dekuNukem/USB4VC/captures/m0110/tmk_firrmware_hhkb_teensy2_m0110.c at master · altercation_tmk_firrmware_hhkb_teensy2_files/9824478.png

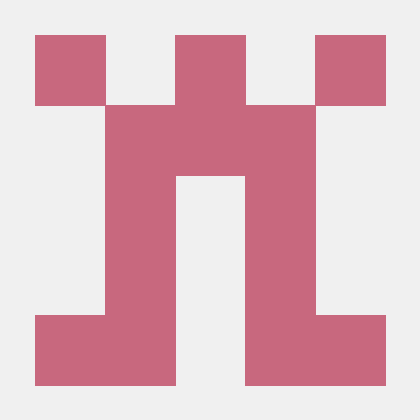
captures/m0110/tmk_firrmware_hhkb_teensy2_m0110.c at master · altercation_tmk_firrmware_hhkb_teensy2_files/9824478.png
