dekuNukem/USB4VC/firmware/apple_lisa_mac_adb/lisa_keycode.png

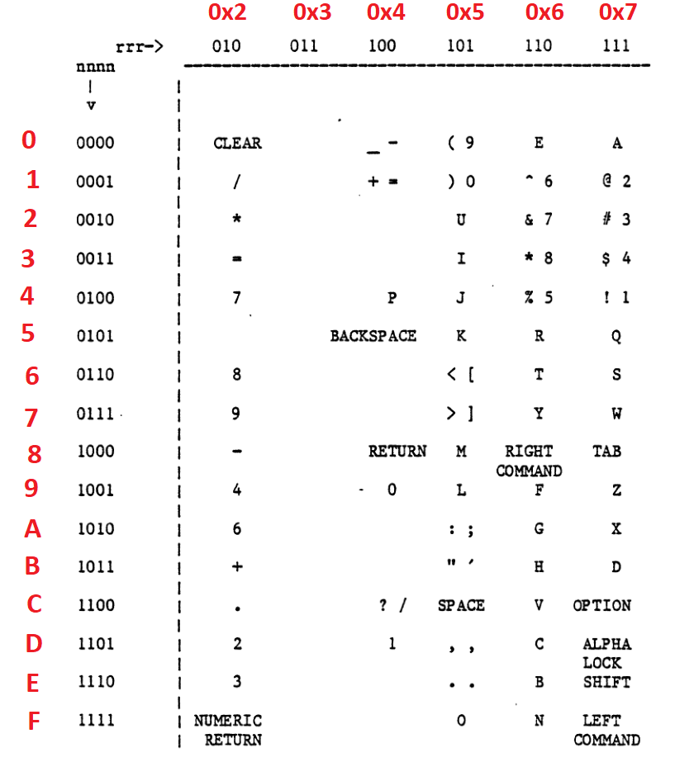
firmware/apple_lisa_mac_adb/lisa_keycode.png
