dekuNukem/USB4VC/pcb/plates/dimension photo.png

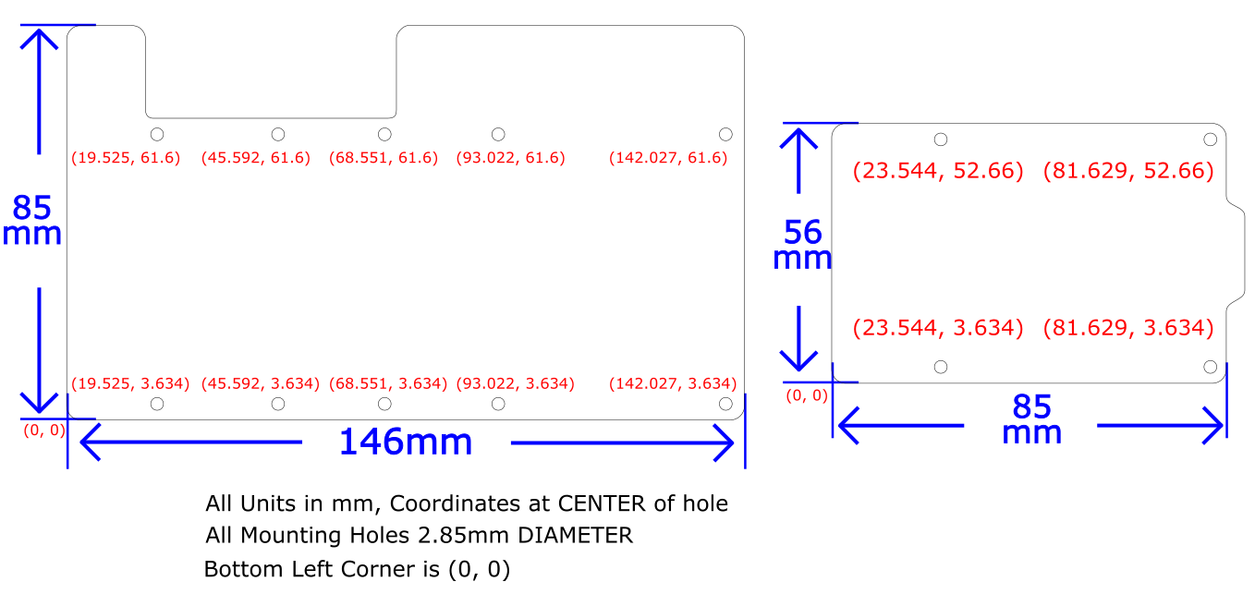
pcb/plates/dimension photo.png
