dekuNukem/USB4VC/photos/'8042' PS_2 Controller - OSDev Wiki_files/At-kbc.png

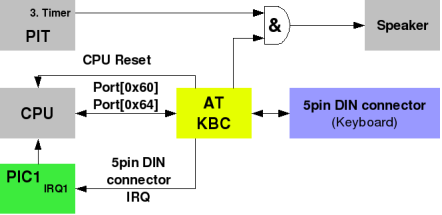
photos/'8042' PS_2 Controller - OSDev Wiki_files/At-kbc.png
