dekuNukem/USB4VC/photos/adbpc.jpeg

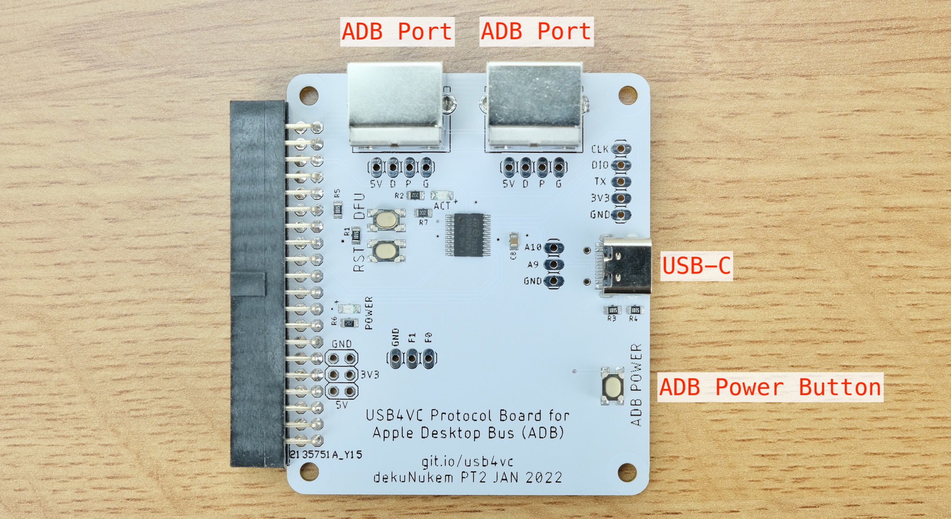
photos/adbpc.jpeg
