dekuNukem/USB4VC/photos/bbadb.jpeg

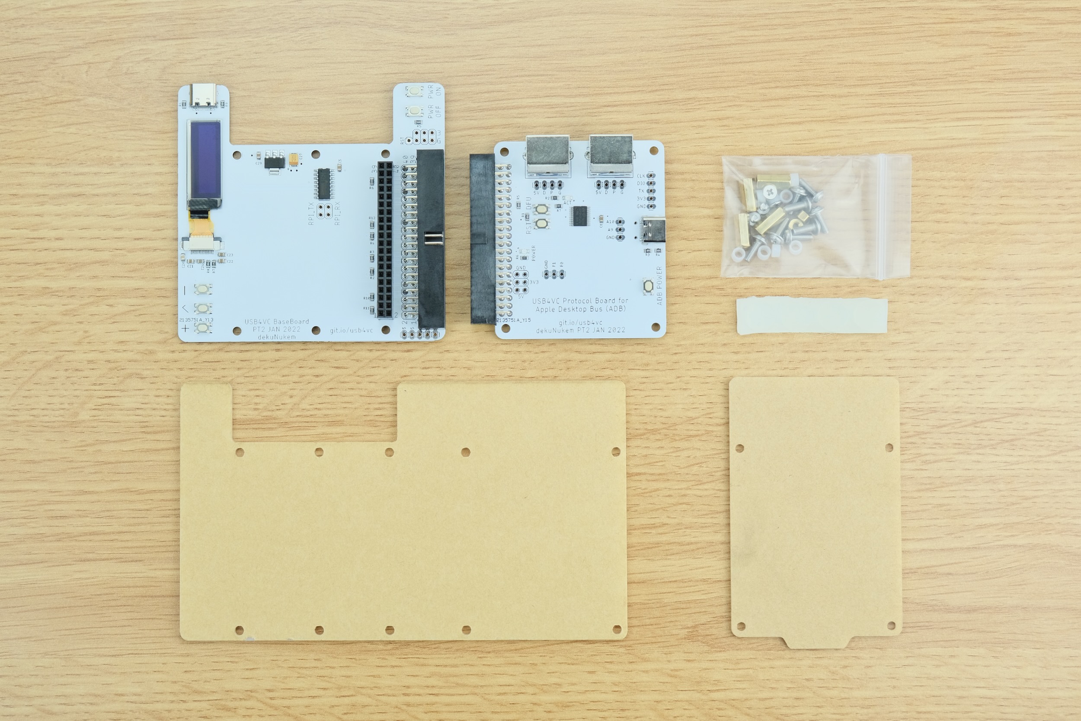
photos/bbadb.jpeg
