dekuNukem/USB4VC/photos/bbpc.jpeg

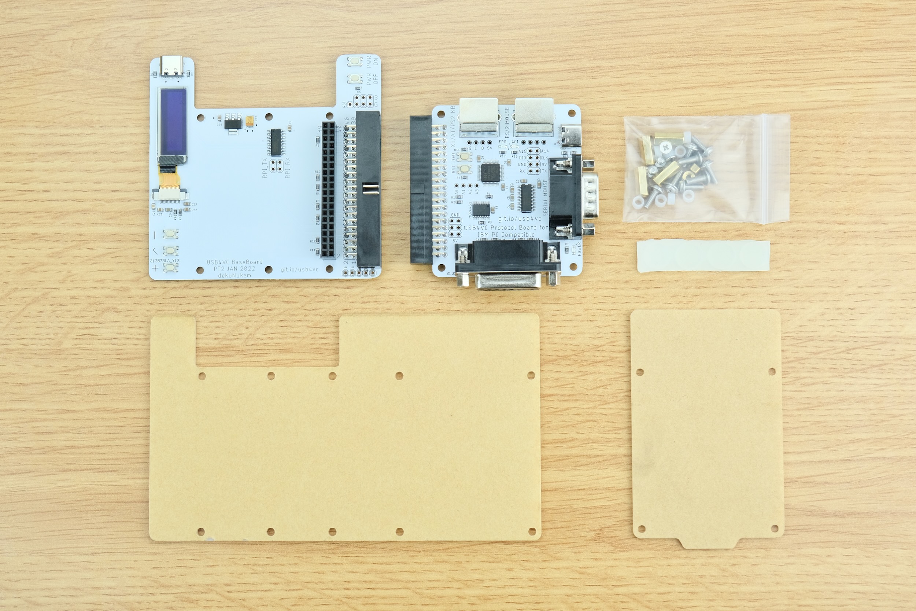
photos/bbpc.jpeg
