dekuNukem/USB4VC/photos/bbpcadb.jpeg

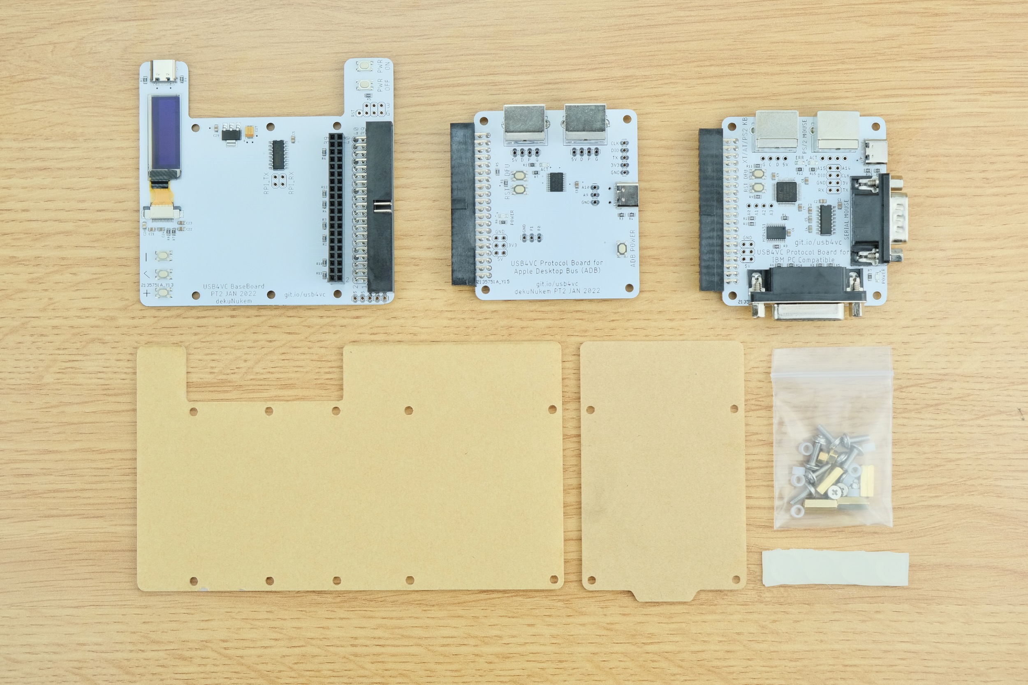
photos/bbpcadb.jpeg
