dekuNukem/USB4VC/photos/macclassic.jpeg

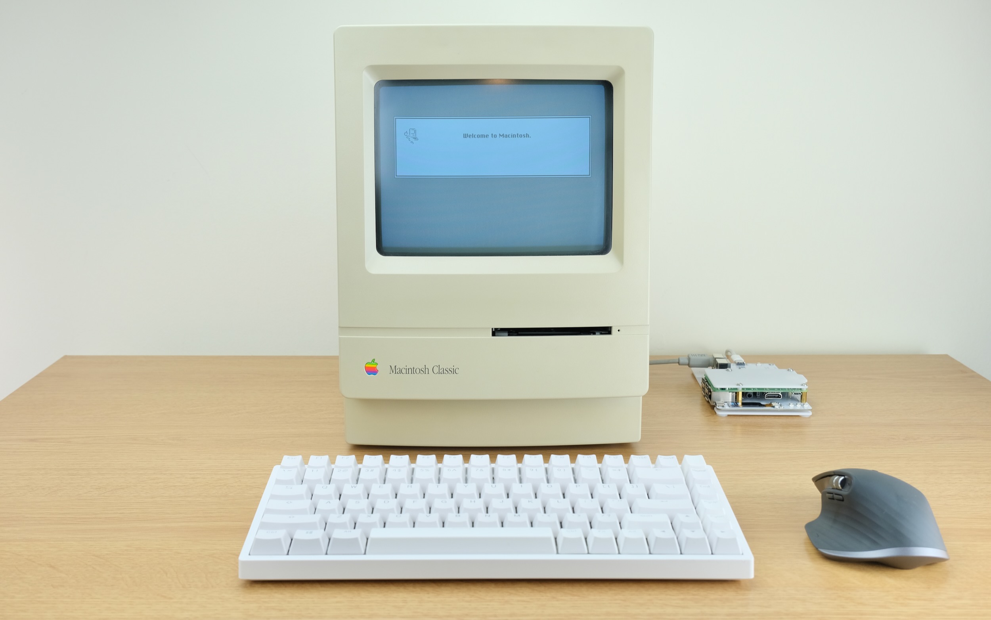
photos/macclassic.jpeg
