dekuNukem/USB4VC/photos/rpitest.jpeg

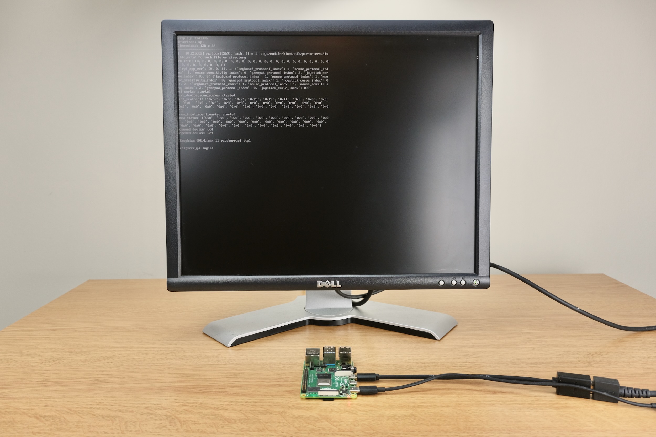
photos/rpitest.jpeg
