dekuNukem/USB4VC/photos/usbdisk.png

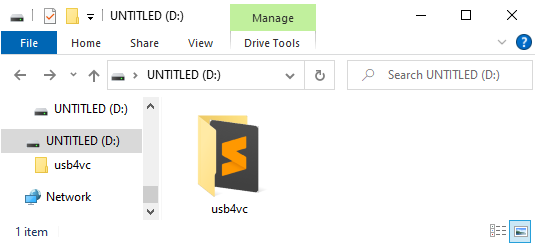
photos/usbdisk.png
