dekuNukem/USB4VC/photos/usboled.jpeg

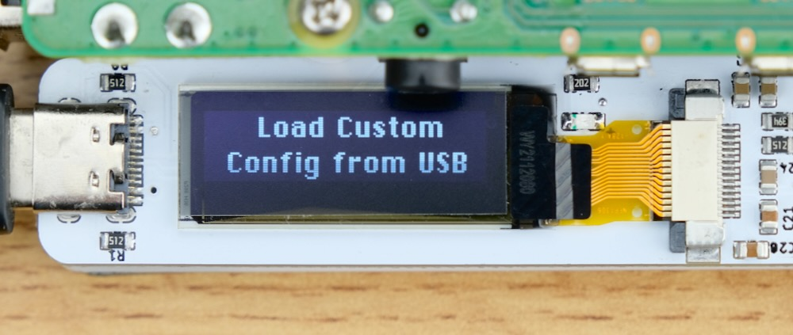
photos/usboled.jpeg
