dekuNukem/USB4VC/photos/video_thumb.png

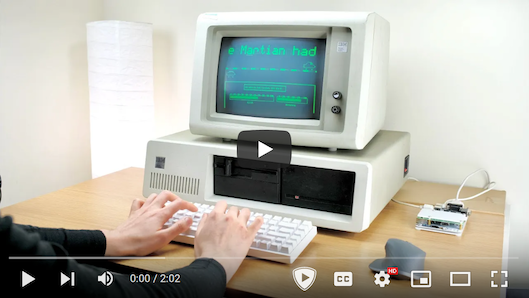
photos/video_thumb.png
