dekuNukem/USB4VC/photos/xbupdate.png

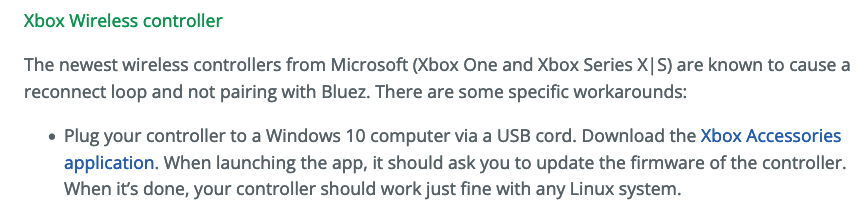
photos/xbupdate.png
