dekuNukem/USB4VC/resources/bezier curve - Inverse round corners with Inkscape - Graphic Design Stack Exchange_files/bnUZU.jpg

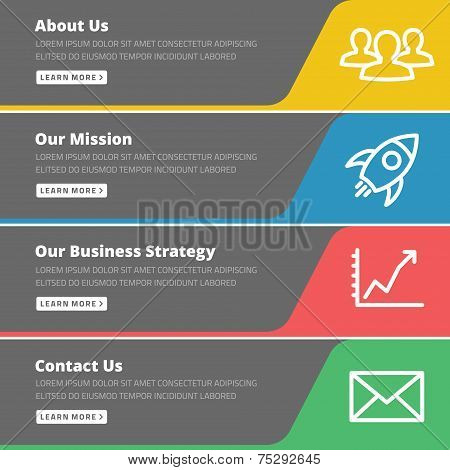
resources/bezier curve - Inverse round corners with Inkscape - Graphic Design Stack Exchange_files/bnUZU.jpg
