dekuNukem/USB4VC/resources/IBM 1390876 keyboard_files/1390876.jpg

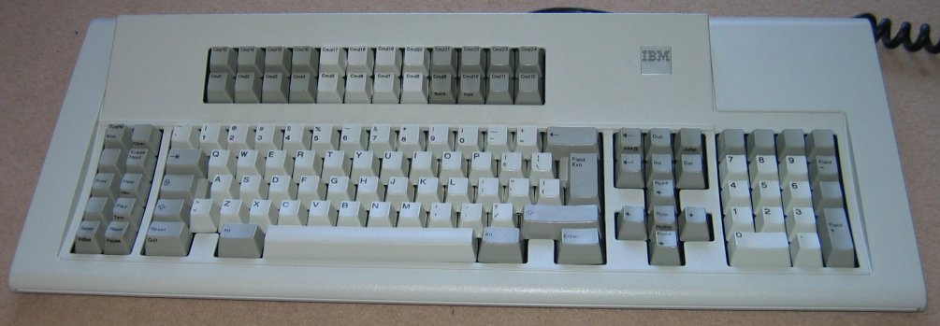
resources/IBM 1390876 keyboard_files/1390876.jpg
