dekuNukem/USB4VC/resources/IBM 1397000 keyboard_files/1397000.jpg

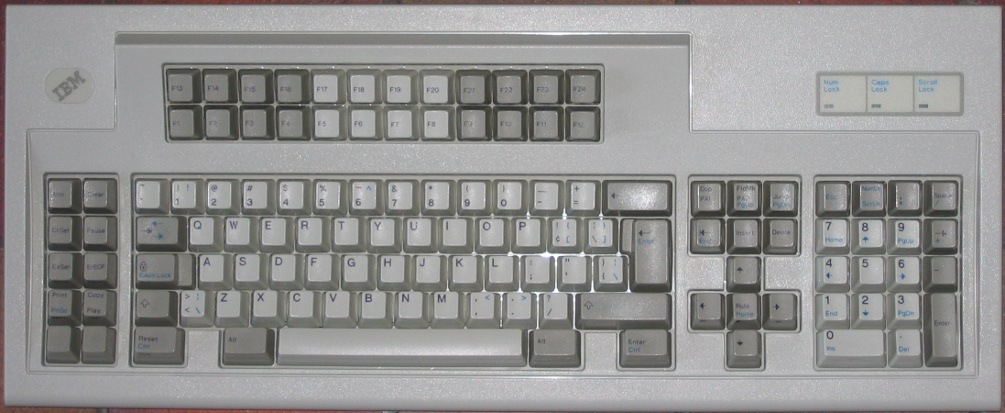
resources/IBM 1397000 keyboard_files/1397000.jpg
