dekuNukem/USB4VC/resources/IBM PC AT Keyboard Protocol · tmk_tmk_keyboard Wiki_files/687474703a2f2f7a6967736f772e6a702f696d672e7068703f613d612666.jpg

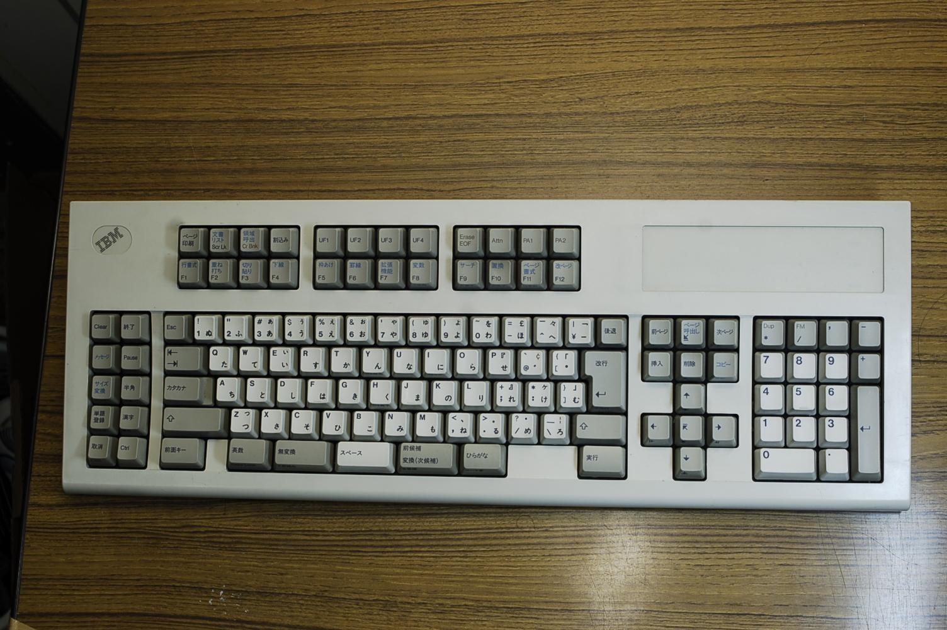
resources/IBM PC AT Keyboard Protocol · tmk_tmk_keyboard Wiki_files/687474703a2f2f7a6967736f772e6a702f696d672e7068703f613d612666.jpg
