dekuNukem/USB4VC/resources/IBM PC AT Keyboard Protocol · tmk_tmk_keyboard Wiki_files/687474703a2f2f626c6f672d696d67732d37352e6663322e636f6d2f6b2f.jpg

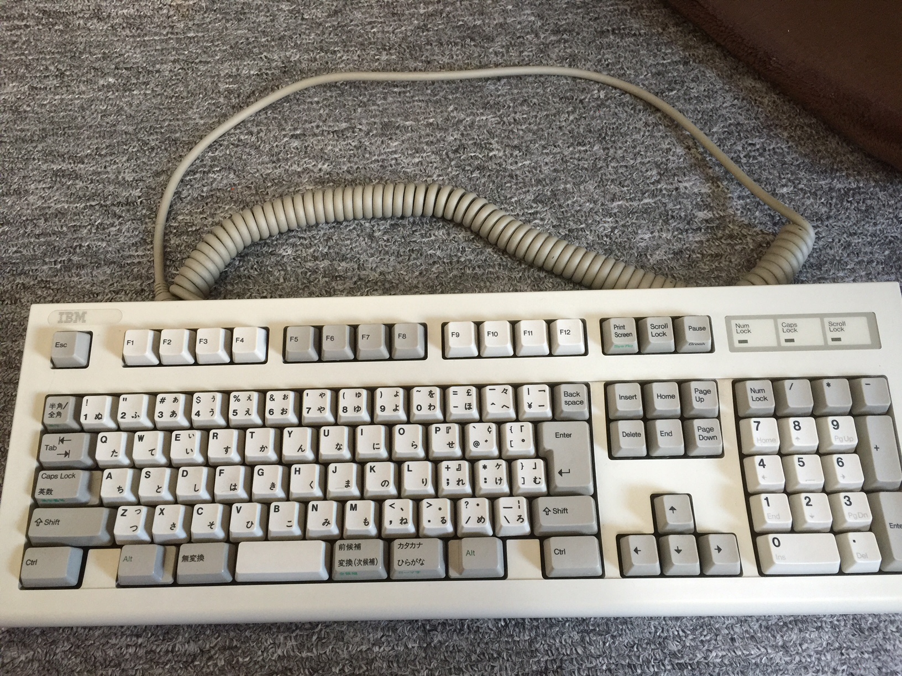
resources/IBM PC AT Keyboard Protocol · tmk_tmk_keyboard Wiki_files/687474703a2f2f626c6f672d696d67732d37352e6663322e636f6d2f6b2f.jpg
