dekuNukem/USB4VC/resources/IBM PC AT Keyboard Protocol · tmk_tmk_keyboard Wiki_files/687474703a2f2f7777772e6b6264626162656c2e6f72672f7369676e616c.png

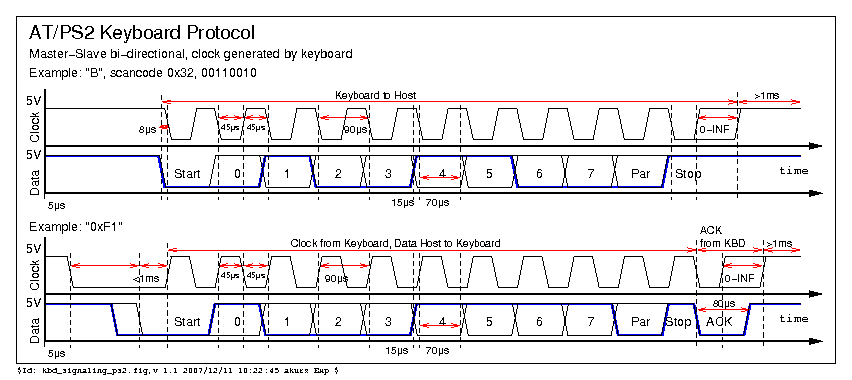
resources/IBM PC AT Keyboard Protocol · tmk_tmk_keyboard Wiki_files/687474703a2f2f7777772e6b6264626162656c2e6f72672f7369676e616c.png
