dekuNukem/USB4VC/resources/IBM PC AT Keyboard Protocol · tmk_tmk_keyboard Wiki_files/68747470733a2f2f692e696d6775722e636f6d2f34374b734c534c2e706e.png

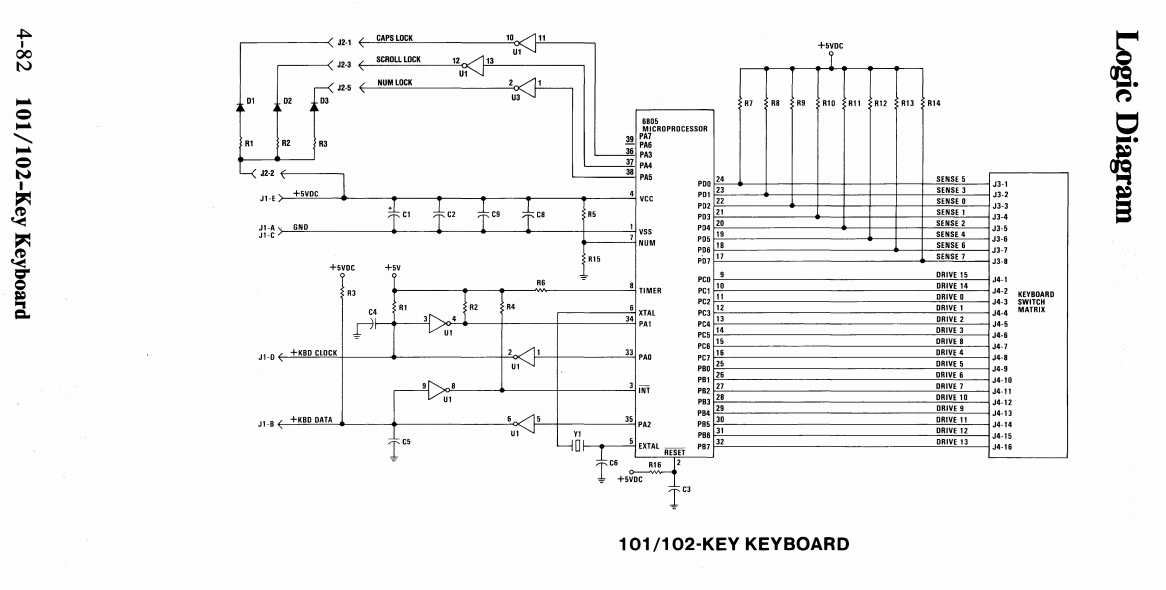
resources/IBM PC AT Keyboard Protocol · tmk_tmk_keyboard Wiki_files/68747470733a2f2f692e696d6775722e636f6d2f34374b734c534c2e706e.png
