dekuNukem/USB4VC/resources/IBM PC AT Keyboard Protocol · tmk_tmk_keyboard Wiki_files/68747470733a2f2f75706c6f61642e77696b696d656469612e6f72672f77.jpg

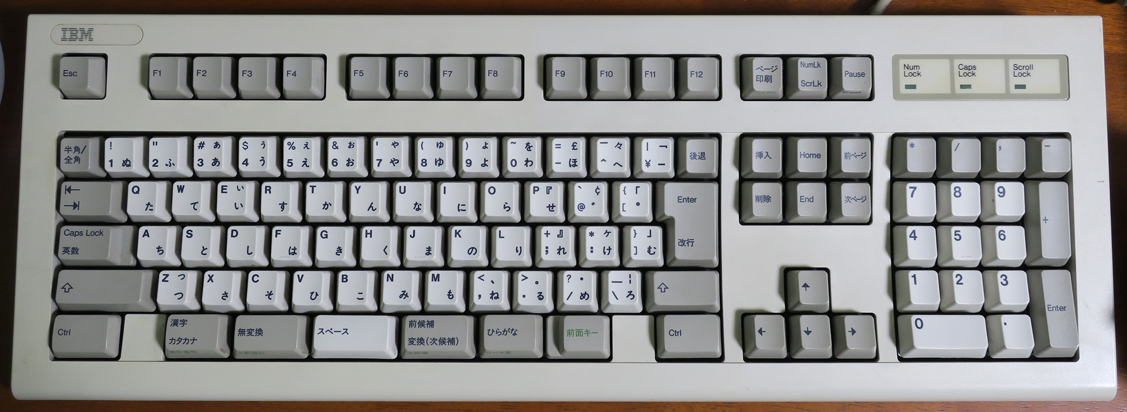
resources/IBM PC AT Keyboard Protocol · tmk_tmk_keyboard Wiki_files/68747470733a2f2f75706c6f61642e77696b696d656469612e6f72672f77.jpg
