dekuNukem/USB4VC/resources/IBM PC AT Keyboard Protocol · tmk_tmk_keyboard Wiki_files/68747470733a2f2f7062732e7477696d672e636f6d2f6d656469612f454f.jpg

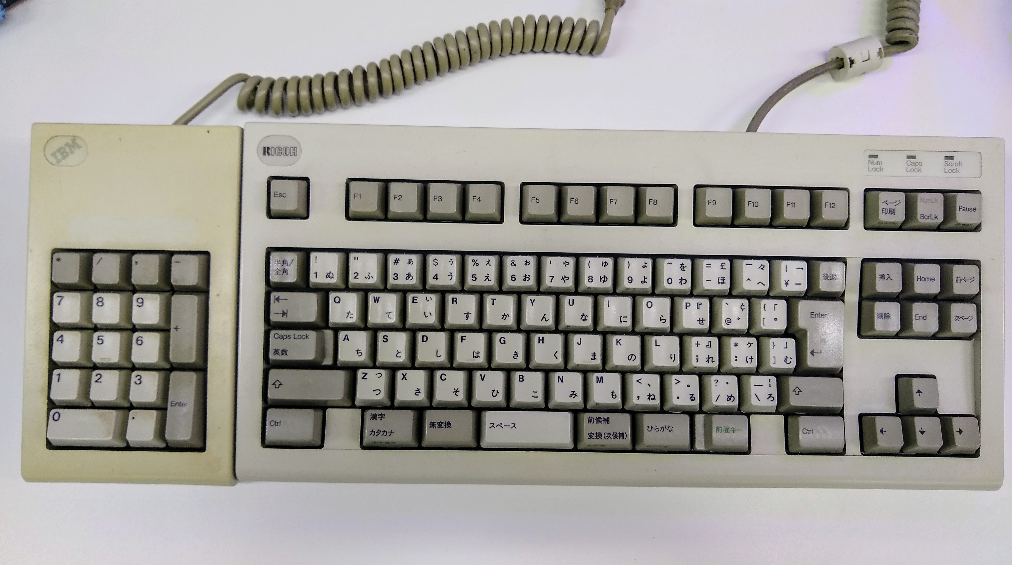
resources/IBM PC AT Keyboard Protocol · tmk_tmk_keyboard Wiki_files/68747470733a2f2f7062732e7477696d672e636f6d2f6d656469612f454f.jpg
