dekuNukem/USB4VC/resources/index_files/reconbot.png

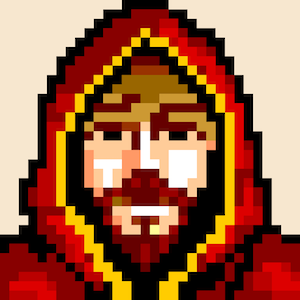
resources/index_files/reconbot.png
