dekuNukem/USB4VC/resources/lichee pi pinout.png

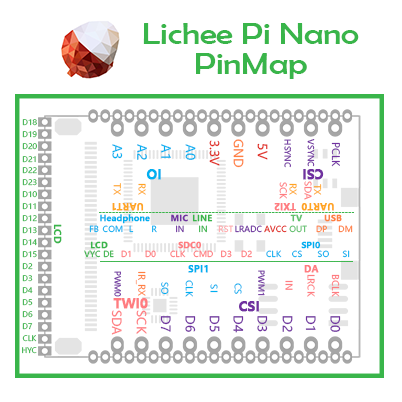
resources/lichee pi pinout.png
