dekuNukem/USB4VC/resources/O1CN01AOr2Mo1PcqBe09GLz_!!914671862.jpg

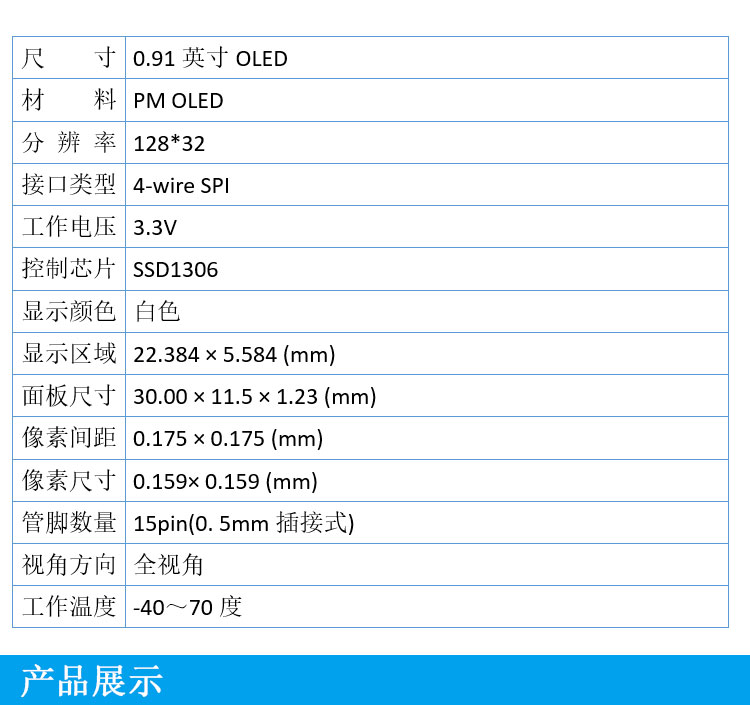
resources/O1CN01AOr2Mo1PcqBe09GLz_!!914671862.jpg
