dekuNukem/USB4VC/resources/png_to_curve/bitmap.png

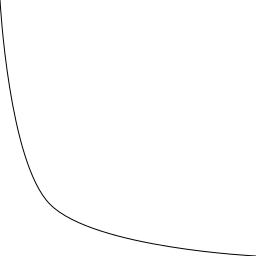
resources/png_to_curve/bitmap.png
