dekuNukem/USB4VC/resources/png_to_curve/ccc.png

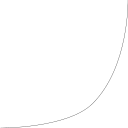
resources/png_to_curve/ccc.png
