dekuNukem/USB4VC/resources/Raspberry-Pi-1-2-3-Model-B.jpg

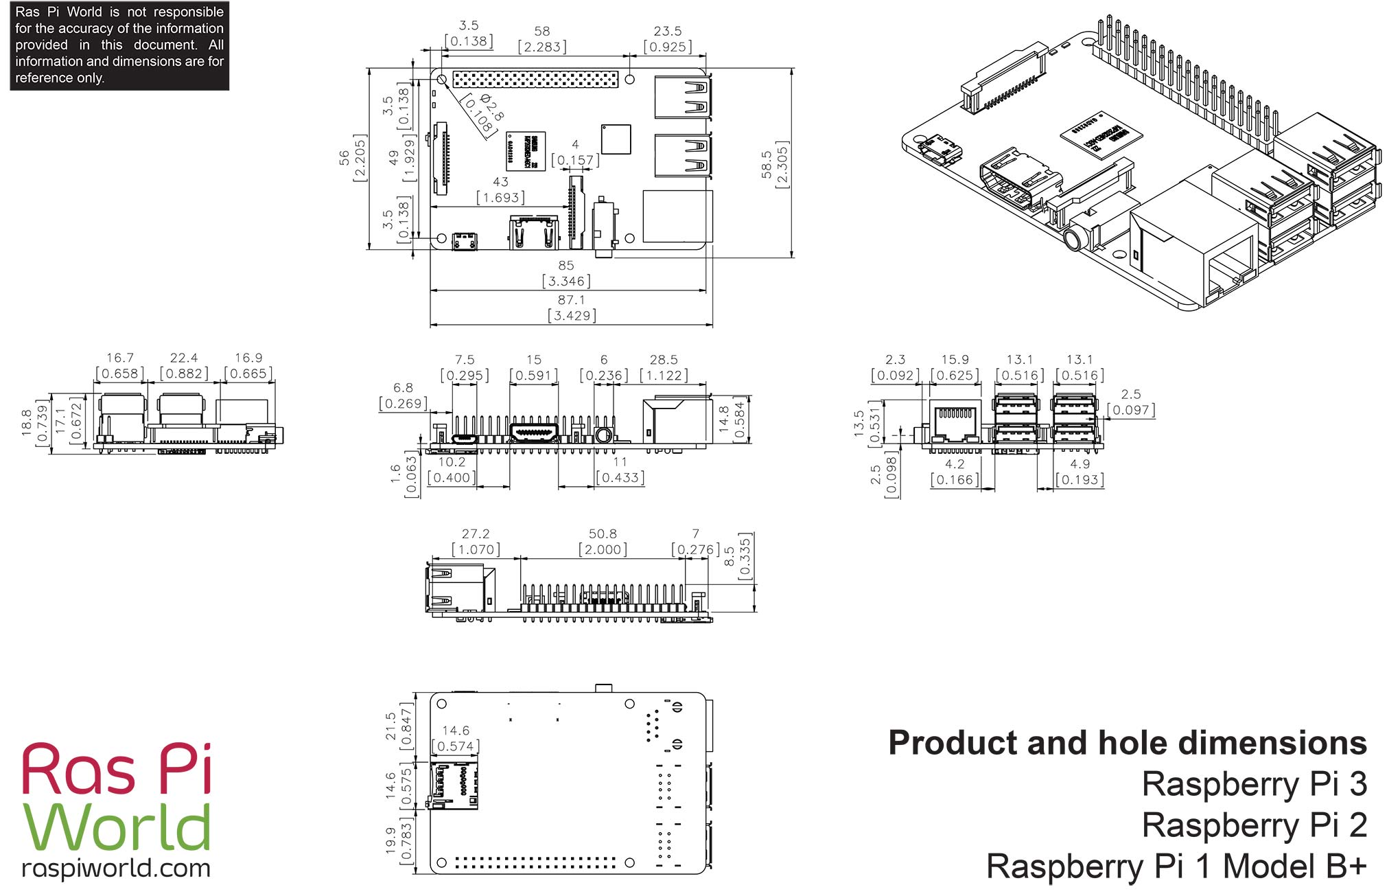
resources/Raspberry-Pi-1-2-3-Model-B.jpg
