dekuNukem/USB4VC/resources/Scan Codes Demystified_files/83c.gif

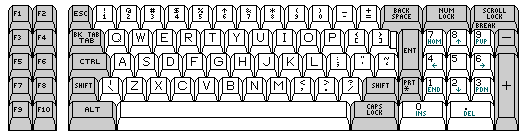
resources/Scan Codes Demystified_files/83c.gif
