dekuNukem/USB4VC/resources/Scan Codes Demystified_files/84c.gif

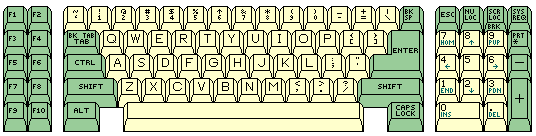
resources/Scan Codes Demystified_files/84c.gif
