dekuNukem/USB4VC/resources/Scan Codes Demystified_files/122_apl.gif

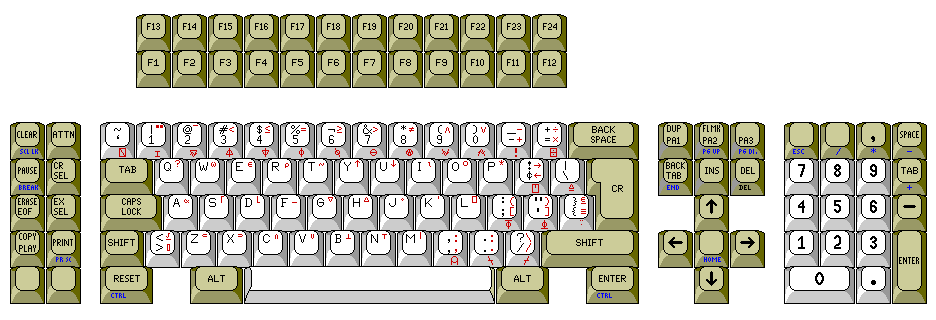
resources/Scan Codes Demystified_files/122_apl.gif
