dekuNukem/USB4VC/resources/Scan Codes Demystified_files/122hc.gif

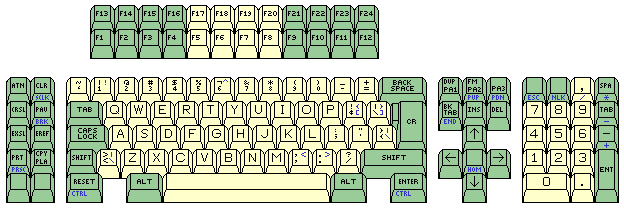
resources/Scan Codes Demystified_files/122hc.gif
