dekuNukem/USB4VC/resources/Scan Codes Demystified_files/122j.gif

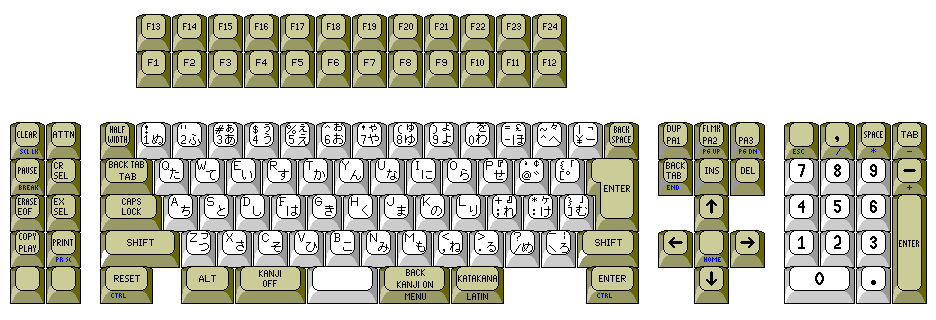
resources/Scan Codes Demystified_files/122j.gif
