dekuNukem/USB4VC/resources/Scan Codes Demystified_files/3270e.gif

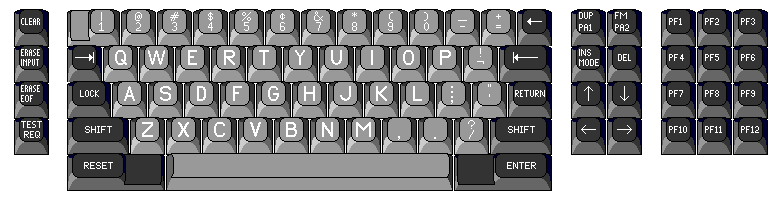
resources/Scan Codes Demystified_files/3270e.gif
