dekuNukem/USB4VC/resources/Scan Codes Demystified_files/memx122.jpg

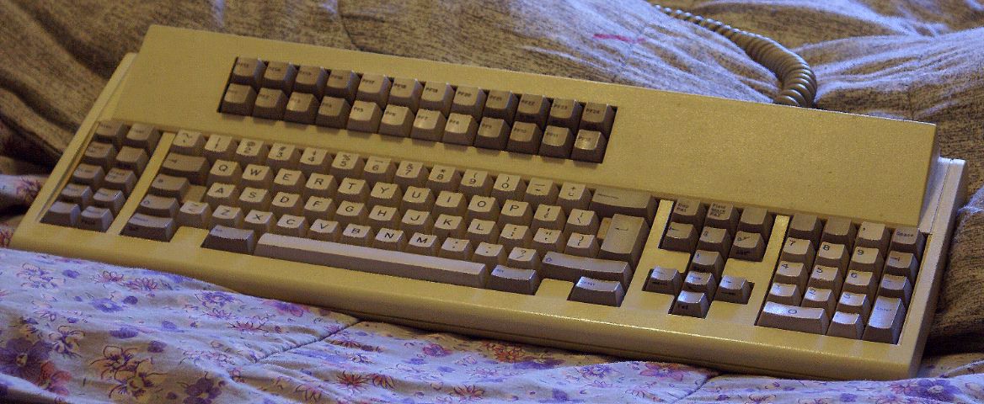
resources/Scan Codes Demystified_files/memx122.jpg
