dekuNukem/USB4VC/resources/Scan Codes Demystified_files/pca70.gif

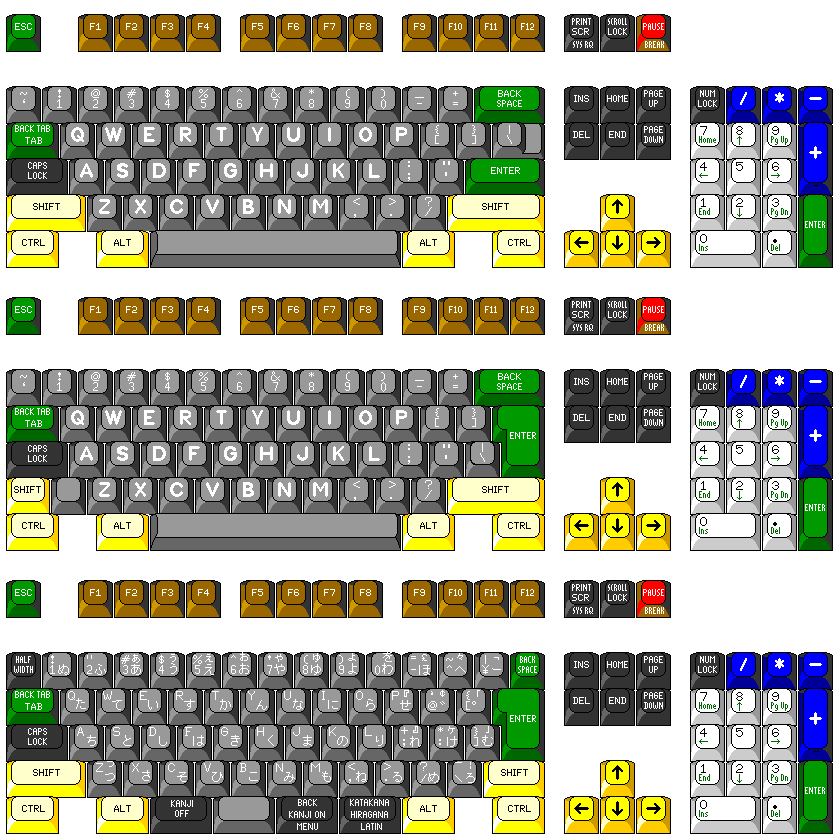
resources/Scan Codes Demystified_files/pca70.gif
