dekuNukem/USB4VC/resources/Scan Codes Demystified_files/pca72.gif

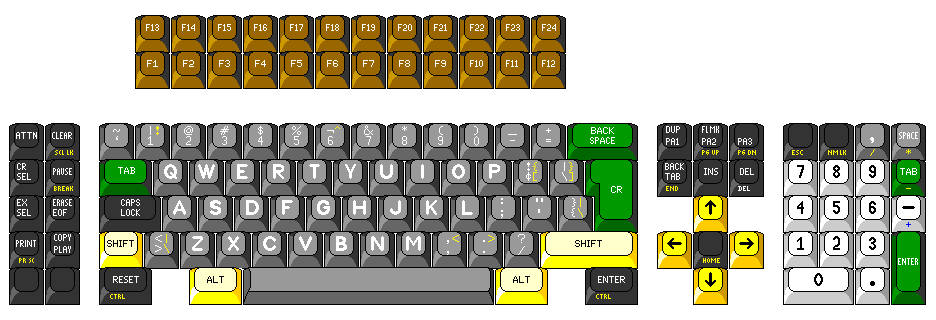
resources/Scan Codes Demystified_files/pca72.gif
