dekuNukem/USB4VC/resources/Scan Codes Demystified_files/ssk.gif

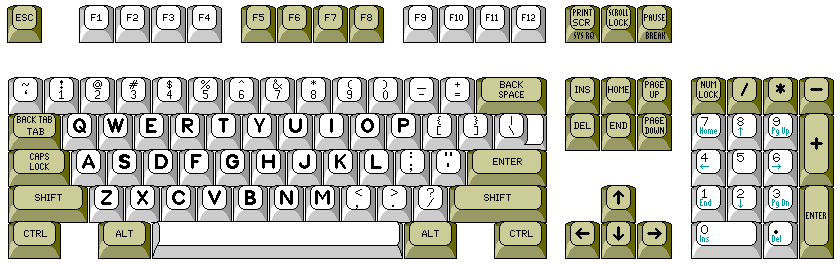
resources/Scan Codes Demystified_files/ssk.gif
