dekuNukem/USB4VC/resources/Screenshot_from_2019-06-25_14-10-06_d96020f3-4f37-48f7-af61-e2e9a573ea04.webp

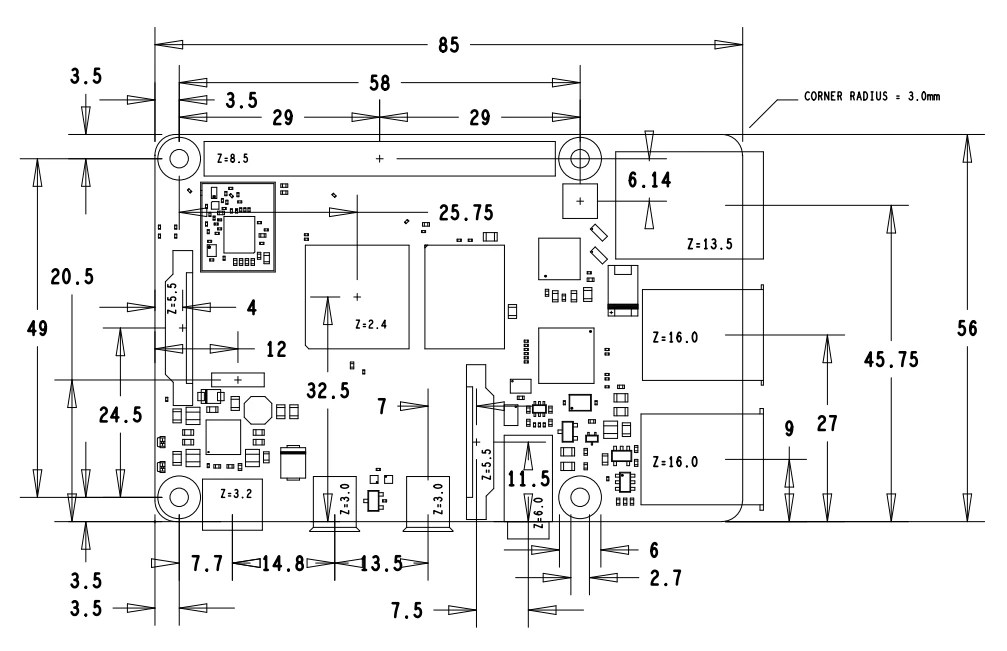
resources/Screenshot_from_2019-06-25_14-10-06_d96020f3-4f37-48f7-af61-e2e9a573ea04.webp
