dekuNukem/USB4VC/resources/The PS_2 Mouse_Keyboard Protocol_files/ps2.JPG

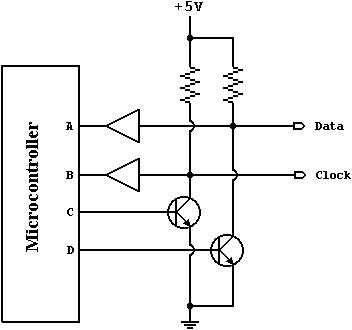
resources/The PS_2 Mouse_Keyboard Protocol_files/ps2.JPG
