dekuNukem/USB4VC/resources/The PS_2 Mouse_Keyboard Protocol_files/qscope.JPG

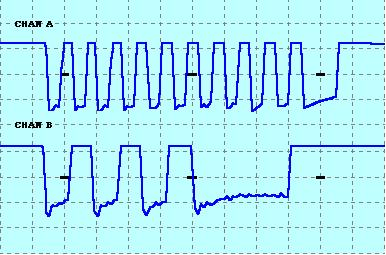
resources/The PS_2 Mouse_Keyboard Protocol_files/qscope.JPG
