dekuNukem/USB4VC/resources/The PS_2 Mouse_Keyboard Protocol_files/waveform1.jpg

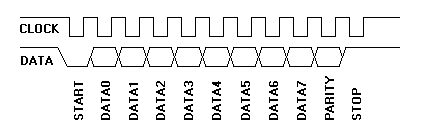
resources/The PS_2 Mouse_Keyboard Protocol_files/waveform1.jpg
