dekuNukem/USB4VC/resources/The PS_2 Mouse_Keyboard Protocol_files/waveform2.jpg

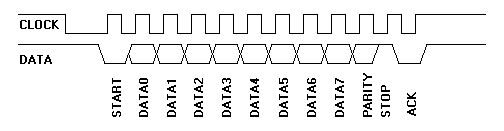
resources/The PS_2 Mouse_Keyboard Protocol_files/waveform2.jpg
