dekuNukem/USB4VC/resources/The PS_2 Mouse_Keyboard Protocol_files/waveform3.jpg

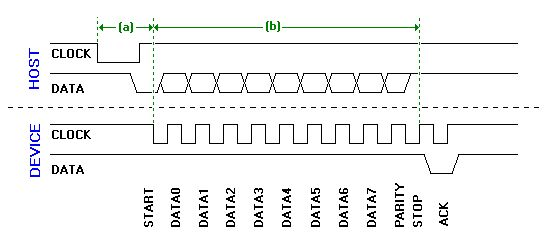
resources/The PS_2 Mouse_Keyboard Protocol_files/waveform3.jpg
