dekuNukem/USB4VC/resources/RedBoard-Qwiic.pdf

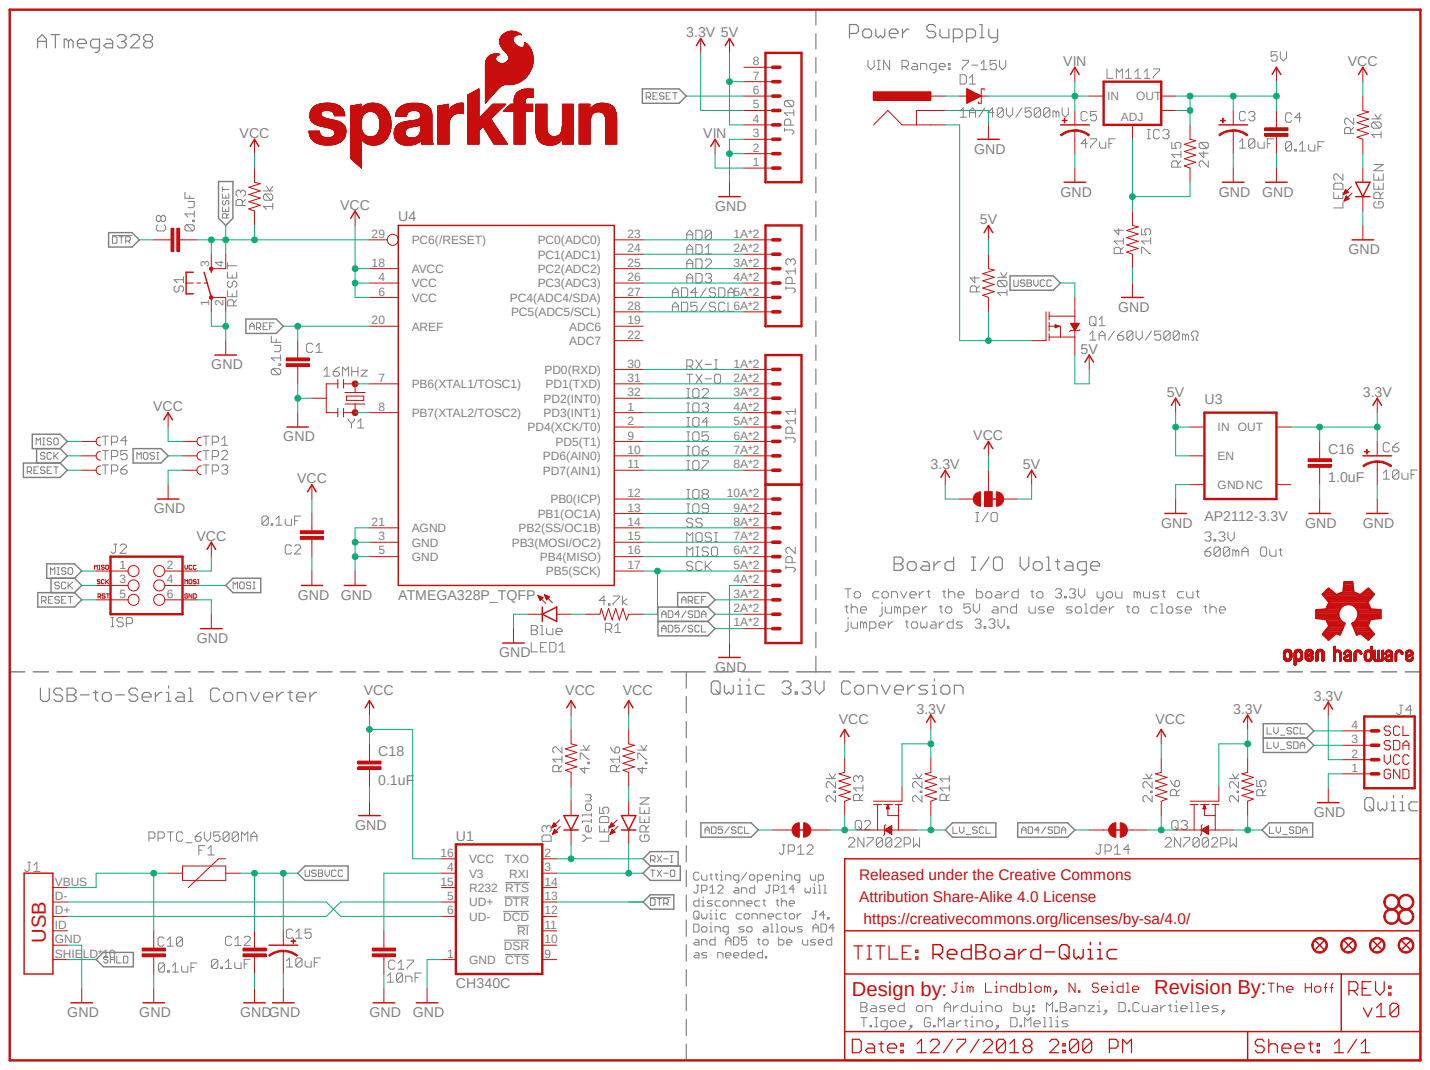
[picture p119: page 1]
GND; GND GND; GNDGND; VIN; ATMEGA328P_TQFP; GND AP2112-3.3V; VCC; ADJ; OUT; PB5(SCK); PB7(XTAL2/TOSC2) 8; PB6(XTAL1/TOSC1) 7; GND 3 GND 5; VCC 4 VCC 6; AGND 21; AREF 20; AVCC 18; PB4(MISO); 16 PB3(MOSI/OC2); 13 PB0(ICP); PD7(AIN1); 11 PD6(AIN0); 9 PD4(XCK/T0); 2 PD3(INT1); 1 PD2(INT0); 32 PD1(TXD); 31 PD0(RXD); ADC7; 22 ADC6; 19 PC5(ADC5/SCL); 28 PC4(ADC4/SDA); 27 PC3(ADC3); 26 PC2(ADC2); 25 PC1(ADC1); 24 PC0(ADC0); 23 PC6(/RESET) 29; VBUS; SHIELD*10; CTS; DCD; DSR; DTR; RTS; GND 1; RXI; 3 TXO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

Released under the Creative Commons
Attribution Share-Alike 4.0 License
https://creativecommons.org/licenses/by-sa/4.0/
