dekuNukem/USB4VC/resources/lichee_nano_new.pdf

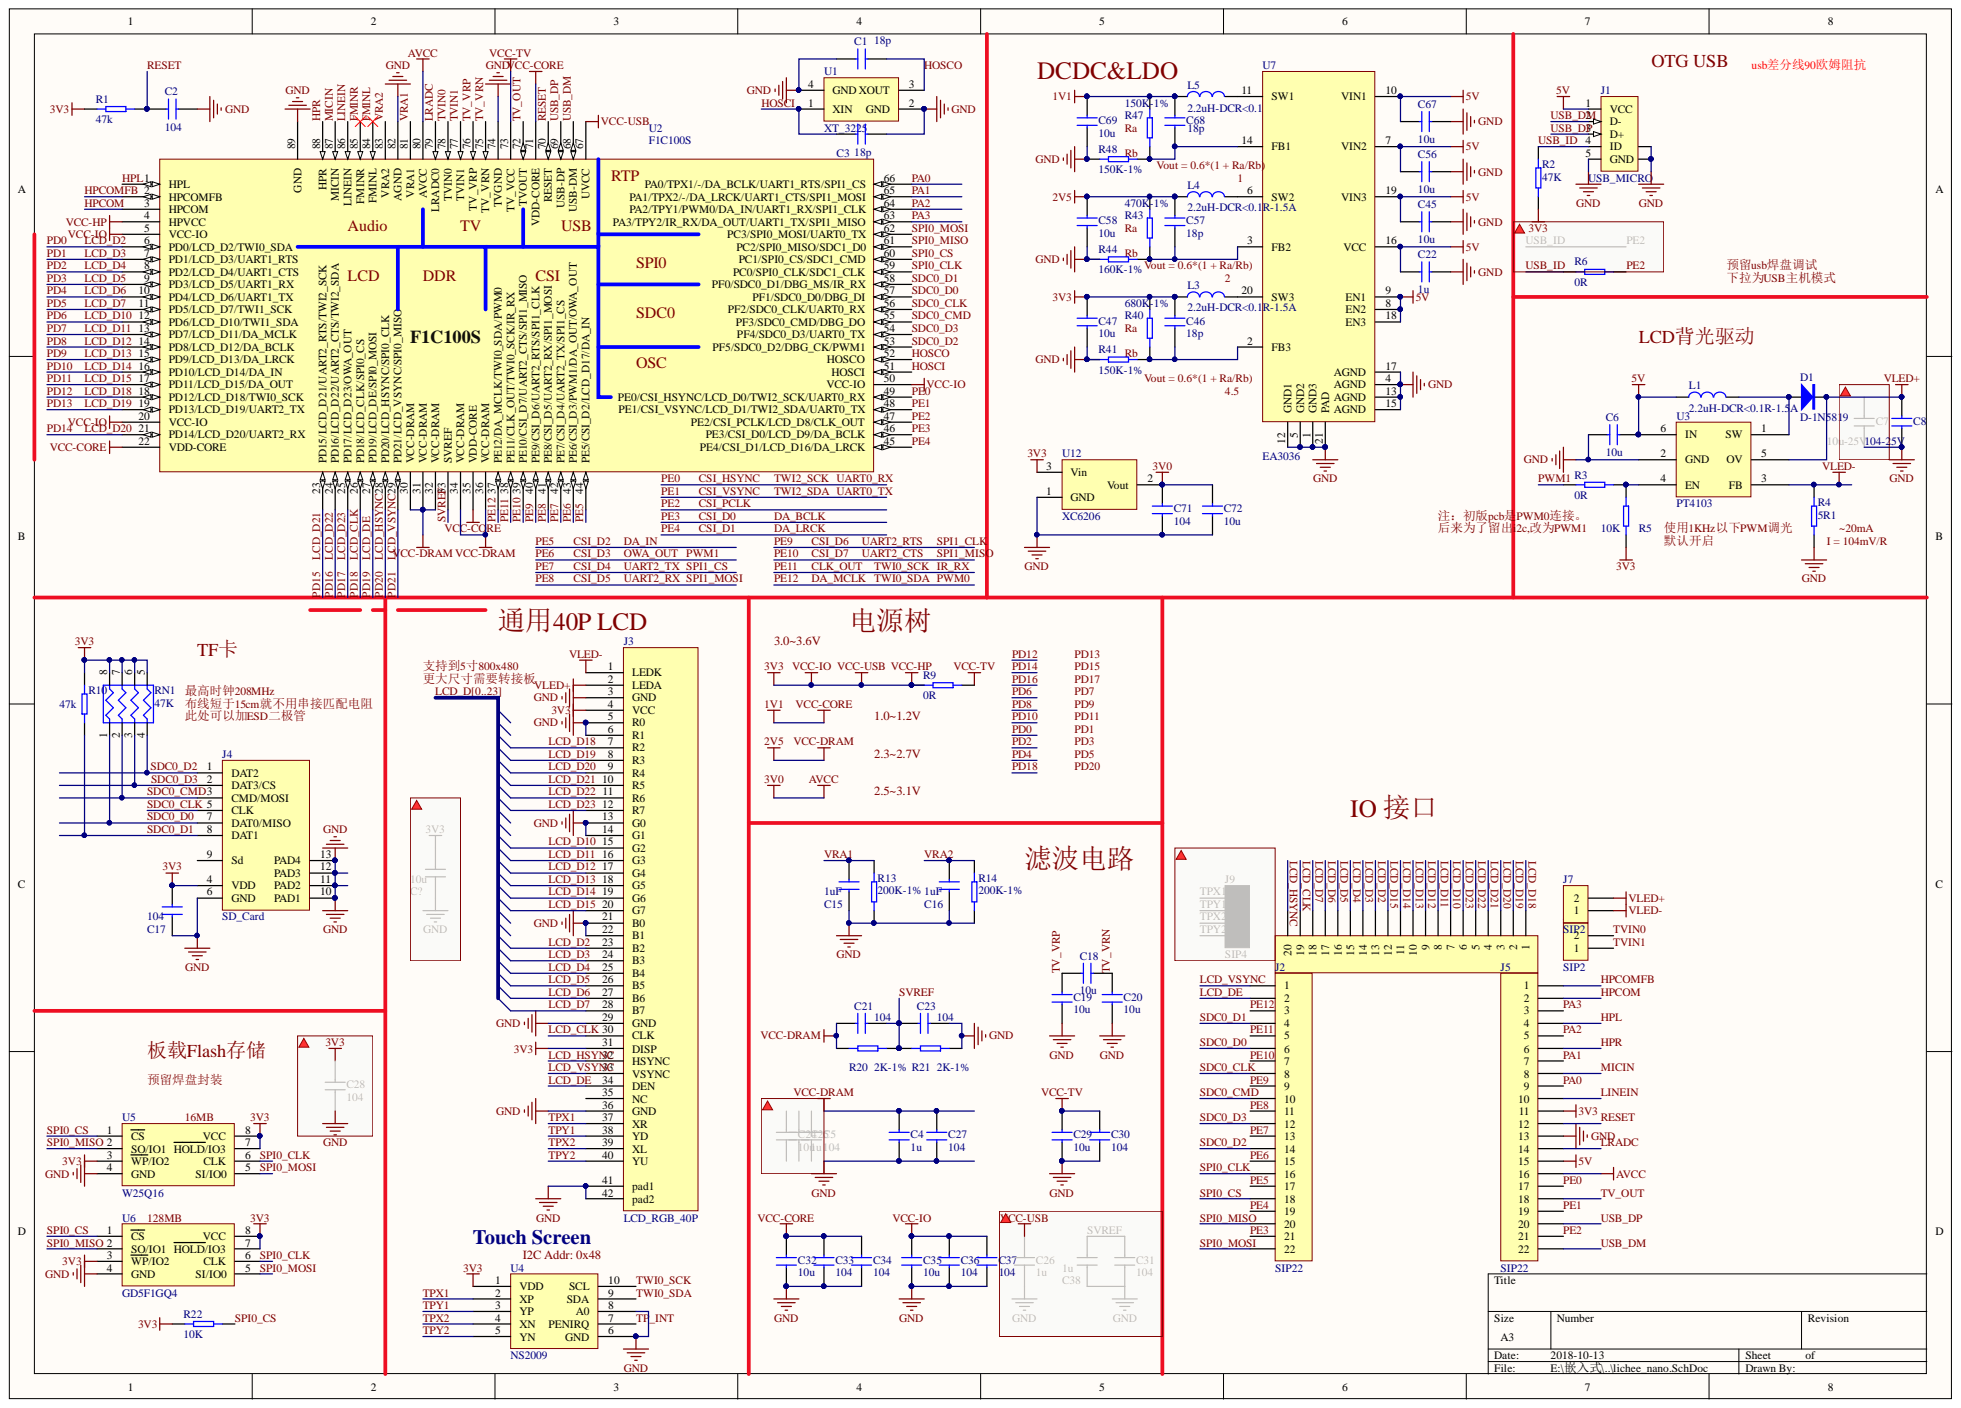
[picture p120: page 1]

UVCC 67 USB-DM 68 USB-DP 69 RESET 70 VDD-CORE 71 TVOUT 72 TV_VCC 73 TVGND 74 TV_VRN 75 TV_VRP 76 TVIN1 77 TVIN0 78 LRADC0 79 AVCC 80 VRA1 81 AGND 82 VRA2 83 FMINL 84 FMINR 85 LINEIN 86 MICIN 87 HPR 88

GND Vout = 0.6*(1 + Ra/Rb)

VCC-DRAM
