dekuNukem/USB4VC/resources/0.91OLED插接15pin-SSD1306技术资料/SPI接口原理图.pdf

# 中景园电子0.91寸SPI接口OLED显示屏模块原理图

# 淘宝地址：http://shop73023976.taobao.com/?spm=a1z10.1.0.0.byBTLt&v=1

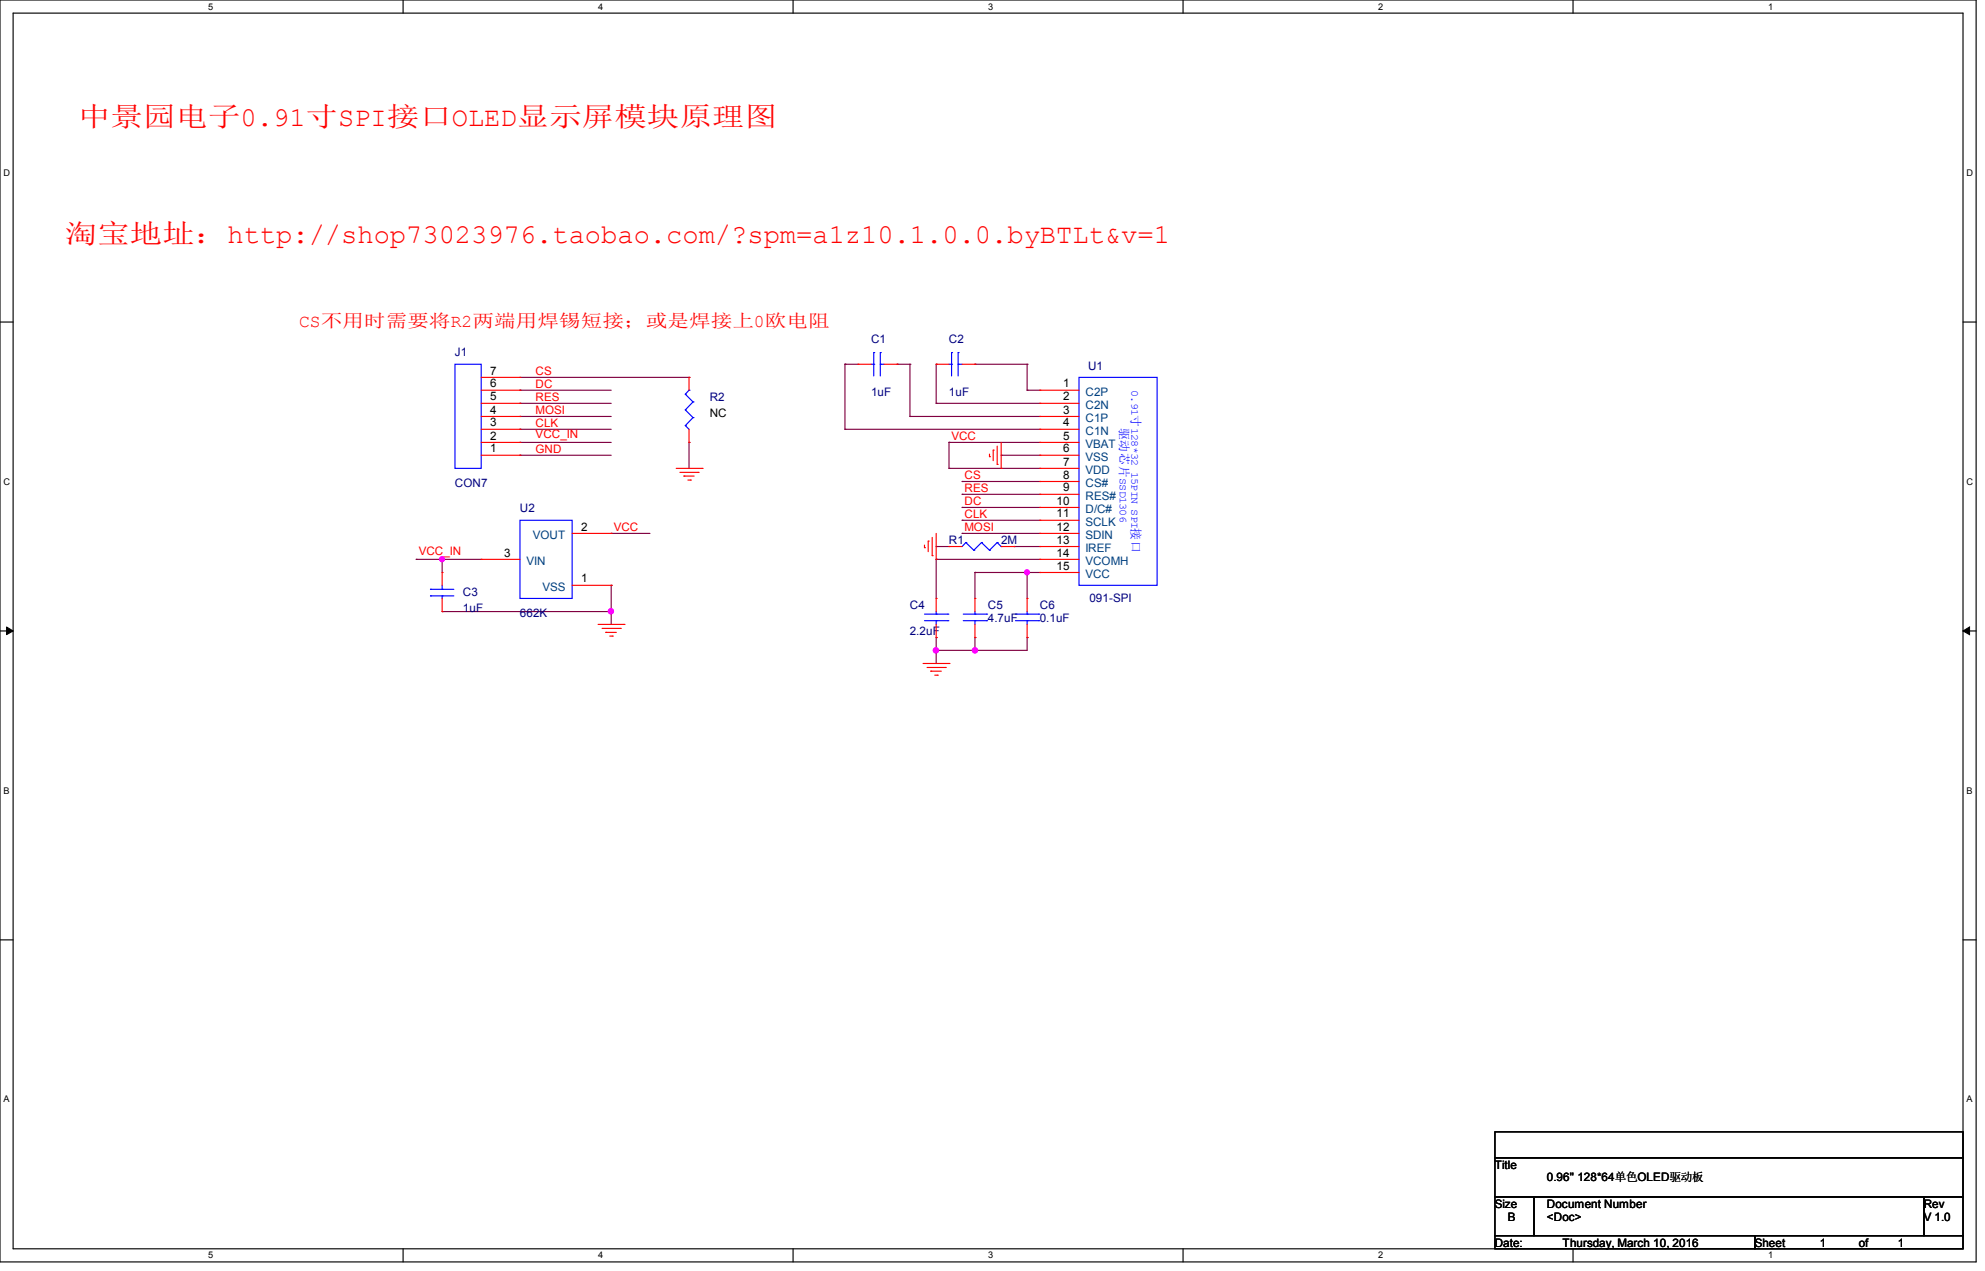
[picture p123: page 1]
