dekuNukem/USB4VC/pcb/bbc_micro/bbc_micro.brd

## EAGLE design pcb/bbc_micro/bbc_micro.brd (2022-09-27)

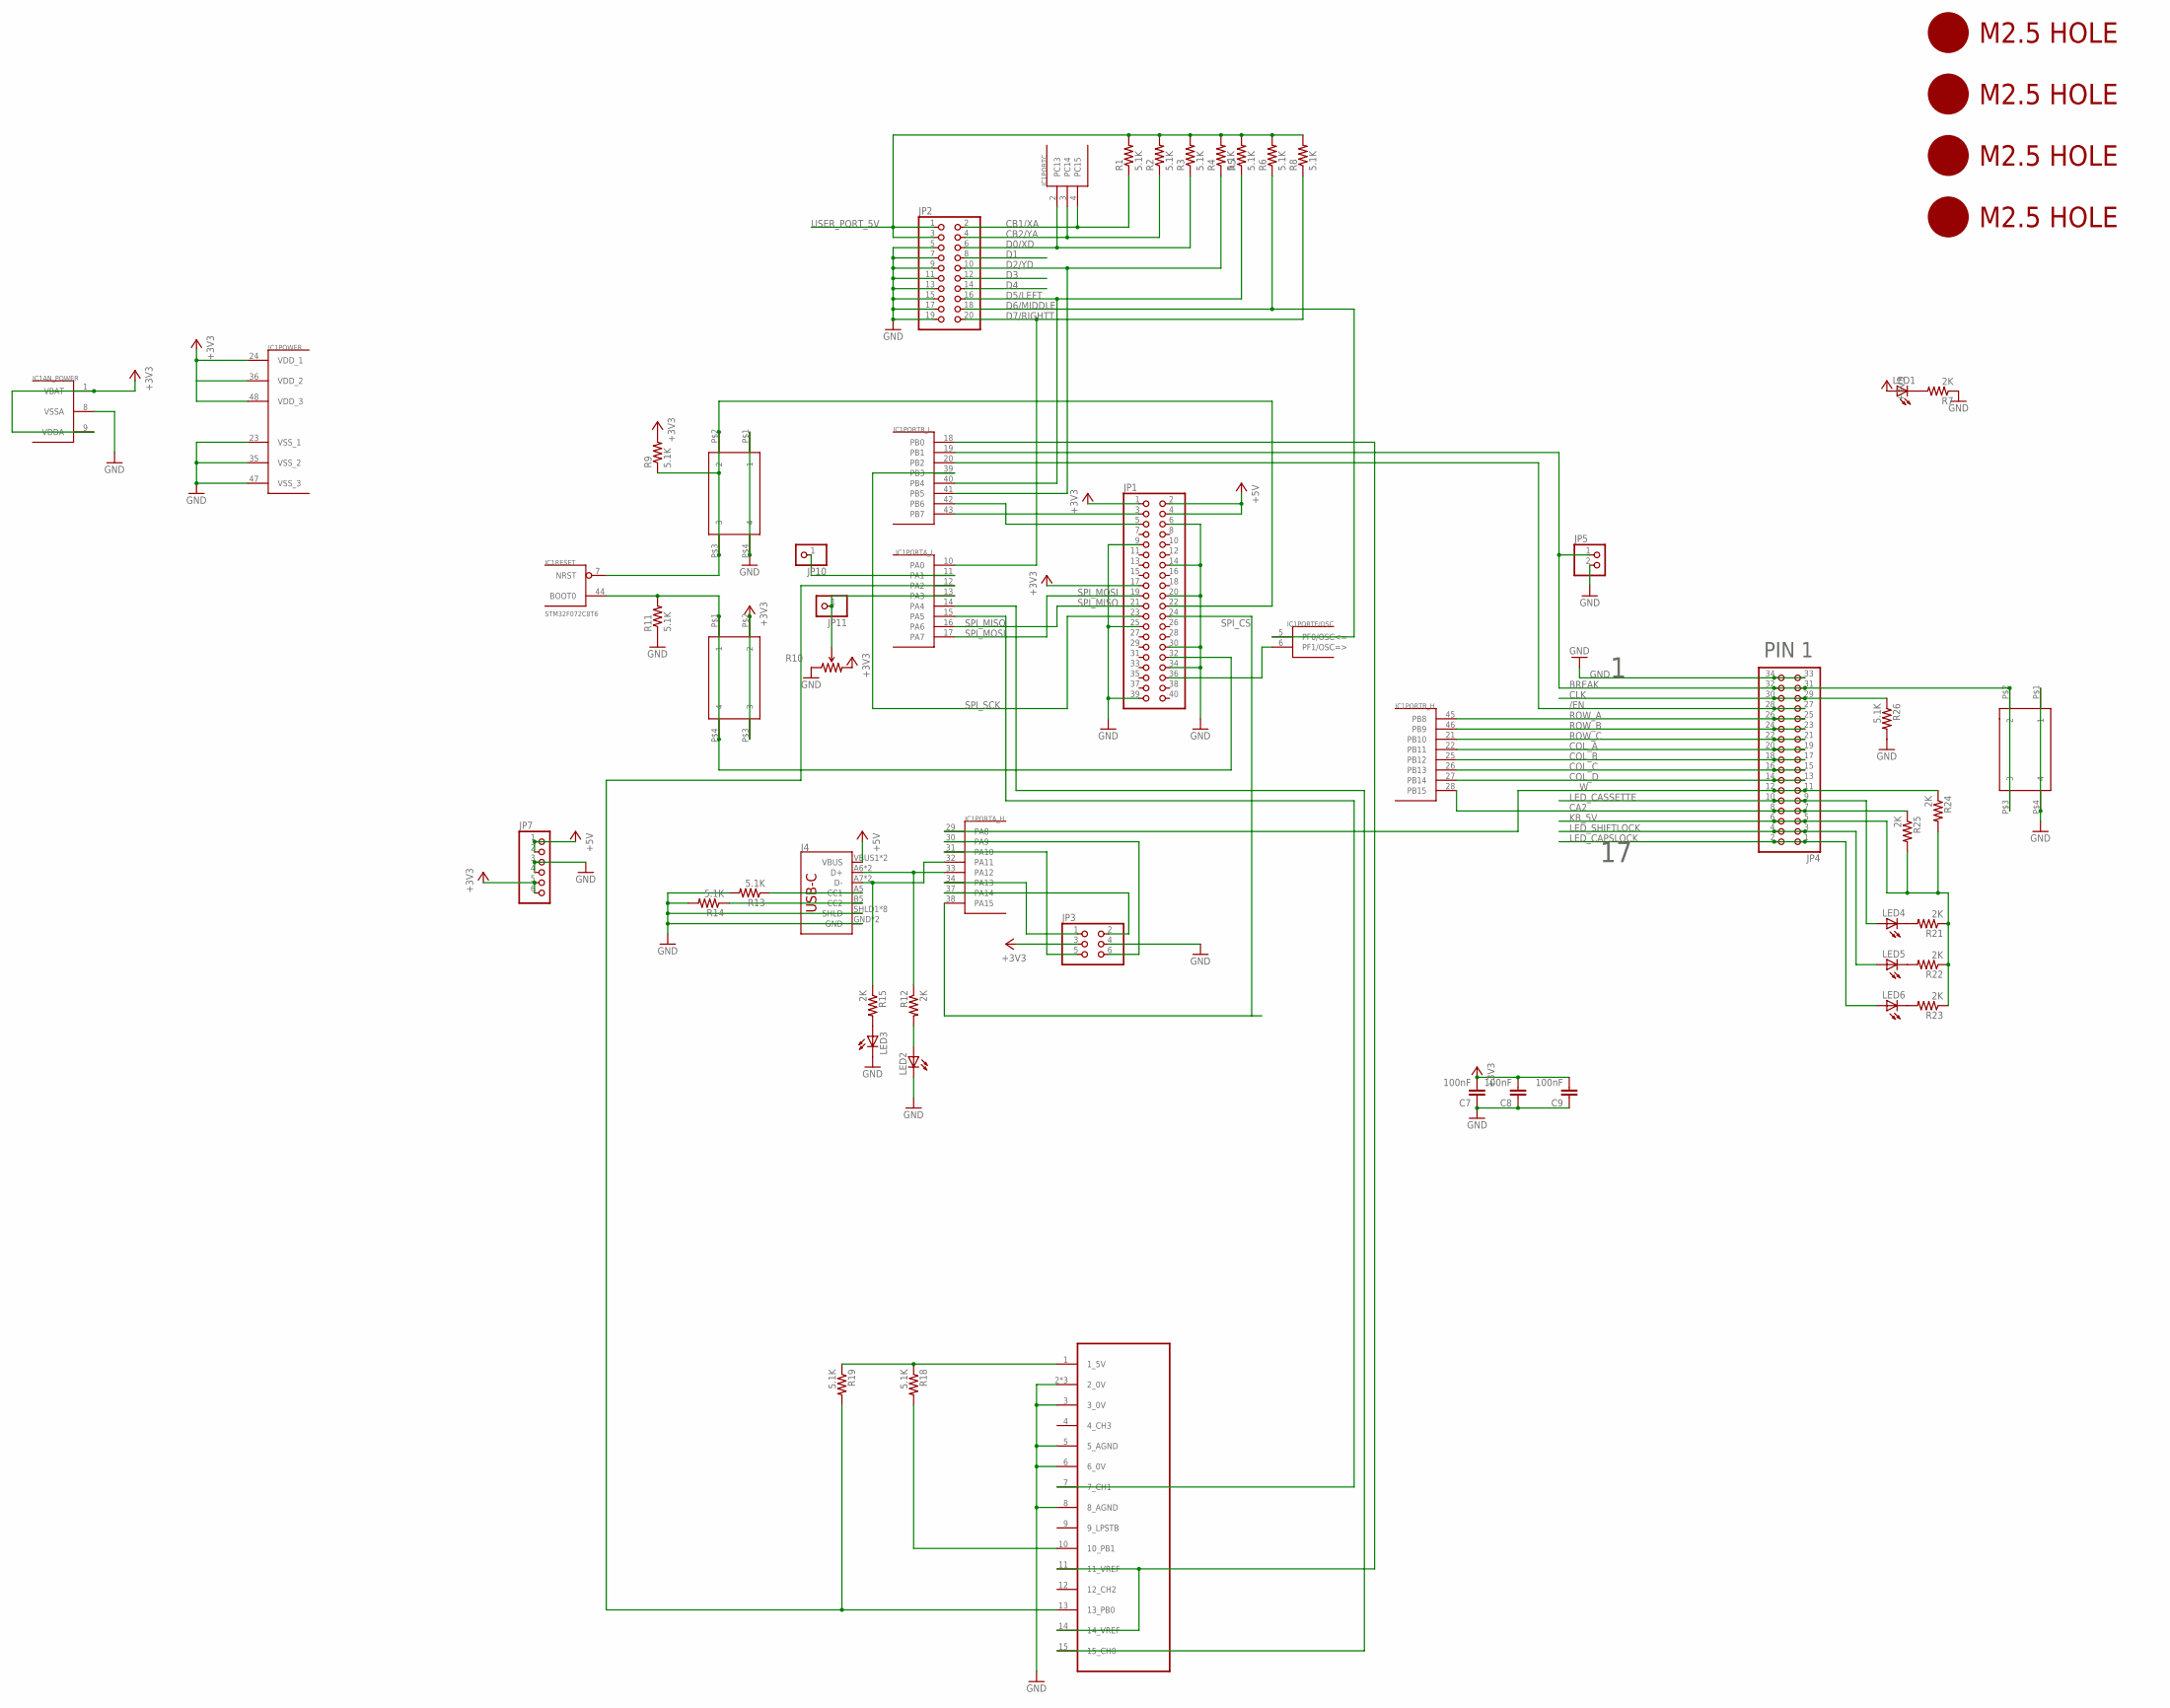
[picture p136: schematic bbc_micro.sch]

Parts:
C7, C8, C9: 100nF; 0805@1
IC1: STM32F072C8T6; TQFP48
J4: USB_C16PIN; USB-C-16P
JP1: PINHD-2X20-BIG; 2X20-BIG
JP2: PINHD-2X10/90; 2X10/90
JP3: PINHD-2X3; 2X03
JP4: PINHD-2X17/90; 2X17/90
JP5: PINHD-1X2; 1X02
JP7: PINHD-1X6CB; 1X06-CLEANBIG
JP10, JP11: PINHD-1X1CB; 1X01-CLEANBIG
LED1, LED2, LED3, LED4, LED5, LED6: LEDCHIP-LED0805; CHIP-LED0805
R1, R2, R3, R4, R5, R6, R8, R9, R11, R13, R14, R18, R19, R26: 5.1K; 0805
R7, R12, R15, R21, R22, R23, R24, R25: 2K; 0805
R10: TRIMPOTPTH; TRIM_POT_PTH
SW1, SW2, SW3: 324_SW; 342_SWICH_FOOT
U$2, U$3, U$6, U$7: M2.5HOLE
U$9: BBC_15P; DA15

Connections:
+3V3: C7.2, C8.2, C9.2, IC1.1 (VBAT), IC1.9 (VDDA), IC1.24 (VDD_1), IC1.36 (VDD_2), IC1.48 (VDD_3), JP1.1, JP1.17, JP3.3, JP7.5, JP7.6, LED1.A, R9.2, R10.3 (CW), SW2.P$2 (2), SW2.P$3 (3)
+5V: J4.VBUS1 (VBUS), J4.VBUS2 (VBUS), JP1.2, JP1.4, JP7.1, JP7.2
/EN: IC1.20 (PB2), JP4.27, JP4.28
BREAK: IC1.19 (PB1), JP4.31, JP4.32, JP5.1, SW3.P$2 (2), SW3.P$3 (3)
CA2: IC1.28 (PB15), JP4.7, JP4.8, R25.1
CB1/XA: IC1.4 (PC15), JP2.2, R1.1
CB2/YA: IC1.3 (PC14), JP2.4, R2.1
CLK: JP4.29, JP4.30, R26.1
COL_A: IC1.22 (PB11), JP4.19, JP4.20
COL_B: IC1.25 (PB12), JP4.17, JP4.18
COL_C: IC1.26 (PB13), JP4.15, JP4.16
COL_D: IC1.27 (PB14), JP4.13, JP4.14
D0/XD: IC1.2 (PC13), JP2.6, R3.1
D1: JP2.8
D2/YD: IC1.41 (PB5), JP2.10, R4.1
D3: JP2.12
D4: JP2.14
D5/LEFT: IC1.40 (PB4), JP2.16, R5.1
D6/MIDDLE: IC1.5 (PF0/OSC<=), JP2.18, R6.1
D7/RIGHTT: IC1.10 (PA0), JP2.20, R8.1
GND: C7.1, C8.1, C9.1, IC1.8 (VSSA), IC1.23 (VSS_1), IC1.35 (VSS_2), IC1.47 (VSS_3), J4.GND, J4.GND2 (GND), J4.SHLD1 (SHLD), J4.SHLD2 (SHLD), J4.SHLD3 (SHLD), J4.SHLD4 (SHLD), J4.SHLD5 (SHLD), J4.SHLD6 (SHLD), J4.SHLD7 (SHLD), J4.SHLD8 (SHLD), JP1.6, JP1.9, JP1.14, JP1.20, JP1.25, JP1.30, JP1.34, JP1.39, JP2.5, JP2.7, JP2.9, JP2.11, JP2.13, JP2.15, JP2.17, JP2.19, JP3.4, JP4.33, JP4.34, JP5.2, JP7.3, JP7.4, LED2.C, LED3.C, R7.1, R10.1 (CCW), R11.1, R13.2, R14.2, R26.2, SW1.P$1 (1), SW1.P$4 (4), SW3.P$1 (1), SW3.P$4 (4), U$9.2 (2_0V), U$9.3 (3_0V), U$9.5 (5_AGND), U$9.6 (6_0V), U$9.8 (8_AGND), U$9.G1 (2_0V), U$9.G2 (2_0V)
KB_5V: JP4.5, JP4.6, R21.1, R22.1, R23.1, R24.2, R25.2
LED_CAPSLOCK: JP4.1, JP4.2, LED6.A
LED_CASSETTE: JP4.9, JP4.10, LED4.A
LED_SHIFTLOCK: JP4.3, JP4.4, LED5.A
unnamed: J4.A5 (CC1), R13.1
unnamed: LED2.A, R12.2
unnamed: LED4.C, R21.2
unnamed: IC1.14 (PA4), U$9.15 (15_CH0)
unnamed: IC1.15 (PA5), U$9.7 (7_CH1)
unnamed: IC1.31 (PA10), JP3.5
unnamed: J4.B5 (CC2), R14.1
unnamed: IC1.33 (PA12), J4.A6 (D+), J4.B6 (D+), R12.1
unnamed: IC1.32 (PA11), J4.A7 (D-), J4.B7 (D-), R15.1
unnamed: IC1.18 (PB0), U$9.11 (11_VREF), U$9.14 (14_VREF)
unnamed: IC1.11 (PA1), JP10.1
unnamed: IC1.13 (PA3), JP11.1, R10.2 (WIPER)
unnamed: IC1.7 (NRST), JP1.22, R9.1, SW1.P$2 (2), SW1.P$3 (3)
unnamed: IC1.30 (PA9), JP3.6
unnamed: IC1.34 (PA13), JP3.1
unnamed: IC1.37 (PA14), JP3.2
unnamed: IC1.44 (BOOT0), JP1.32, R11.2, SW2.P$1 (1), SW2.P$4 (4)
unnamed: R18.1, R19.1, U$9.1 (1_5V)
unnamed: R18.2, U$9.10 (10_PB1)
unnamed: IC1.42 (PB6), JP1.5
unnamed: IC1.43 (PB7), JP1.3
unnamed: LED5.C, R22.2
unnamed: LED6.C, R23.2
unnamed: LED3.A, R15.2
unnamed: LED1.C, R7.2
unnamed: IC1.12 (PA2), R19.2, U$9.13 (13_PB0)
unnamed: IC1.6 (PF1/OSC=>), JP1.36
ROW_A: IC1.45 (PB8), JP4.25, JP4.26
ROW_B: IC1.46 (PB9), JP4.23, JP4.24
ROW_C: IC1.21 (PB10), JP4.21, JP4.22
SPI_CS: IC1.38 (PA15), JP1.24
SPI_MISO: IC1.16 (PA6), JP1.21
SPI_MOSI: IC1.17 (PA7), JP1.19
SPI_SCK: IC1.39 (PB3), JP1.23
USER_PORT_5V: JP2.1, JP2.3, R1.2, R2.2, R3.2, R4.2, R5.2, R6.2, R8.2
W: IC1.29 (PA8), JP4.11, JP4.12, R24.1

Notes on the sheet:
PIN 1

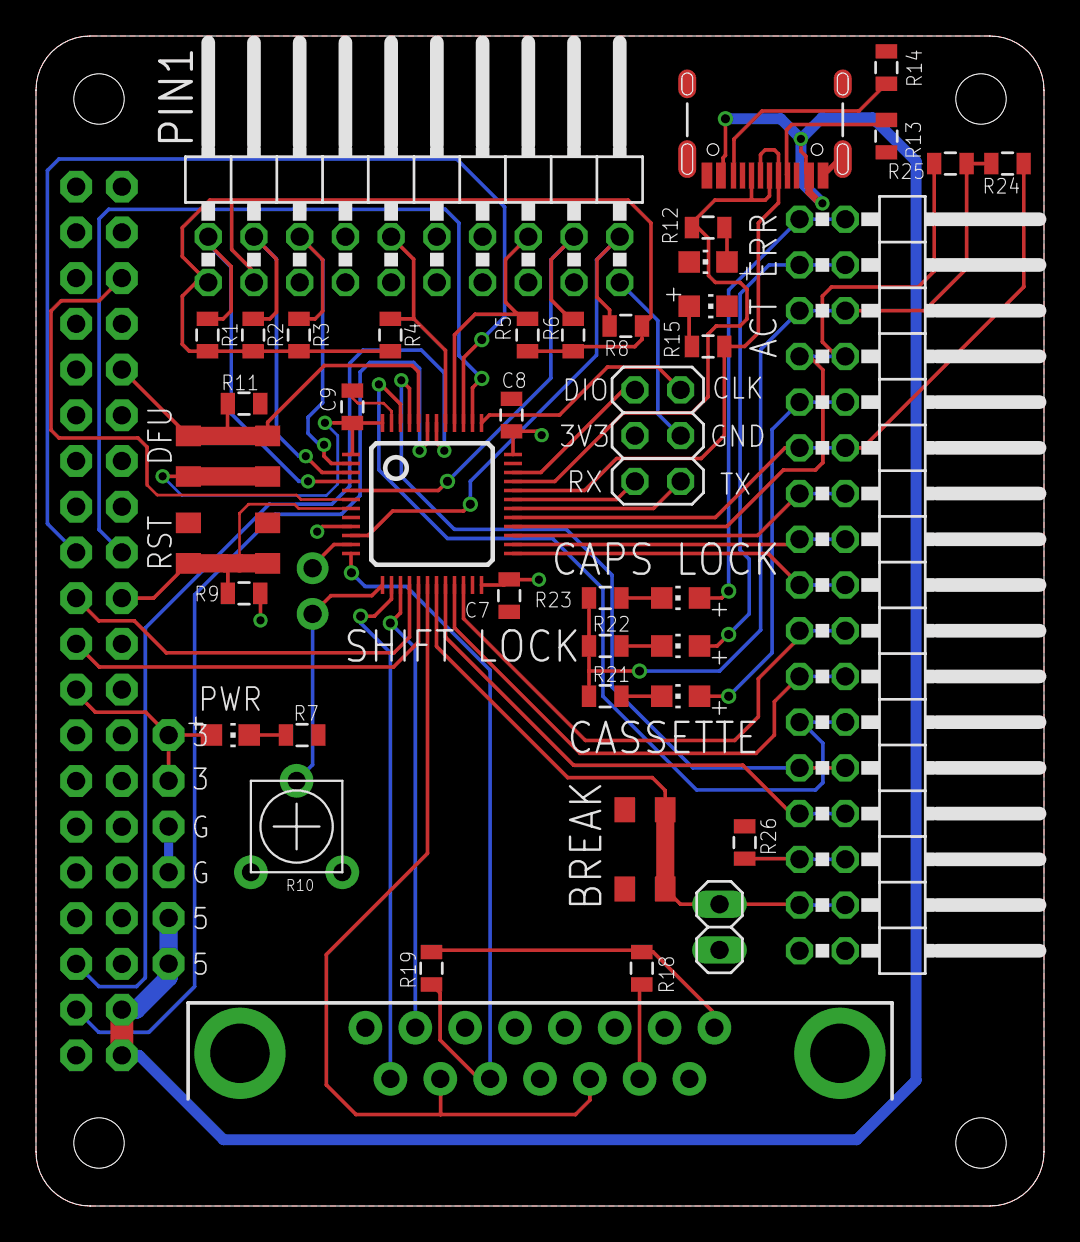
[picture p137: board bbc_micro.brd from above]

Board: 2 copper layers, 56.0 x 65.0 mm, 50 parts (1 on the bottom side), 58 nets.
