dekuNukem/USB4VC/resources/sparkfun trs breakout/TRS_Jack_Breakout.brd

## EAGLE design resources/sparkfun trs breakout/TRS_Jack_Breakout.brd (2022-06-30)

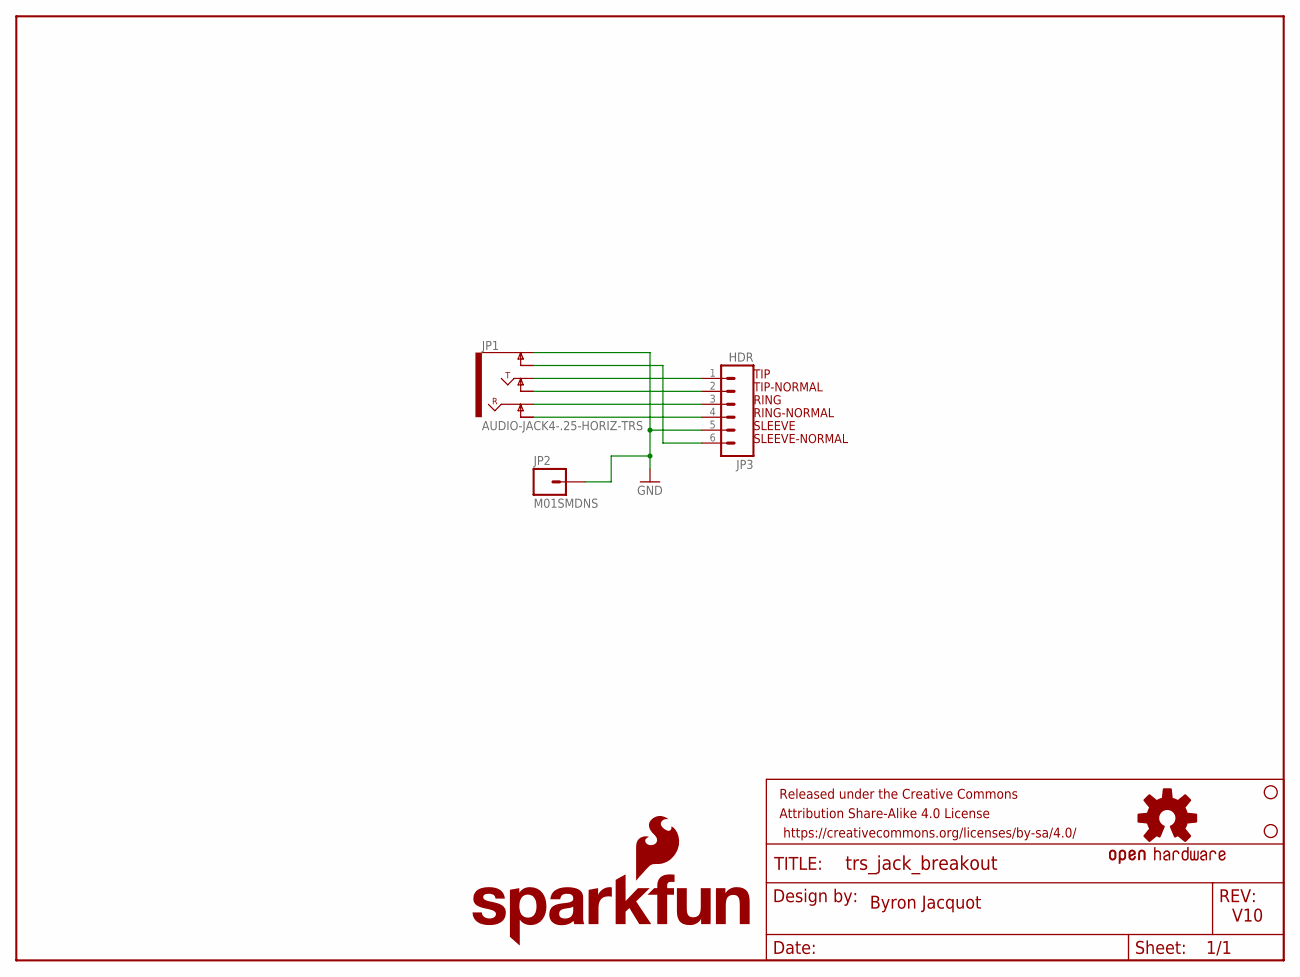
[picture p138: schematic TRS_Jack_Breakout.sch]

Parts:
FRAME1: FRAME-LETTER; CREATIVE_COMMONS
JP1: AUDIO-JACK4-.25-HORIZ-TRS; AUDIO-JACK-.25-INCH-HORIZ-PTH
JP2: M01SMDNS; 1X01NS
JP3: HDR; 1X06_NO_SILK
LOGO1: SFE_LOGO_NAME_FLAME.1_INCH; SFE_LOGO_NAME_FLAME_.1
LOGO2: OSHW-LOGOS; OSHW-LOGO-S
STANDOFF1, STANDOFF2: STAND-OFF

Connections:
GND: JP1.SLEEVE (EARTH), JP2.1, JP3.5
unnamed: JP1.TIP, JP3.1
unnamed: JP1.TIP-NORM, JP3.2
unnamed: JP1.RING, JP3.3
unnamed: JP1.RING-NORM, JP3.4
unnamed: JP1.SLEEVE-NORM (EARTH-NORM), JP3.6

Notes on the sheet:
Byron Jacquot
V10
TIP
TIP-NORMAL
RING
RING-NORMAL
SLEEVE
SLEEVE-NORMAL
