dekuNukem/USB4VC/resources/sparkfun trs breakout/TRS_Jack_Breakout.brd

## EAGLE design resources/sparkfun trs breakout/TRS_Jack_Breakout.brd (continued)

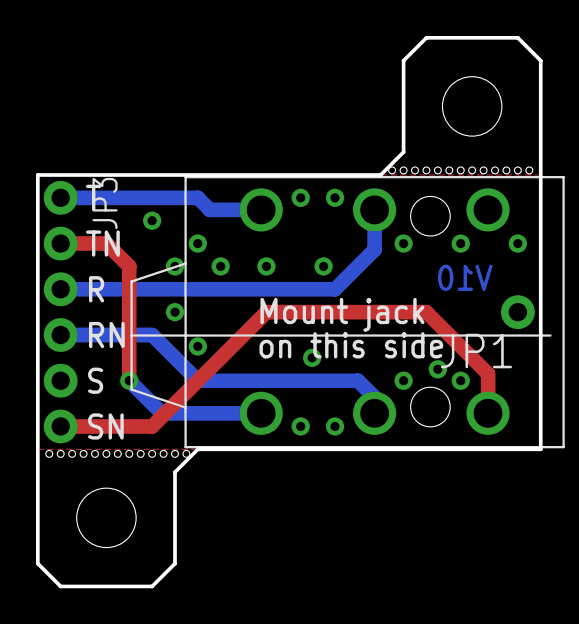
[picture p139: board TRS_Jack_Breakout.brd from above]

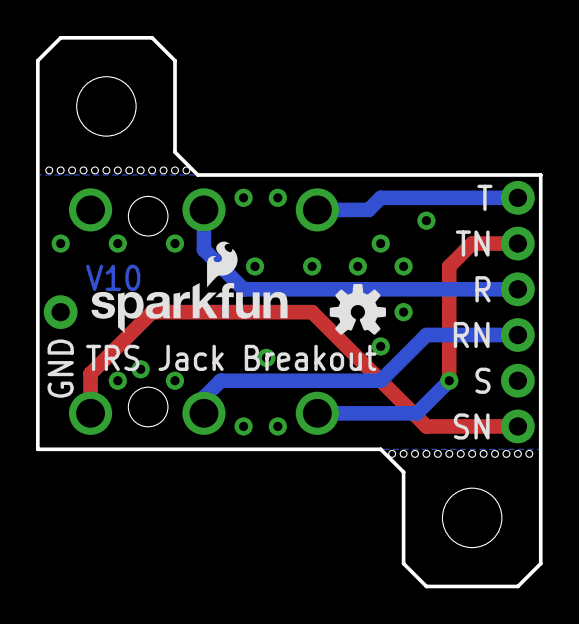
[picture p140: board TRS_Jack_Breakout.brd from below]

Board: 2 copper layers, 27.9 x 30.5 mm, 8 parts (2 on the bottom side), 6 nets.
