dekuNukem/USB4VC/pcb/base_board/pt1/baseboard.brd

## EAGLE design pcb/base_board/pt1/baseboard.brd (2021-12-01, an earlier design)

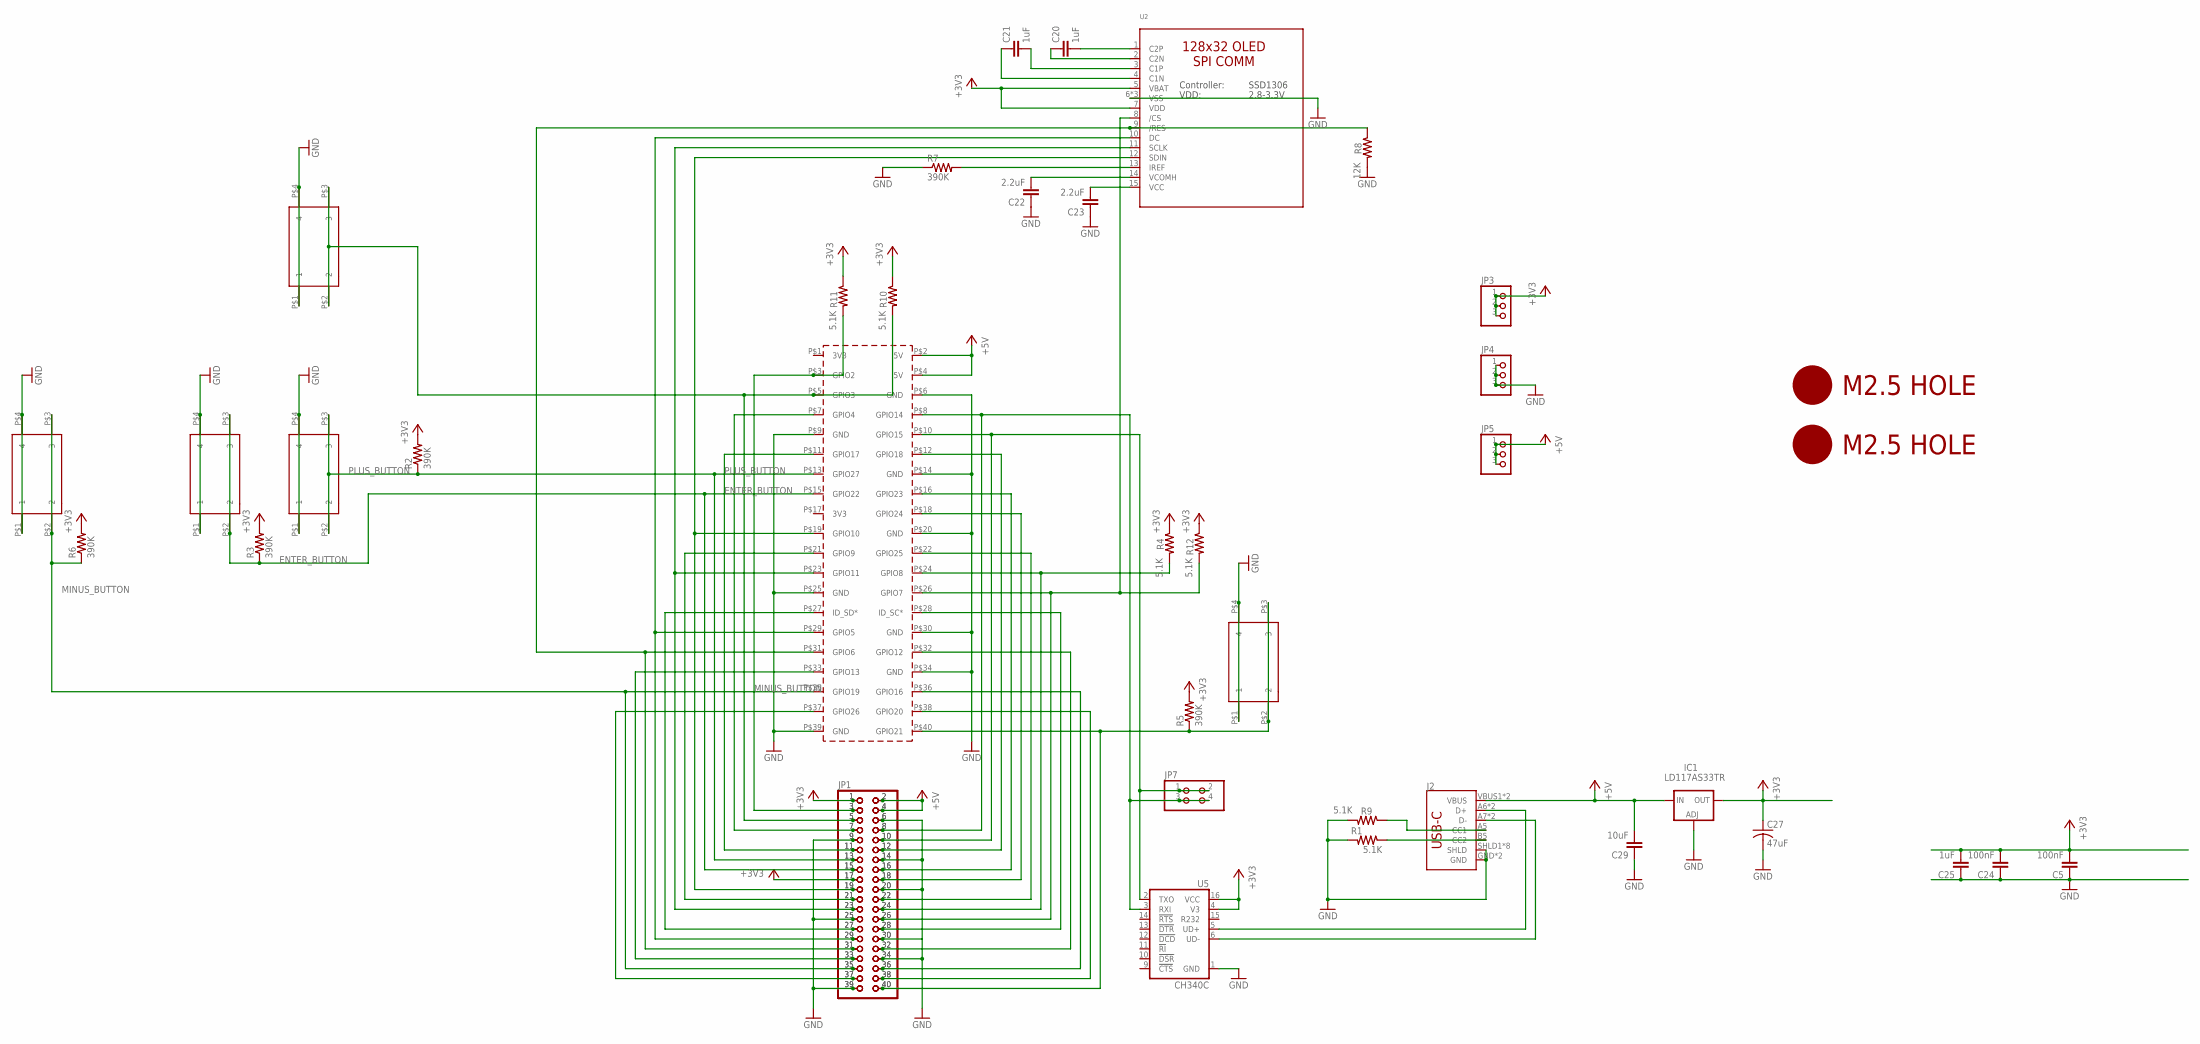
[picture p141: schematic baseboard.sch]

Parts:
C5, C24: 100nF; 0805
C20, C21, C25: 1uF; 0805
C22, C23: 2.2uF; 0805
C27: 47uF; C1210
C29: 10uF; 0805
IC1: LD117AS33TR; SOT223
J2: USB_C16PIN; USB-C-16P
JP1, JP2: PINHD-2X20-BIG; 2X20-BIG
JP3, JP4, JP5: PINHD-1X3; 1X03
JP7: PINHD-2X2; 2X02
PCB1: RPI3NO-CONNECTORS; RPI3-NO-CONNECTORS
R1, R4, R9, R10, R11, R12: 5.1K; 0805
R2, R3, R5, R6, R7: 390K; 0805
R8: 12K; 0805
SW1, SW2, SW3, SW4, SW20: 324_SW; 342_SWICH_FOOT
U2: LUL_DISP_OLED_UG-2864HSWEG01; LUL_UG-2864HSWEG01_1.3_WRAPAROUND
U5: CH340C; SO016
U$2, U$3: M2.5HOLE

Connections:
+3V3: C5.2, C24.2, C25.2, C27.1, IC1.4 (OUT), JP1.1, JP1.17, JP2.1, JP2.17, JP3.1, JP3.2, JP3.3, R2.2, R3.2, R4.1, R5.2, R6.2, R10.1, R11.1, R12.1, U2.5 (VBAT), U2.7 (VDD), U5.4 (V3), U5.16 (VCC)
+5V: C29.2, IC1.3 (IN), J2.VBUS1 (VBUS), J2.VBUS2 (VBUS), JP1.2, JP1.4, JP2.2, JP2.4, JP5.1, JP5.2, JP5.3, PCB1.P$2 (5V), PCB1.P$4 (5V)
ENTER_BUTTON: JP1.15, JP2.15, PCB1.P$15 (GPIO22), R3.1, SW20.P$2 (2), SW20.P$3 (3)
GND: C5.1, C22.1, C23.1, C24.1, C25.1, C27.2, C29.1, IC1.1 (ADJ), J2.GND, J2.GND2 (GND), J2.SHLD1 (SHLD), J2.SHLD2 (SHLD), J2.SHLD3 (SHLD), J2.SHLD4 (SHLD), J2.SHLD5 (SHLD), J2.SHLD6 (SHLD), J2.SHLD7 (SHLD), J2.SHLD8 (SHLD), JP1.6, JP1.9, JP1.14, JP1.20, JP1.25, JP1.30, JP1.34, JP1.39, JP2.6, JP2.9, JP2.14, JP2.20, JP2.25, JP2.30, JP2.34, JP2.39, JP4.1, JP4.2, JP4.3, PCB1.P$6 (GND), PCB1.P$9 (GND), PCB1.P$14 (GND), PCB1.P$20 (GND), PCB1.P$25 (GND), PCB1.P$30 (GND), PCB1.P$34 (GND), PCB1.P$39 (GND), R1.2, R7.1, R8.2, R9.2, SW1.P$1 (1), SW1.P$4 (4), SW2.P$1 (1), SW2.P$4 (4), SW3.P$1 (1), SW3.P$4 (4), SW4.P$1 (1), SW4.P$4 (4), SW20.P$1 (1), SW20.P$4 (4), U2.6 (VSS), U2.16 (VSS), U2.17 (VSS), U5.1 (GND)
MINUS_BUTTON: JP1.35, JP2.35, PCB1.P$35 (GPIO19), R6.1, SW4.P$2 (2), SW4.P$3 (3)
unnamed: J2.A6 (D+), J2.B6 (D+), U5.5 (UD+)
unnamed: J2.A5 (CC1), R9.1
unnamed: J2.A7 (D-), J2.B7 (D-), U5.6 (UD-)
unnamed: JP1.3, JP2.3, PCB1.P$3 (GPIO2), R11.2
unnamed: JP1.5, JP2.5, PCB1.P$5 (GPIO3), R10.2, SW2.P$2 (2), SW2.P$3 (3)
unnamed: J2.B5 (CC2), R1.1
unnamed: JP1.7, JP2.7, PCB1.P$7 (GPIO4)
unnamed: JP1.11, JP2.11, PCB1.P$11 (GPIO17)
unnamed: JP1.19, JP2.19, PCB1.P$19 (GPIO10), U2.12 (SDIN)
unnamed: JP1.21, JP2.21, PCB1.P$21 (GPIO9)
unnamed: JP1.23, JP2.23, PCB1.P$23 (GPIO11), U2.11 (SCLK)
unnamed: JP1.27, JP2.27, PCB1.P$27 (ID_SD*)
unnamed: JP1.29, JP2.29, PCB1.P$29 (GPIO5), U2.10 (DC)
unnamed: JP1.33, JP2.33, PCB1.P$33 (GPIO13)
unnamed: JP1.37, JP2.37, PCB1.P$37 (GPIO26)
unnamed: JP1.12, JP2.12, PCB1.P$12 (GPIO18)
unnamed: JP1.16, JP2.16, PCB1.P$16 (GPIO23)
unnamed: JP1.18, JP2.18, PCB1.P$18 (GPIO24)
unnamed: JP1.22, JP2.22, PCB1.P$22 (GPIO25)
unnamed: JP1.24, JP2.24, PCB1.P$24 (GPIO8), R4.2
unnamed: JP1.26, JP2.26, PCB1.P$26 (GPIO7), R12.2, U2.8 (/CS)
unnamed: JP1.28, JP2.28, PCB1.P$28 (ID_SC*)
unnamed: JP1.32, JP2.32, PCB1.P$32 (GPIO12)
unnamed: JP1.36, JP2.36, PCB1.P$36 (GPIO16)
unnamed: JP1.38, JP2.38, PCB1.P$38 (GPIO20)
unnamed: JP1.40, JP2.40, PCB1.P$40 (GPIO21), R5.1, SW3.P$2 (2), SW3.P$3 (3)
unnamed: C20.2, U2.1 (C2P)
unnamed: C20.1, U2.2 (C2N)
unnamed: C21.2, U2.3 (C1P)
unnamed: C21.1, U2.4 (C1N)
unnamed: R7.2, U2.13 (IREF)
unnamed: C22.2, U2.14 (VCOMH)
unnamed: C23.2, U2.15 (VCC)
unnamed: JP1.31, JP2.31, PCB1.P$31 (GPIO6), R8.1, U2.9 (/RES)
PLUS_BUTTON: JP1.13, JP2.13, PCB1.P$13 (GPIO27), R2.1, SW1.P$2 (2), SW1.P$3 (3)
RPI_RX: JP1.10, JP2.10, JP7.1, JP7.2, PCB1.P$10 (GPIO15), U5.2 (TXO)
RPI_TX: JP1.8, JP2.8, JP7.3, JP7.4, PCB1.P$8 (GPIO14), U5.3 (RXI)

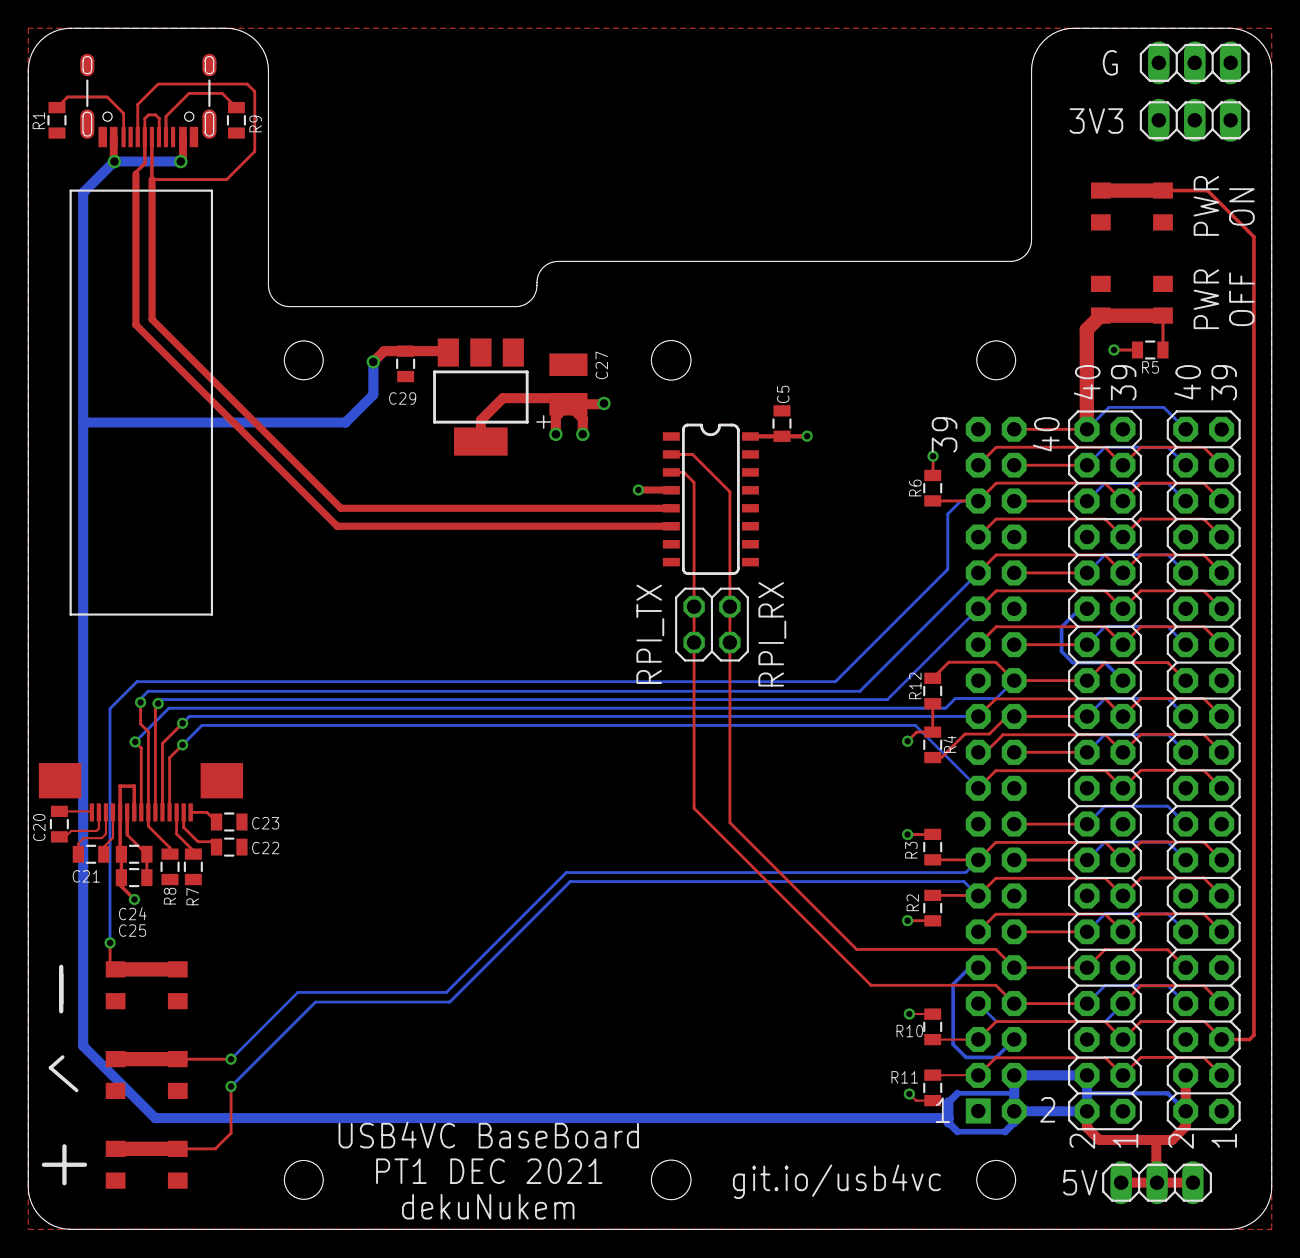
[picture p142: board pcb/base_board/pt1/baseboard.brd from above]

Board: 2 copper layers, 88.0 x 85.0 mm, 39 parts (0 on the bottom side), 42 nets.
