dekuNukem/USB4VC/pcb/dsub stacker/stacker.brd

## EAGLE design pcb/dsub stacker/stacker.brd (2021-12-02)

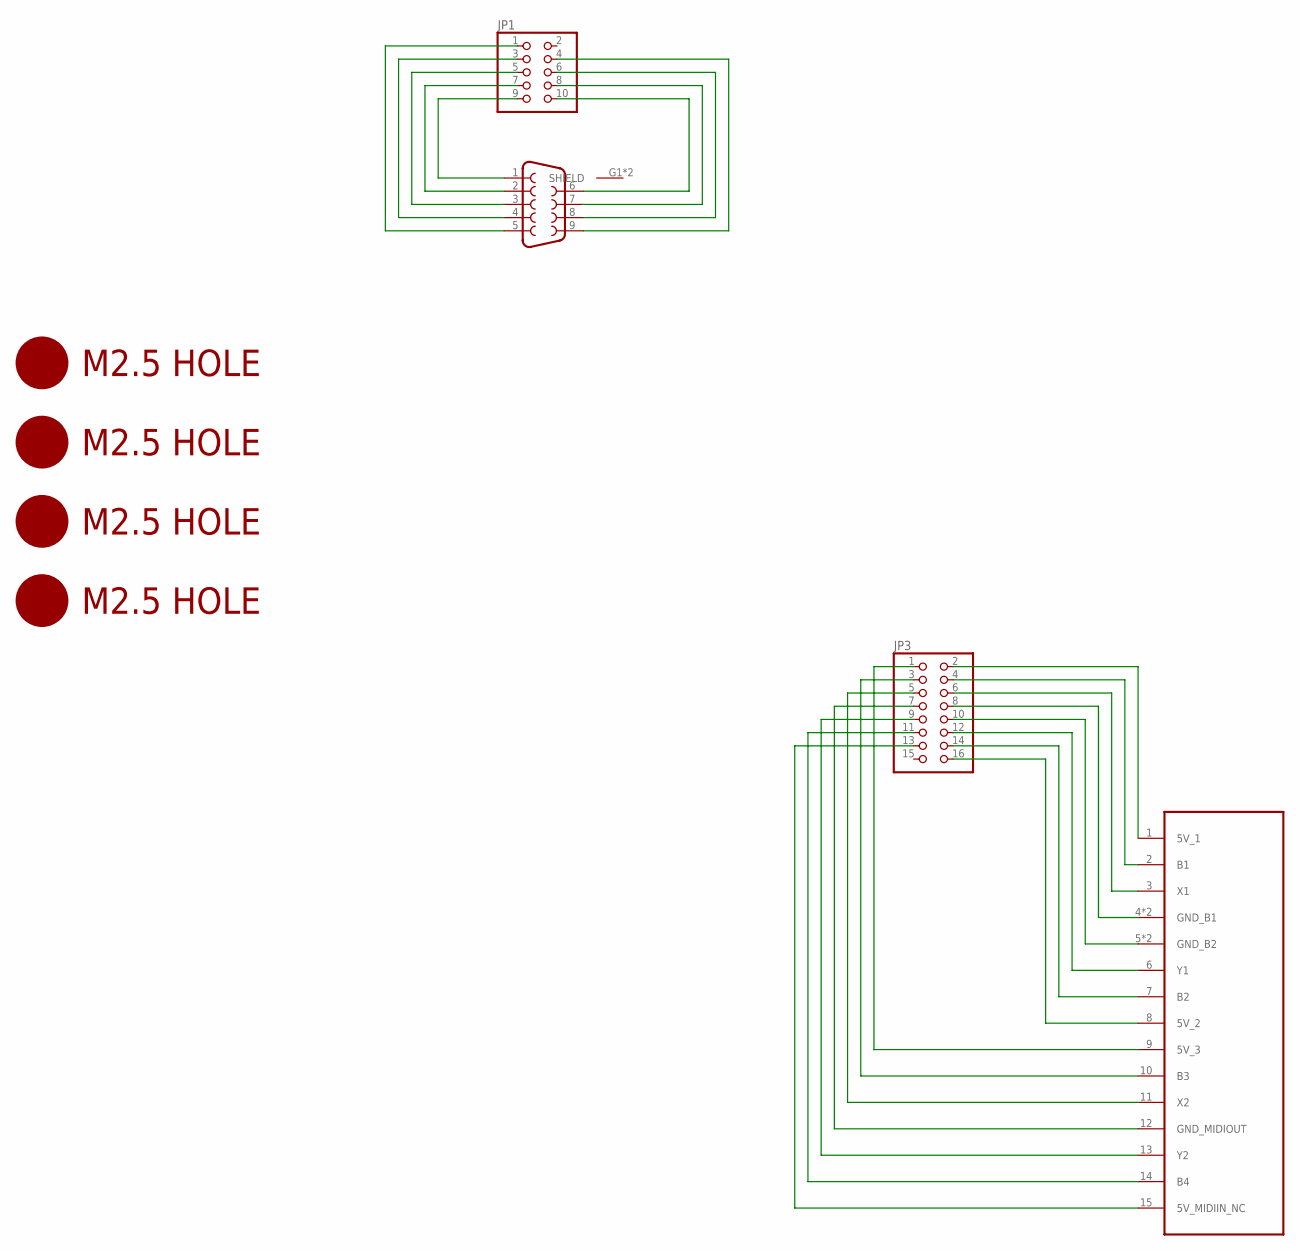
[picture p143: schematic stacker.sch]

Parts:
J5: DB9MALE; DB9_MALE
JP1: PINHD-2X5; 2X05
JP3: PINHD-2X8; 2X08
U$2, U$3, U$4, U$5: M2.5HOLE
U$11: GAMEPORT_15P; DA15

Connections:
unnamed: J5.1, JP1.9
unnamed: J5.2, JP1.7
unnamed: J5.3, JP1.5
unnamed: J5.4, JP1.3
unnamed: J5.5, JP1.1
unnamed: J5.6, JP1.10
unnamed: J5.7, JP1.8
unnamed: J5.8, JP1.6
unnamed: J5.9, JP1.4
unnamed: JP3.2, U$11.1 (5V_1)
unnamed: JP3.4, U$11.2 (B1)
unnamed: JP3.6, U$11.3 (X1)
unnamed: JP3.8, U$11.4 (GND_B1), U$11.G1 (GND_B1)
unnamed: JP3.10, U$11.5 (GND_B2), U$11.G2 (GND_B2)
unnamed: JP3.12, U$11.6 (Y1)
unnamed: JP3.14, U$11.7 (B2)
unnamed: JP3.16, U$11.8 (5V_2)
unnamed: JP3.1, U$11.9 (5V_3)
unnamed: JP3.3, U$11.10 (B3)
unnamed: JP3.5, U$11.11 (X2)
unnamed: JP3.7, U$11.12 (GND_MIDIOUT)
unnamed: JP3.9, U$11.13 (Y2)
unnamed: JP3.11, U$11.14 (B4)
unnamed: JP3.13, U$11.15 (5V_MIDIIN_NC)

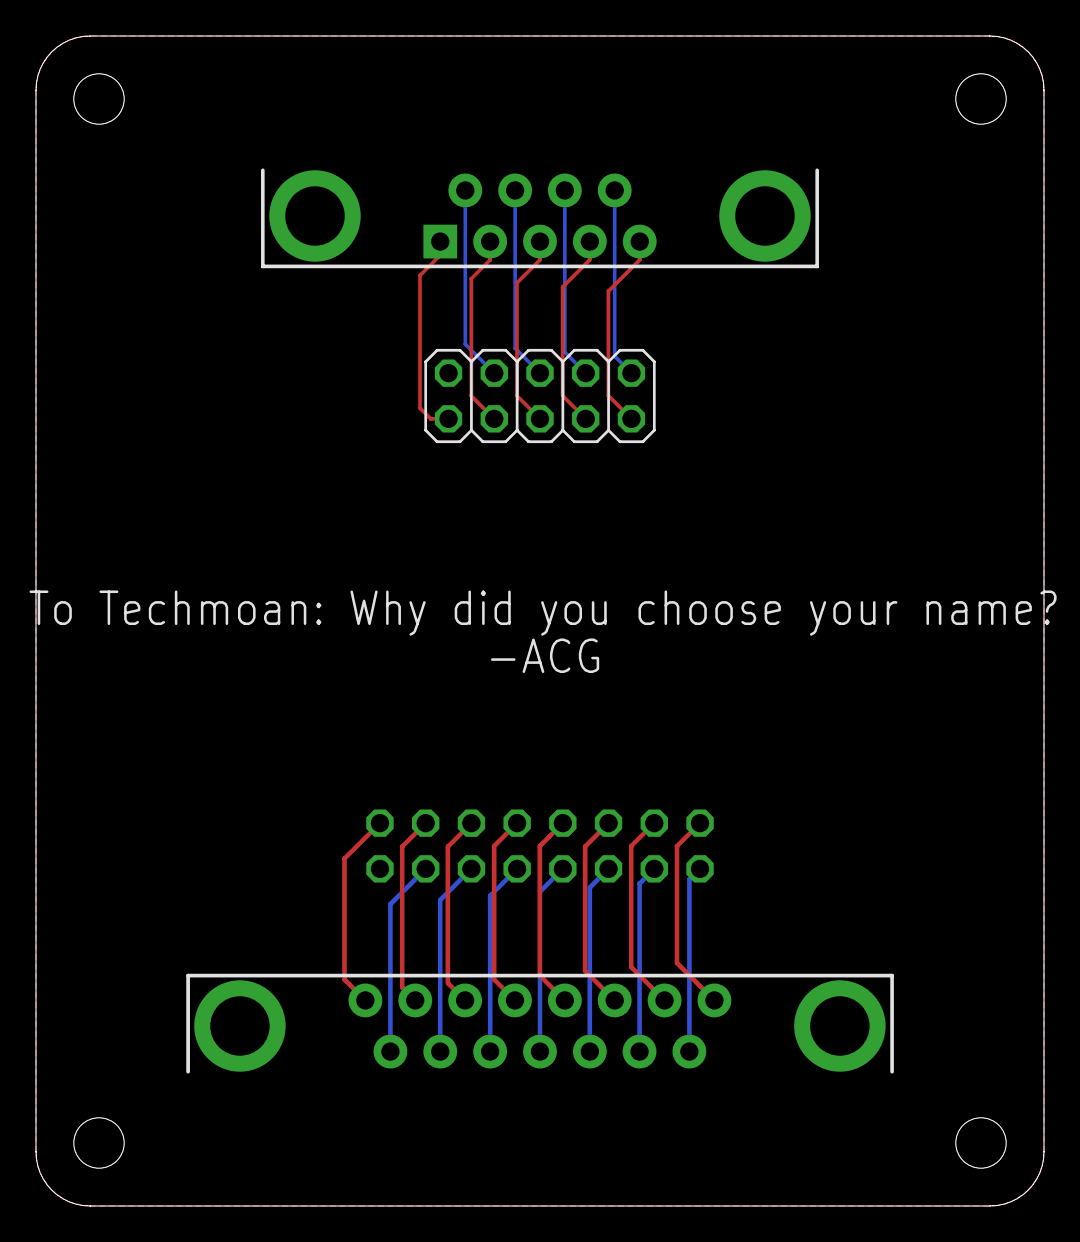
[picture p144: board stacker.brd from above]

Board: 2 copper layers, 56.0 x 65.0 mm, 8 parts (1 on the bottom side), 24 nets.
