dekuNukem/USB4VC/pcb/usb breakout/usb_breakout.brd

## EAGLE design pcb/usb breakout/usb_breakout.brd (2021-12-02)

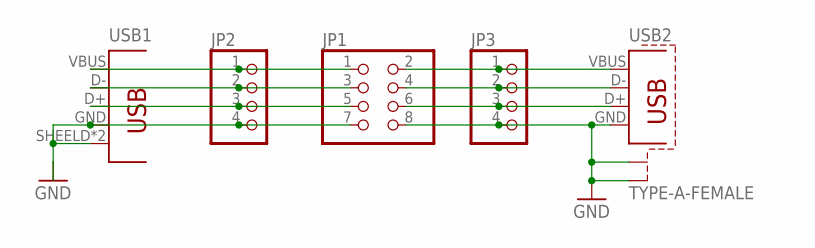
[picture p145: schematic usb_breakout.sch]

Parts:
JP1: PINHD-2X4; 2X04
JP2, JP3: PINHD-1X4; 1X04
USB1: TYPE-A-MALE-SHILED; TYPE-A-MALE
USB2: TYPE-A-FEMALE

Connections:
GND: JP1.7, JP1.8, JP2.4, JP3.4, USB1.GND (4), USB1.SHEELD (5), USB1.SHEELD2 (5), USB2.GND, USB2.S1, USB2.S2
unnamed: JP1.1, JP2.1, USB1.VBUS (1)
unnamed: JP1.3, JP2.2, USB1.D- (2)
unnamed: JP1.5, JP2.3, USB1.D+ (3)
unnamed: JP1.2, JP3.1, USB2.VBUS (VCC)
unnamed: JP1.4, JP3.2, USB2.D-
unnamed: JP1.6, JP3.3, USB2.D+

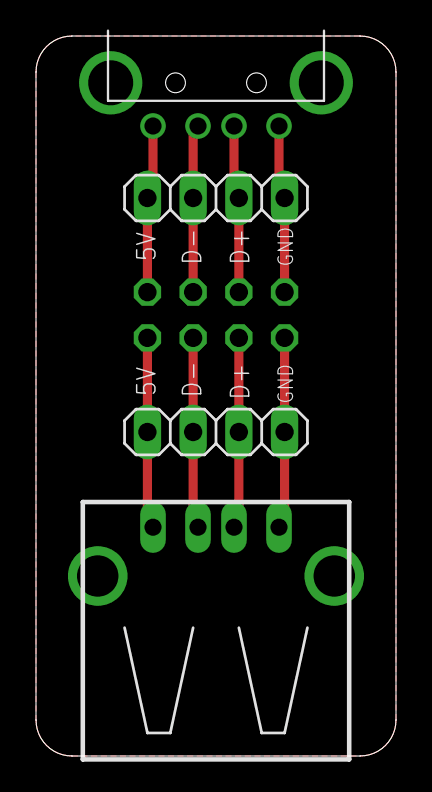
[picture p146: board usb_breakout.brd from above]

Board: 2 copper layers, 20.0 x 40.0 mm, 5 parts (1 on the bottom side), 7 nets.
