dekuNukem/USB4VC/pcb/ps2_board/wrong_header/ps2.brd

## EAGLE design pcb/ps2_board/wrong_header/ps2.brd (2021-11-27)

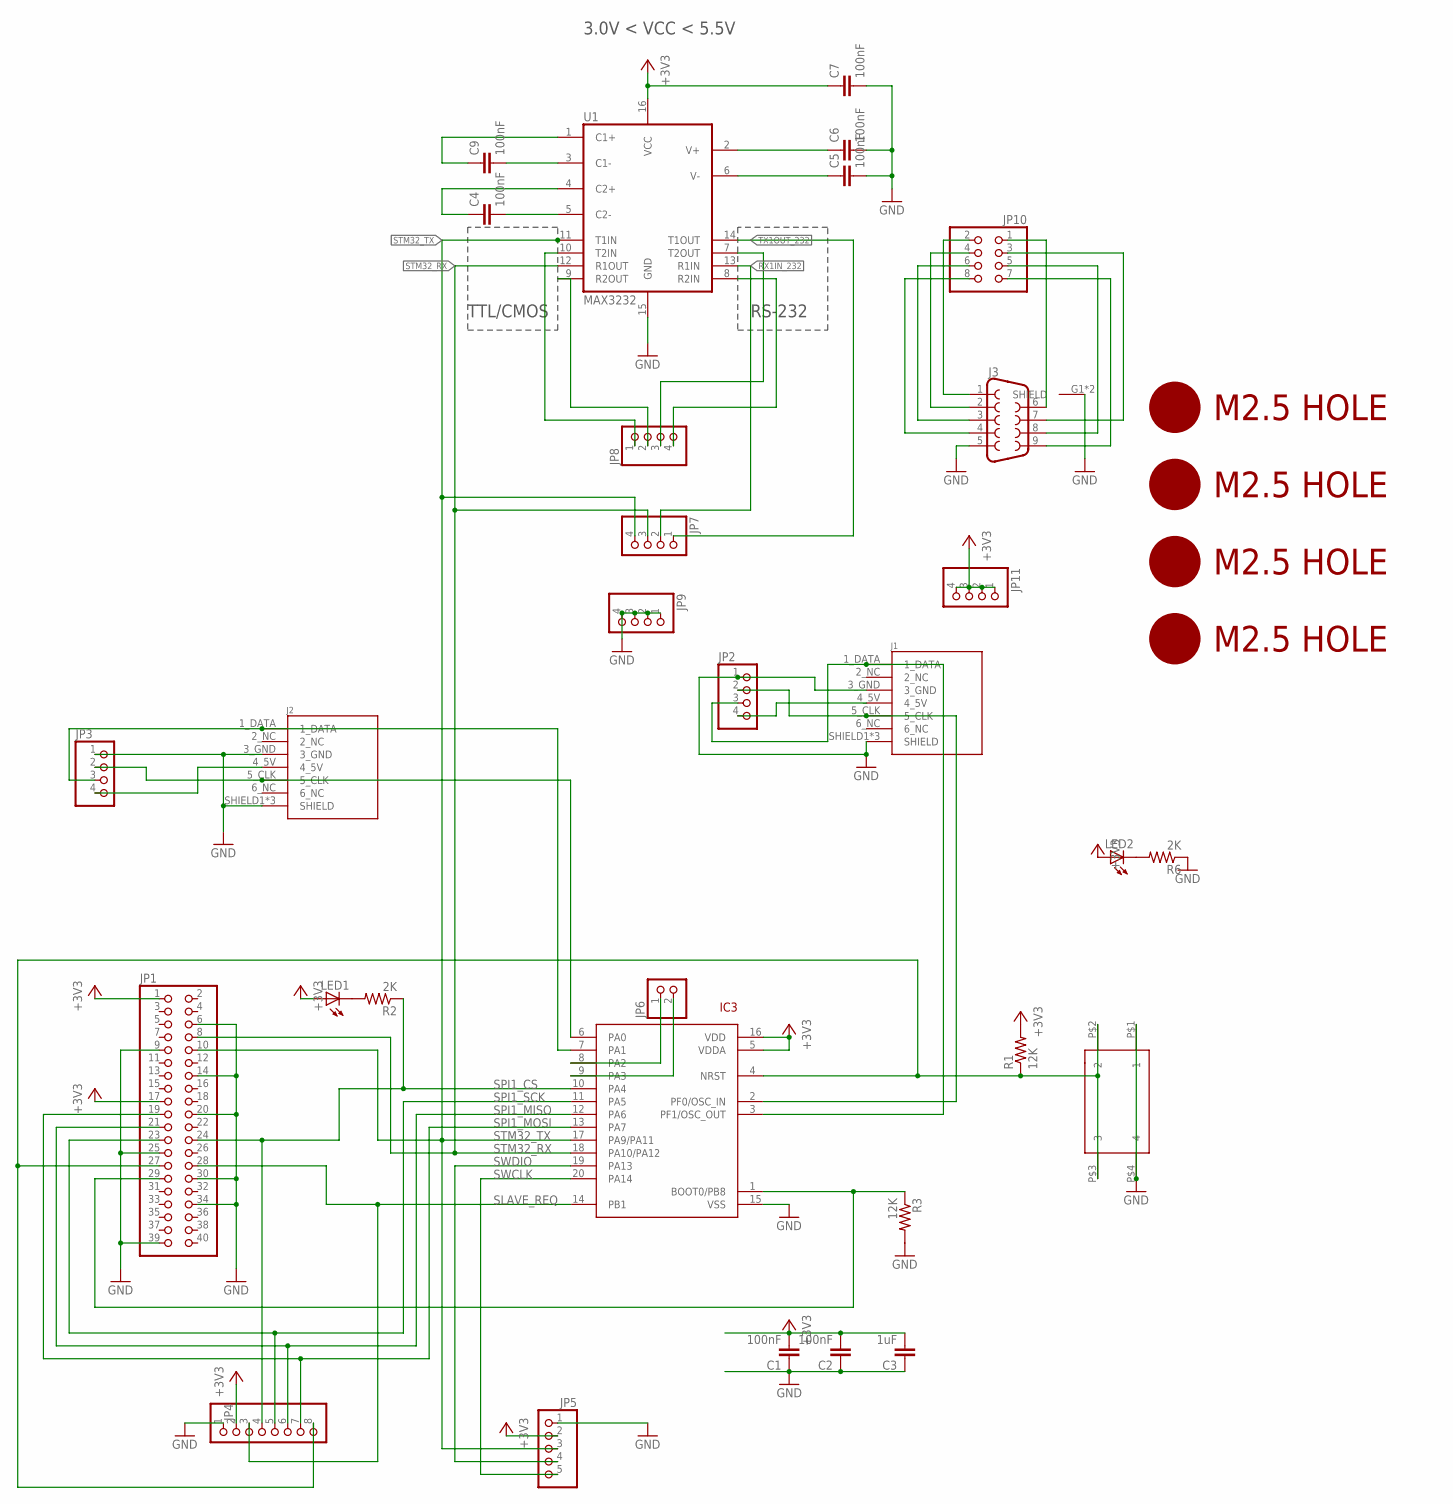
[picture p147: schematic ps2.sch]

Parts:
C1, C2, C4, C5, C6, C7, C9: 100nF; 0805@1
C3: 1uF; 0805@1
IC3: STM32F042F4; TSSOP20
J1, J2: DIN7
J3: DB9MALE; DB9_MALE
JP1: PINHD-2X20-BIG; 2X20-BIG
JP2, JP3, JP7, JP8, JP9, JP11: PINHD-1X4; 1X04
JP4: PINHD-1X8; 1X08
JP5: PINHD-1X5; 1X05
JP6: PINHD-1X2; 1X02
JP10: PINHD-2X4; 2X04
LED1, LED2: LEDCHIP-LED0805; CHIP-LED0805
R1, R3: 12K; 0805
R2, R6: 2K; 0805
SW4: 324_SW; 342_SWICH_FOOT
U1: MAX3232; SO016
U$2, U$3, U$4, U$5: M2.5HOLE

Connections:
+3V3: C1.2, C2.2, C3.2, C7.1, IC3.5 (VDDA), IC3.16 (VDD), JP1.1, JP1.17, JP4.2, JP5.2, JP11.1, JP11.2, JP11.3, JP11.4, LED1.A, LED2.A, R1.2, U1.16 (VCC)
C1+: C9.1, U1.1 (C1+)
C1-: C9.2, U1.3 (C1-)
C2+: C4.1, U1.4 (C2+)
C2-: C4.2, U1.5 (C2-)
GND: C1.1, C2.1, C3.1, C5.2, C6.2, C7.2, IC3.15 (VSS), J1.3_GND, J1.SHIELD1 (SHIELD), J1.SHIELD2 (SHIELD), J1.SHIELD3 (SHIELD), J2.3_GND, J2.SHIELD1 (SHIELD), J2.SHIELD2 (SHIELD), J2.SHIELD3 (SHIELD), J3.5, J3.G1 (SHIELD), J3.G2 (SHIELD), JP1.6, JP1.9, JP1.14, JP1.20, JP1.25, JP1.30, JP1.34, JP1.39, JP2.1, JP3.1, JP4.1, JP5.1, JP9.1, JP9.2, JP9.3, JP9.4, R3.2, R6.1, SW4.P$1 (1), SW4.P$4 (4), U1.15 (GND)
unnamed: IC3.4 (NRST), JP1.27, JP4.8, R1.1, SW4.P$2 (2), SW4.P$3 (3)
unnamed: LED1.C, R2.2
unnamed: J1.4_5V, JP2.4
unnamed: J2.4_5V, JP3.4
unnamed: IC3.2 (PF0/OSC_IN), J1.5_CLK, JP2.2
unnamed: IC3.3 (PF1/OSC_OUT), J1.1_DATA, JP2.3
unnamed: IC3.6 (PA0), J2.5_CLK, JP3.2
unnamed: IC3.7 (PA1), J2.1_DATA, JP3.3
unnamed: IC3.1 (BOOT0/PB8), JP1.29, R3.1
unnamed: IC3.8 (PA2), JP6.1
unnamed: IC3.9 (PA3), JP6.2
unnamed: JP8.1, U1.10 (T2IN)
unnamed: JP8.2, U1.9 (R2OUT)
unnamed: JP8.3, U1.7 (T2OUT)
unnamed: JP8.4, U1.8 (R2IN)
unnamed: J3.1, JP10.2
unnamed: J3.2, JP10.4
unnamed: J3.3, JP10.6
unnamed: J3.4, JP10.8
unnamed: J3.6, JP10.1
unnamed: J3.7, JP10.3
unnamed: J3.8, JP10.5
unnamed: J3.9, JP10.7
unnamed: LED2.C, R6.2
RX1IN_232: JP7.2, U1.13 (R1IN)
SLAVE_REQ: IC3.14 (PB1), JP1.28, JP4.3
SPI1_CS: IC3.10 (PA4), JP1.24, JP4.4, R2.1
SPI1_MISO: IC3.12 (PA6), JP1.21, JP4.6
SPI1_MOSI: IC3.13 (PA7), JP1.19, JP4.7
SPI1_SCK: IC3.11 (PA5), JP1.23, JP4.5
STM32_RX: IC3.18 (PA10/PA12), JP1.8, JP7.3, U1.12 (R1OUT)
STM32_TX: IC3.17 (PA9/PA11), JP1.10, JP5.3, JP7.4, U1.11 (T1IN)
SWCLK: IC3.20 (PA14), JP5.5
SWDIO: IC3.19 (PA13), JP5.4
TX1OUT_232: JP7.1, U1.14 (T1OUT)
V+: C6.1, U1.2 (V+)
V-: C5.1, U1.6 (V-)

Notes on the sheet:
RS-232
TTL/CMOS
3.0V < VCC < 5.5V

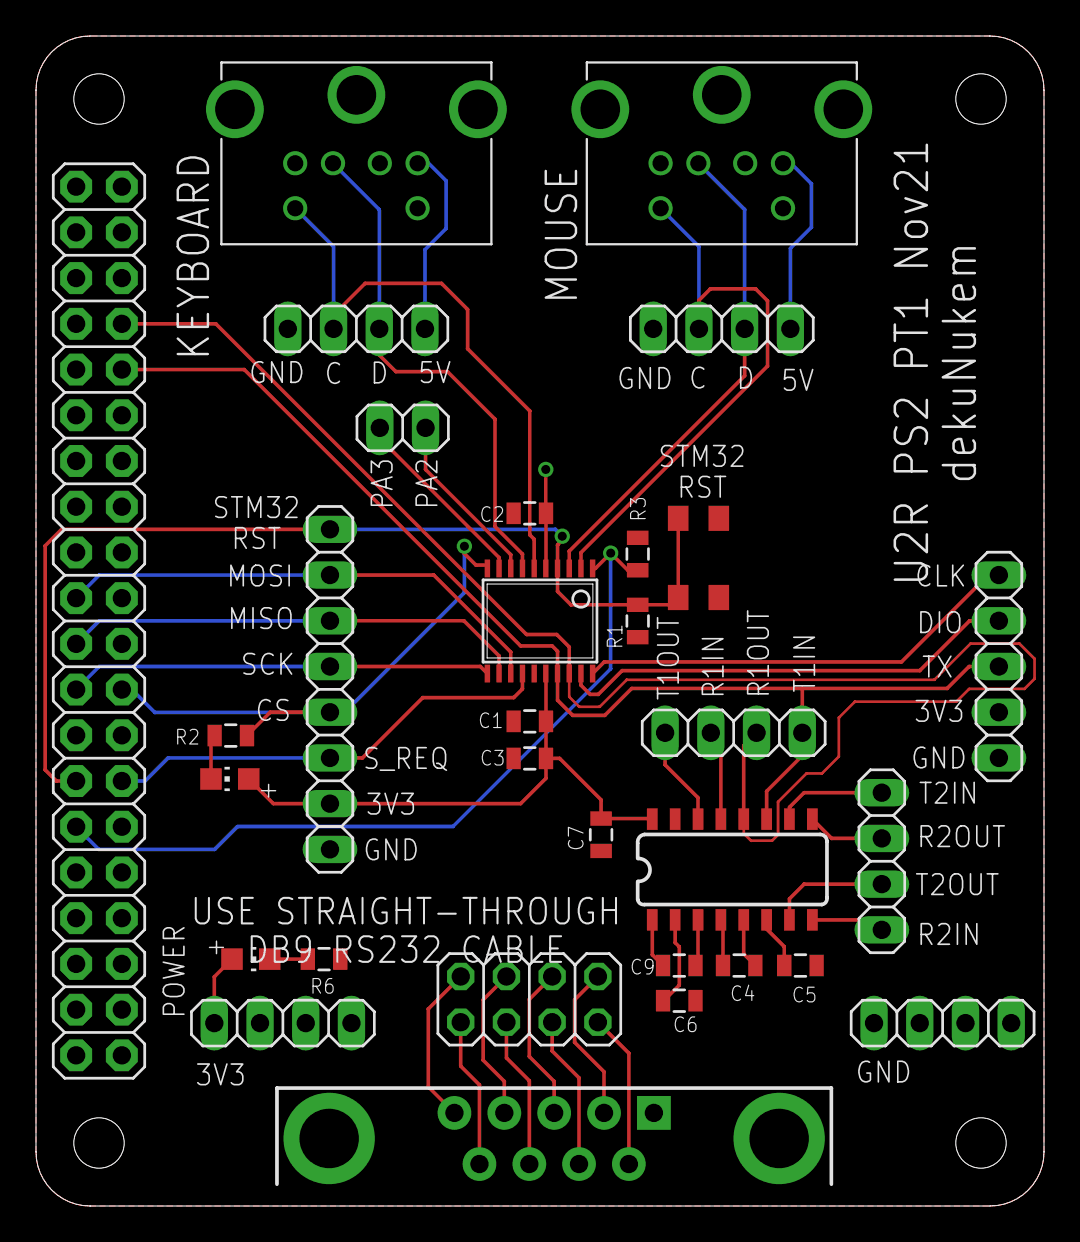
[picture p148: board ps2.brd from above]

Board: 2 copper layers, 56.0 x 65.0 mm, 35 parts (0 on the bottom side), 43 nets.
