dekuNukem/USB4VC/pcb/custom_board/u2x.brd

## EAGLE design pcb/custom_board/u2x.brd (2021-11-26)

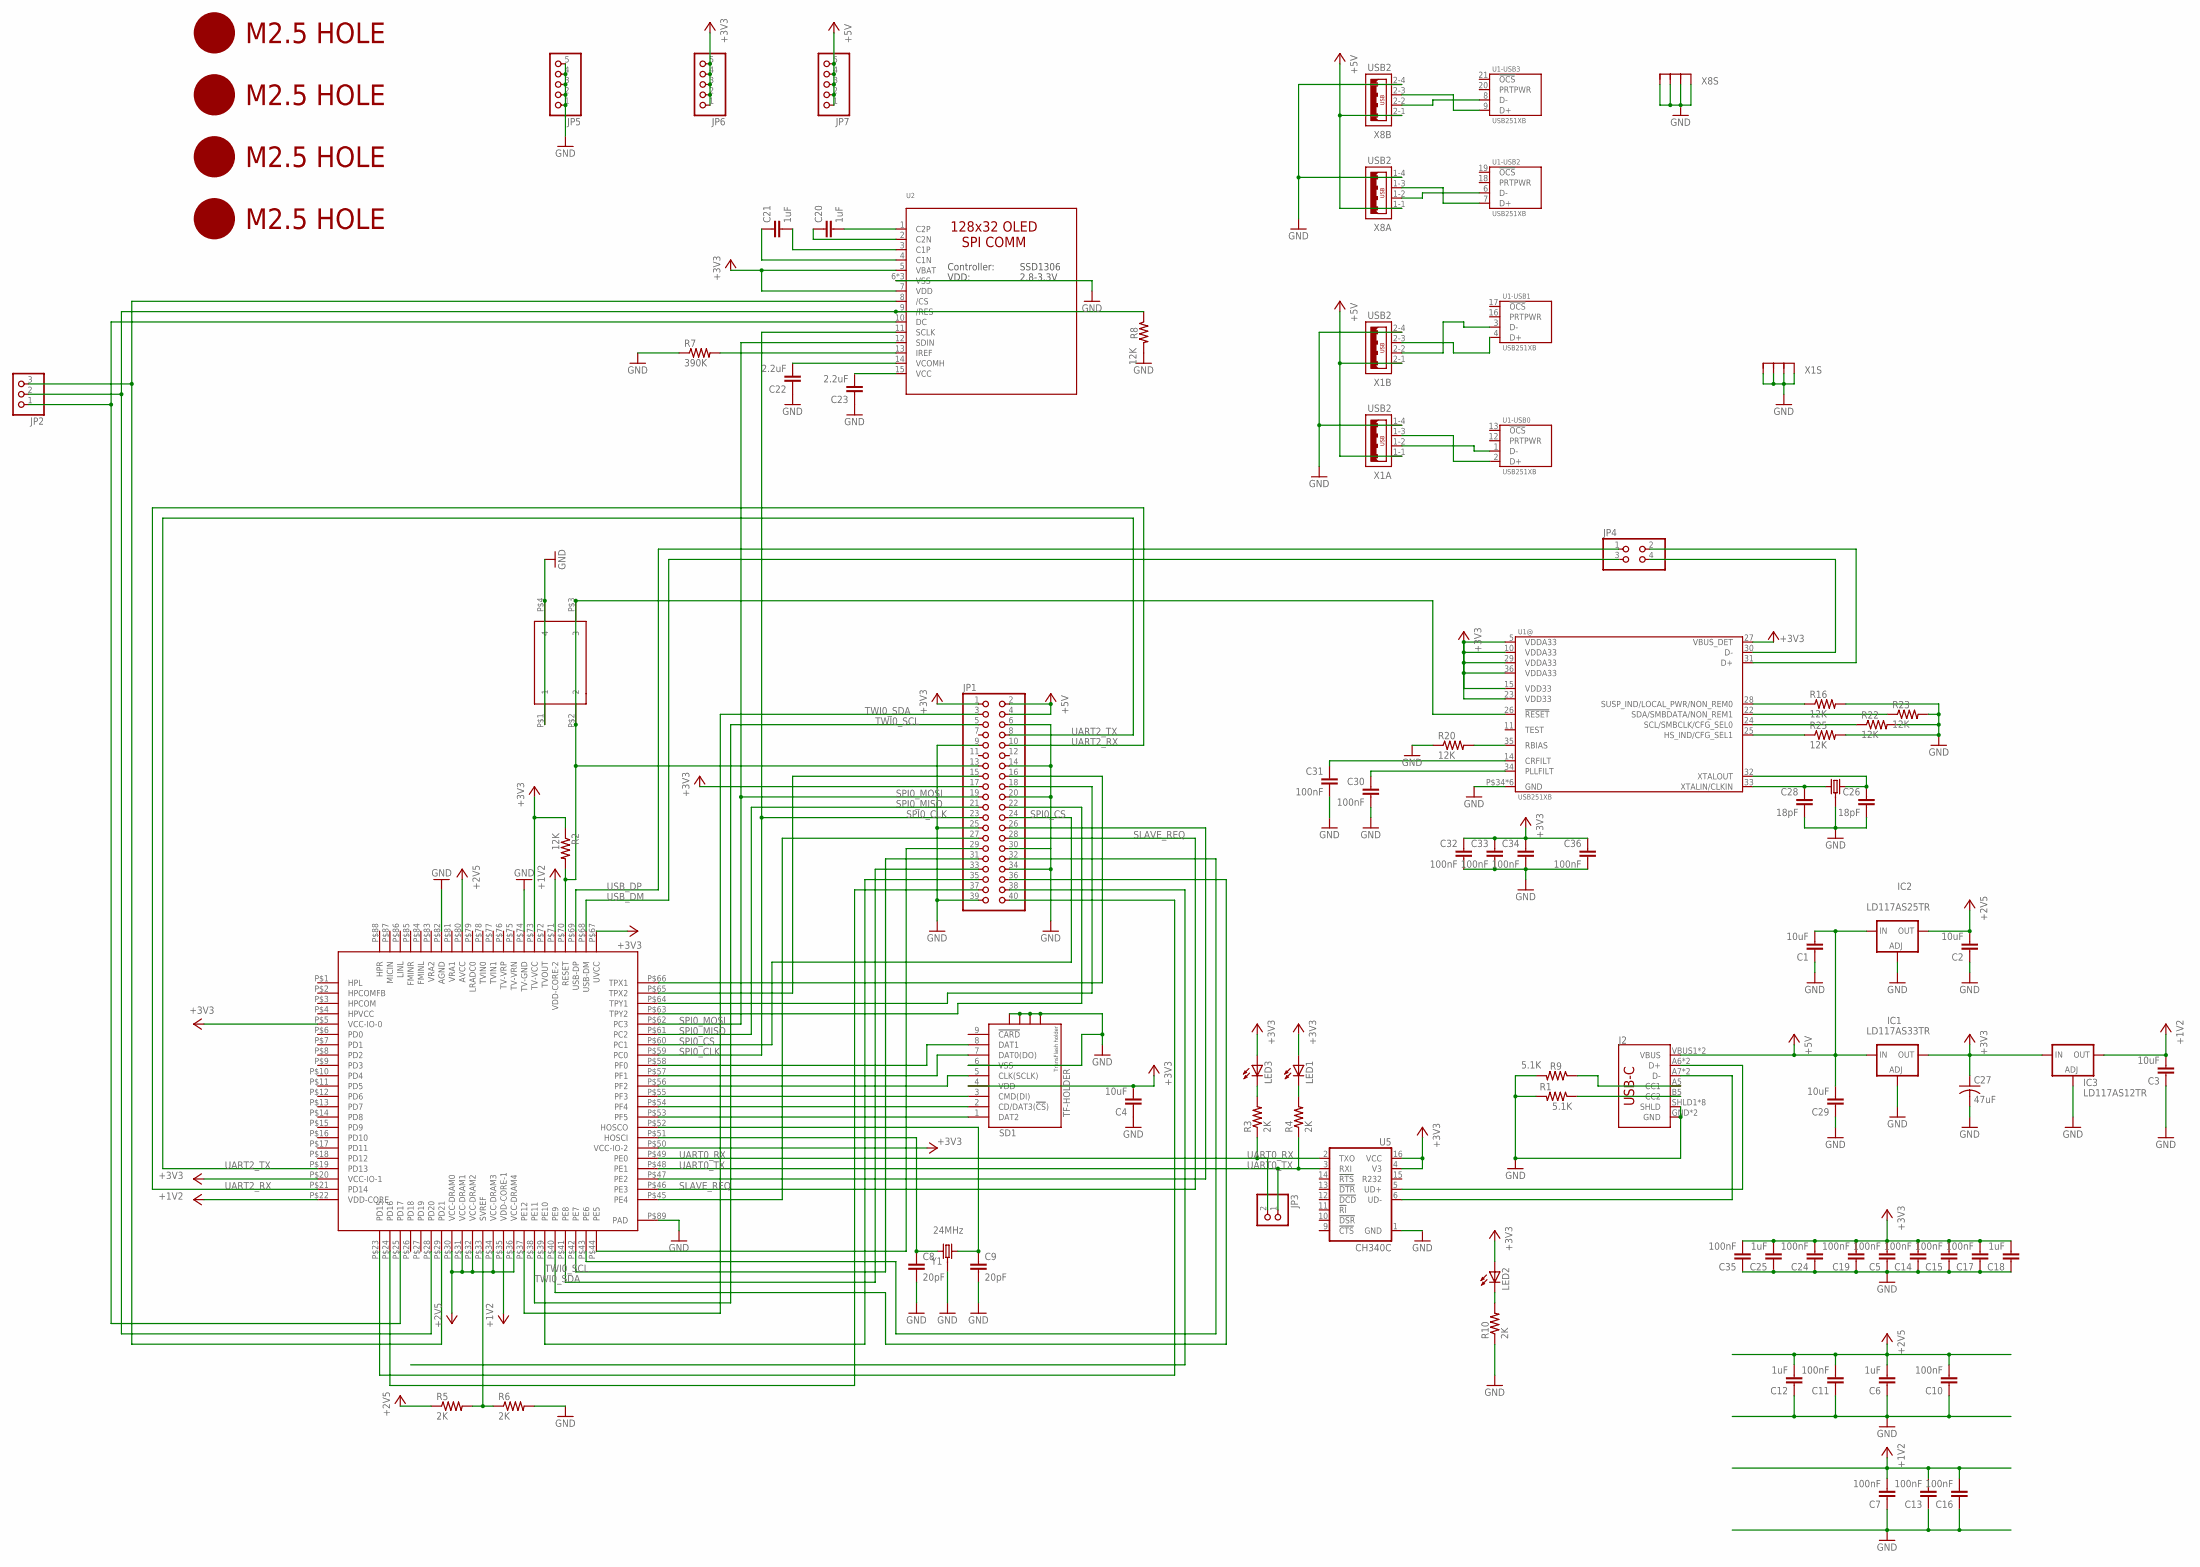
[picture p149: schematic u2x.sch]

Parts:
C1, C2, C3, C4, C29: 10uF; 0805
C5, C7, C10, C11, C13, C14, C15, C16, C17, C19, C24, C30, C31, C32, C33, C34, C35, C36: 100nF; 0805
C6, C12, C18, C20, C21, C25: 1uF; 0805
C8, C9: 20pF; 0805
C22, C23: 2.2uF; 0805
C26, C28: 18pF; 0805
C27: 47uF; C1210
IC1: LD117AS33TR; SOT223
IC2: LD117AS25TR; SOT223
IC3: LD117AS12TR; SOT223
J2: USB_C16PIN; USB-C-16P
JP1: PINHD-2X20-BIG; 2X20-BIG
JP2: PINHD-1X3CB; 1X03-CLEANBIG
JP3: PINHD-1X2; 1X02
JP4: PINHD-2X2; 2X02
JP5, JP6, JP7: PINHD-1X5; 1X05
LED1, LED2, LED3: LEDCHIP-LED0805; CHIP-LED0805
R1, R9: 5.1K; 0805
R2, R8, R16, R20, R22, R23, R25: 12K; 0805
R3, R4, R5, R6, R10: 2K; 0805
R7: 390K; 0805
SD1: TF-HOLDER; TF-PULL
SW20: 324_SW; 342_SWICH_FOOT
U1: USB251XB; QFN-36
U2: LUL_DISP_OLED_UG-2864HSWEG01; LUL_UG-2864HSWEG01_1.3_WRAPAROUND
U5: CH340C; SO016
U$1: F1C100S_DEV; MQFN88
U$2, U$3, U$4, U$5: M2.5HOLE
U$16: CRYSTAL-GROUNDED; CRYSTAL-SMD-5X3
X1, X8: USB2
Y1: 24MHz; CRYSTAL-SMD-3.2X2.5MM

Connections:
+1V2: C3.2, C7.2, C13.2, C16.2, IC3.4 (OUT), U$1.P$22 (VDD-CORE), U$1.P$35 (VDD-CORE-1), U$1.P$71 (VDD-CORE-2)
+2V5: C2.2, C6.2, C10.2, C11.2, C12.2, IC2.4 (OUT), R5.1, U$1.P$30 (VCC-DRAM0), U$1.P$31 (VCC-DRAM1), U$1.P$32 (VCC-DRAM2), U$1.P$34 (VCC-DRAM3), U$1.P$36 (VCC-DRAM4), U$1.P$80 (AVCC)
+3V3: C4.2, C5.2, C14.2, C15.2, C17.2, C18.2, C19.2, C24.2, C25.2, C27.1, C32.1, C33.1, C34.1, C35.2, C36.1, IC1.4 (OUT), IC3.3 (IN), JP1.1, JP1.17, JP6.1, JP6.2, JP6.3, JP6.4, JP6.5, LED1.A, LED2.A, LED3.A, R2.1, SD1.4 (VDD), U1.5 (VDDA33), U1.10 (VDDA33), U1.15 (VDD33), U1.23 (VDD33), U1.27 (VBUS_DET), U1.29 (VDDA33), U1.36 (VDDA33), U2.5 (VBAT), U2.7 (VDD), U5.4 (V3), U5.16 (VCC), U$1.P$5 (VCC-IO-0), U$1.P$20 (VCC-IO-1), U$1.P$50 (VCC-IO-2), U$1.P$67 (UVCC), U$1.P$73 (TV-VCC)
+5V: C1.2, C29.2, IC1.3 (IN), IC2.3 (IN), J2.VBUS1 (VBUS), J2.VBUS2 (VBUS), JP1.2, JP1.4, JP7.1, JP7.2, JP7.3, JP7.4, JP7.5, X1.1-1 (1), X1.2-1 (1), X8.1-1 (1), X8.2-1 (1)
GND: C1.1, C2.1, C3.1, C4.1, C5.1, C6.1, C7.1, C8.2, C9.2, C10.1, C11.1, C12.1, C13.1, C14.1, C15.1, C16.1, C17.1, C18.1, C19.1, C22.1, C23.1, C24.1, C25.1, C26.2, C27.2, C28.2, C29.1, C30.2, C31.2, C32.2, C33.2, C34.2, C35.1, C36.2, IC1.1 (ADJ), IC2.1 (ADJ), IC3.1 (ADJ), J2.GND, J2.GND2 (GND), J2.SHLD1 (SHLD), J2.SHLD2 (SHLD), J2.SHLD3 (SHLD), J2.SHLD4 (SHLD), J2.SHLD5 (SHLD), J2.SHLD6 (SHLD), J2.SHLD7 (SHLD), J2.SHLD8 (SHLD), JP1.6, JP1.9, JP1.14, JP1.20, JP1.25, JP1.30, JP1.34, JP1.39, JP5.1, JP5.2, JP5.3, JP5.4, JP5.5, R1.2, R6.2, R7.1, R8.2, R9.2, R10.1, R16.2, R20.1, R22.2, R23.2, R25.2, SD1.6 (VSS), SD1.S1, SD1.S2, SD1.S3, SD1.S4, SW20.P$1 (1), SW20.P$4 (4), U1.P$34 (GND), U1.P$35 (GND), U1.P$36 (GND), U1.P$37 (GND), U1.P$38 (GND), U1.PAD (GND), U2.6 (VSS), U2.16 (VSS), U2.17 (VSS), U5.1 (GND), U$1.P$74 (TV-GND), U$1.P$82 (AGND), U$1.P$89 (PAD), U$16.2 (3), U$16.4 (3), X1.1-4 (4), X1.2-4 (4), X1.M1 (S1), X1.M2 (S2), X1.M3 (S3), X1.M4 (S4), X8.1-4 (4), X8.2-4 (4), X8.M1 (S1), X8.M2 (S2), X8.M3 (S3), X8.M4 (S4), Y1.2 (3), Y1.4 (3)
unnamed: SD1.8 (DAT1), U$1.P$58 (PF0)
unnamed: J2.A5 (CC1), R9.1
unnamed: C8.1, U$1.P$51 (HOSCI), Y1.1
unnamed: C9.1, U$1.P$52 (HOSCO), Y1.3 (2)
unnamed: LED1.C, R4.2
unnamed: LED3.C, R3.2
unnamed: J2.B5 (CC2), R1.1
unnamed: SD1.7 (DAT0(DO)), U$1.P$57 (PF1)
unnamed: SD1.5 (CLK(SCLK)), U$1.P$56 (PF2)
unnamed: SD1.3 (CMD(DI)), U$1.P$55 (PF3)
unnamed: SD1.2 (CD/DAT3(!CS!)), U$1.P$54 (PF4)
unnamed: SD1.1 (DAT2), U$1.P$53 (PF5)
unnamed: U1.2 (D+), X1.1-3 (3)
unnamed: R5.2, R6.1, U$1.P$33 (SVREF)
unnamed: U1.1 (D-), X1.1-2 (2)
unnamed: J2.A6 (D+), J2.B6 (D+), U5.5 (UD+)
unnamed: JP1.13, R2.2, SW20.P$2 (2), SW20.P$3 (3), U1.26 (!RESET), U$1.P$70 (RESET)
unnamed: J2.A7 (D-), J2.B7 (D-), U5.6 (UD-)
unnamed: JP1.26, U$1.P$47 (PE2)
unnamed: JP1.27, U$1.P$45 (PE4)
unnamed: JP1.18, U$1.P$64 (TPY1)
unnamed: JP1.22, U$1.P$63 (TPY2)
unnamed: JP1.15, U$1.P$65 (TPX2)
unnamed: JP1.16, U$1.P$66 (TPX1)
unnamed: JP1.29, U$1.P$44 (PE5)
unnamed: JP1.32, U$1.P$43 (PE6)
unnamed: JP1.31, U$1.P$42 (PE7)
unnamed: JP1.33, U$1.P$41 (PE8)
unnamed: JP1.36, U$1.P$40 (PE9)
unnamed: JP1.35, U$1.P$39 (PE10)
unnamed: JP1.40, U$1.P$23 (PD15)
unnamed: JP1.37, U$1.P$24 (PD16)
unnamed: C20.2, U2.1 (C2P)
unnamed: C20.1, U2.2 (C2N)
unnamed: C21.2, U2.3 (C1P)
unnamed: C21.1, U2.4 (C1N)
unnamed: R7.2, U2.13 (IREF)
unnamed: C22.2, U2.14 (VCOMH)
unnamed: C23.2, U2.15 (VCC)
unnamed: JP2.3, U2.8 (/CS), U$1.P$29 (PD21)
unnamed: JP2.2, R8.1, U2.9 (/RES), U$1.P$28 (PD20)
unnamed: JP2.1, U2.10 (DC), U$1.P$25 (PD17)
unnamed: U1.4 (D+), X1.2-3 (3)
unnamed: U1.3 (D-), X1.2-2 (2)
unnamed: U1.6 (D-), X8.1-2 (2)
unnamed: U1.7 (D+), X8.1-3 (3)
unnamed: U1.8 (D-), X8.2-2 (2)
unnamed: U1.9 (D+), X8.2-3 (3)
unnamed: JP4.4, U1.30 (D-)
unnamed: JP4.2, U1.31 (D+)
unnamed: LED2.C, R10.2
unnamed: R20.2, U1.35 (RBIAS)
unnamed: C28.1, U1.33 (XTALIN/CLKIN), U$16.1 (2)
unnamed: C26.1, U1.32 (XTALOUT), U$16.3 (1)
unnamed: C31.1, U1.14 (CRFILT)
unnamed: C30.1, U1.34 (PLLFILT)
unnamed: R16.1, U1.28 (SUSP_IND/LOCAL_PWR/NON_REM0)
unnamed: R25.1, U1.25 (HS_IND/CFG_SEL1)
unnamed: R23.1, U1.22 (SDA/SMBDATA/NON_REM1)
unnamed: R22.1, U1.24 (SCL/SMBCLK/CFG_SEL0)
SLAVE_REQ: JP1.28, U$1.P$46 (PE3)
SPI0_CLK: JP1.23, U2.11 (SCLK), U$1.P$59 (PC0)
SPI0_CS: JP1.24, U$1.P$60 (PC1)
SPI0_MISO: JP1.21, U$1.P$61 (PC2)
SPI0_MOSI: JP1.19, U2.12 (SDIN), U$1.P$62 (PC3)
TWI0_SCL: JP1.5, U$1.P$38 (PE11)
TWI0_SDA: JP1.3, U$1.P$37 (PE12)
UART0_RX: JP3.2, R3.1, U5.2 (TXO), U$1.P$49 (PE0)
UART0_TX: JP3.1, R4.1, U5.3 (RXI), U$1.P$48 (PE1)
UART2_RX: JP1.10, U$1.P$21 (PD14)
UART2_TX: JP1.8, U$1.P$19 (PD13)
USB_DM: JP4.3, U$1.P$68 (USB-DM)
USB_DP: JP4.1, U$1.P$69 (USB-DP)

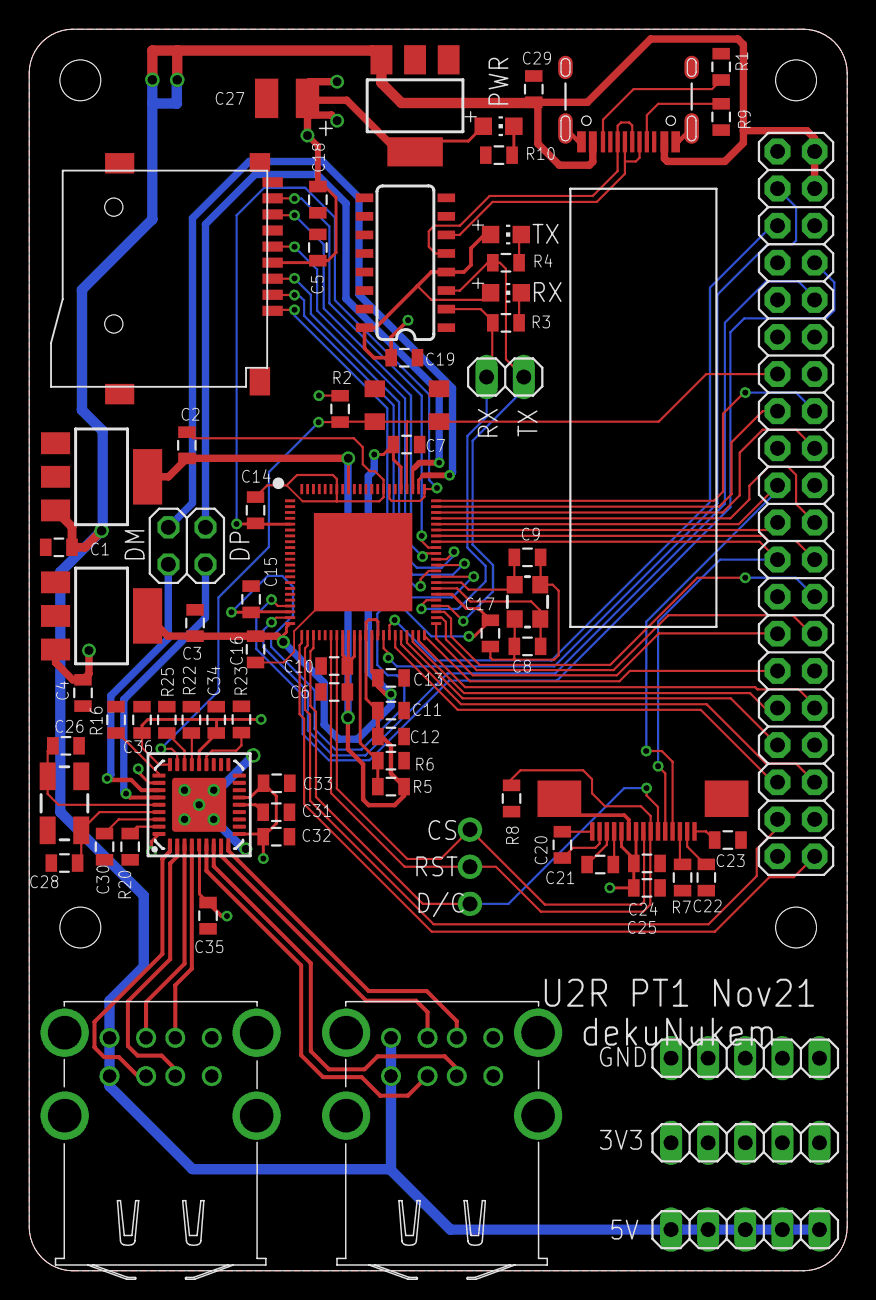
[picture p150: board u2x.brd from above]

Board: 2 copper layers, 56.0 x 85.0 mm, 79 parts (0 on the bottom side), 78 nets.
