dekuNukem/USB4VC/resources/Adafruit-Prototyping-Pi-Plate-PCB-master/Adafruit proto pi plate.brd

## EAGLE design resources/Adafruit-Prototyping-Pi-Plate-PCB-master/Adafruit proto pi plate.brd (2021-11-11)

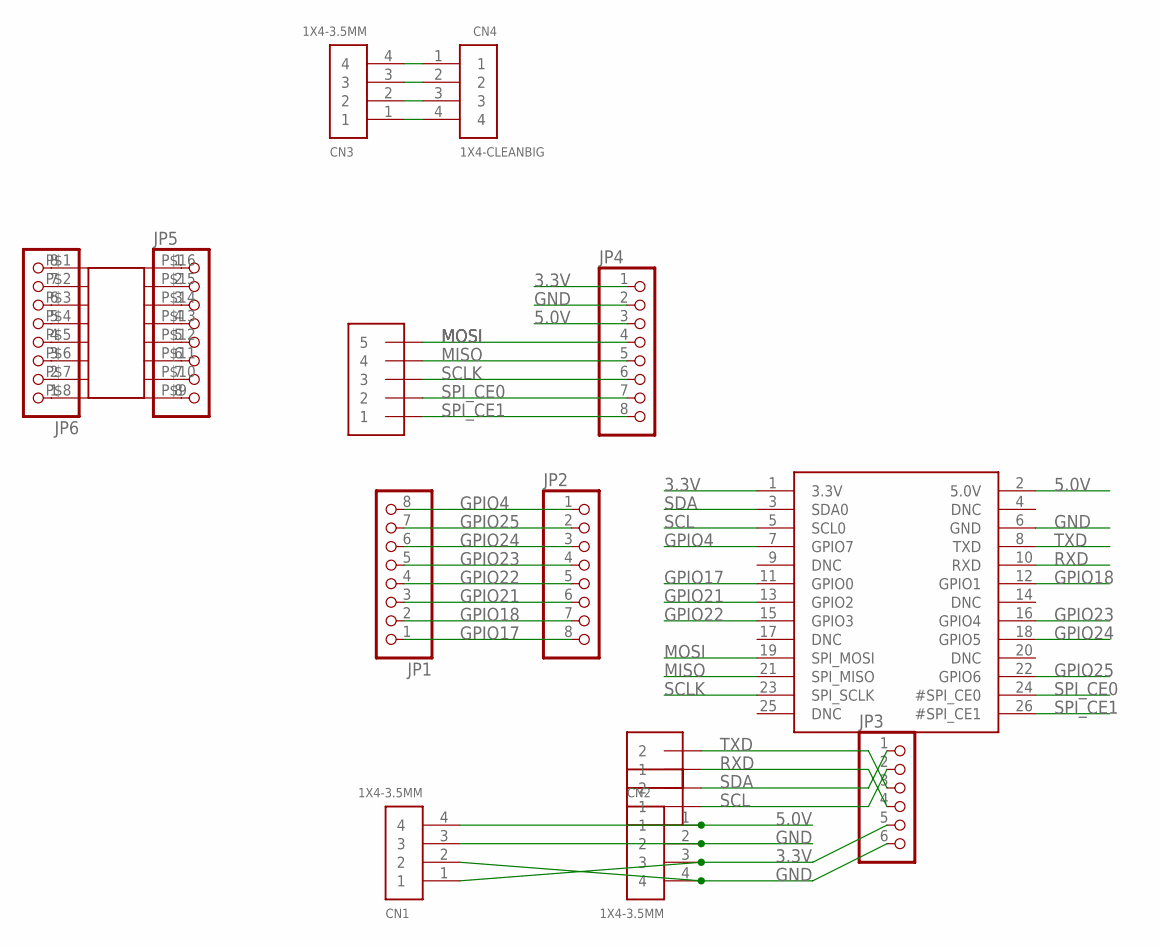
[picture p151: schematic Adafruit proto pi plate.sch]

Parts:
CN1, CN2, CN3: 1X4-3.5MM; 1X04-3.5MM
CN4: 1X4-CLEANBIG; 1X04-CLEANBIG
J1, J2: 1X2-3.5MM
J3: 1X5; 1X05-3.5MM
JP1: PINHD-1X8-3.5MM; 1X08-3.5MM
JP2, JP4, JP5, JP6: PINHD-1X8BIG; 1X08-BIG
JP3: PINHD-1X6B; 1X06-BIG
U$1: RASPBERRYPI_BB; RASBERRYPI_SHIELD
U$2: SMD-16SOIC; SO-16NMW

Connections:
3.3V: CN1.1, CN2.3, JP3.5, JP4.1, U$1.1 (3.3V)
5.0V: CN1.4, CN2.1, JP4.3, U$1.2 (5.0V)
GND: CN1.2, CN1.3, CN2.2, CN2.4, JP3.6, JP4.2, U$1.6 (GND)
GPIO4: JP1.8, JP2.1, U$1.7 (GPIO7)
GPIO17: JP1.1, JP2.8, U$1.11 (GPIO0)
GPIO18: JP1.2, JP2.7, U$1.12 (GPIO1)
GPIO21: JP1.3, JP2.6, U$1.13 (GPIO2)
GPIO22: JP1.4, JP2.5, U$1.15 (GPIO3)
GPIO23: JP1.5, JP2.4, U$1.16 (GPIO4)
GPIO24: JP1.6, JP2.3, U$1.18 (GPIO5)
GPIO25: JP1.7, JP2.2, U$1.22 (GPIO6)
MISO: J3.4, JP4.5, U$1.21 (SPI_MISO)
MOSI: J3.5, JP4.4, U$1.19 (SPI_MOSI)
unnamed: JP5.1, U$2.P$16
unnamed: JP5.2, U$2.P$15
unnamed: JP5.3, U$2.P$14
unnamed: JP5.4, U$2.P$13
unnamed: JP5.5, U$2.P$12
unnamed: JP5.6, U$2.P$11
unnamed: JP5.7, U$2.P$10
unnamed: JP5.8, U$2.P$9
unnamed: JP6.1, U$2.P$8
unnamed: JP6.2, U$2.P$7
unnamed: JP6.3, U$2.P$6
unnamed: JP6.4, U$2.P$5
unnamed: JP6.5, U$2.P$4
unnamed: JP6.6, U$2.P$3
unnamed: JP6.7, U$2.P$2
unnamed: JP6.8, U$2.P$1
unnamed: CN3.4, CN4.1
unnamed: CN3.3, CN4.2
unnamed: CN3.2, CN4.3
unnamed: CN3.1, CN4.4
RXD: J2.1, JP3.4, U$1.10 (RXD)
SCL: J1.1, JP3.2, U$1.5 (SCL0)
SCLK: J3.3, JP4.6, U$1.23 (SPI_SCLK)
SDA: J1.2, JP3.1, U$1.3 (SDA0)
SPI_CE0: J3.2, JP4.7, U$1.24 (#SPI_CE0)
SPI_CE1: J3.1, JP4.8, U$1.26 (#SPI_CE1)
TXD: J2.2, JP3.3, U$1.8 (TXD)

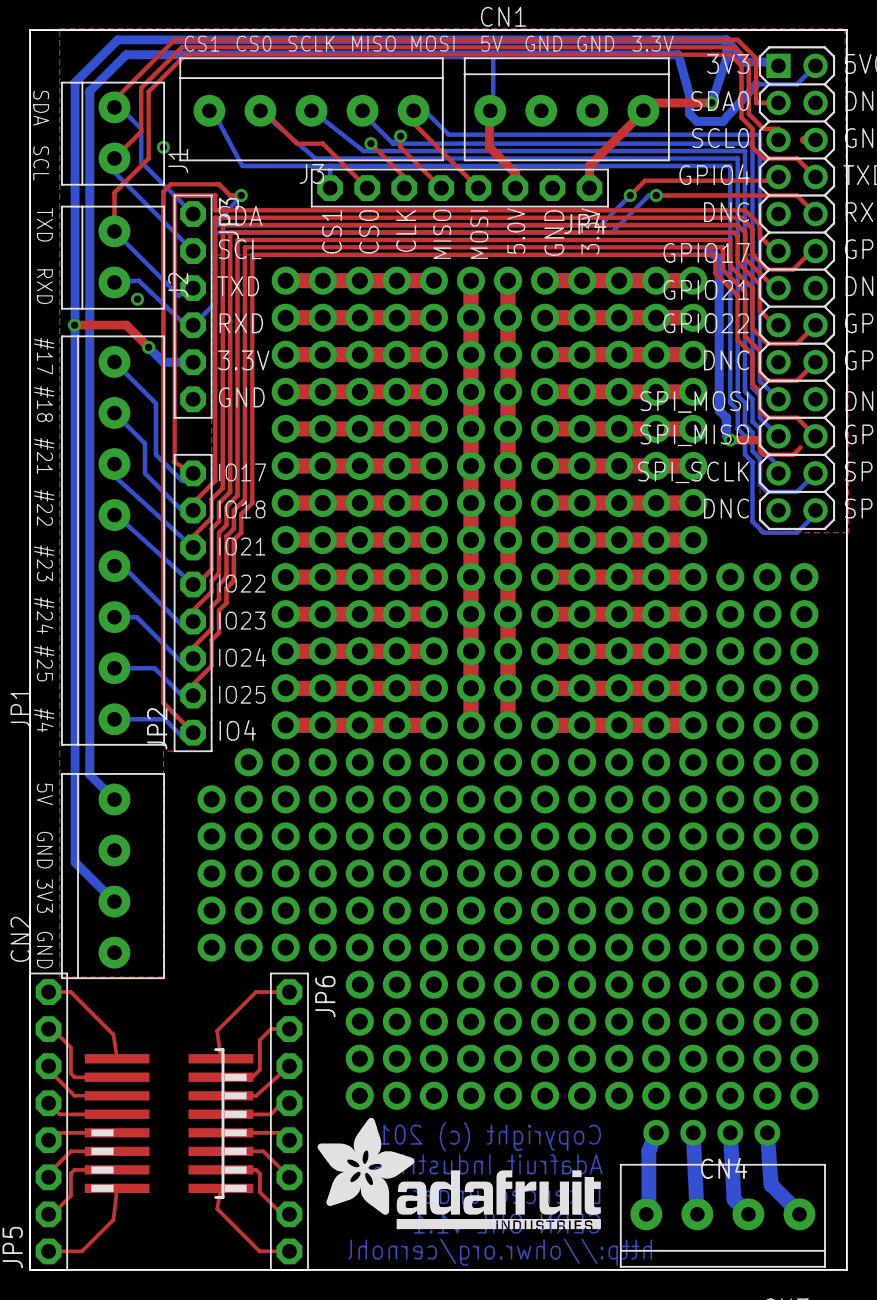
[picture p152: board Adafruit proto pi plate.brd from above]

Board: 2 copper layers, 56.0 x 85.0 mm, 16 parts (0 on the bottom side), 40 nets.

Other parts of the board:
U$3: ADAFRUIT_TEXT_20MM
