dekuNukem/USB4VC/resources/max3232/MAX3232_Breakout_v11.brd

## EAGLE design resources/max3232/MAX3232_Breakout_v11.brd (2021-11-08)

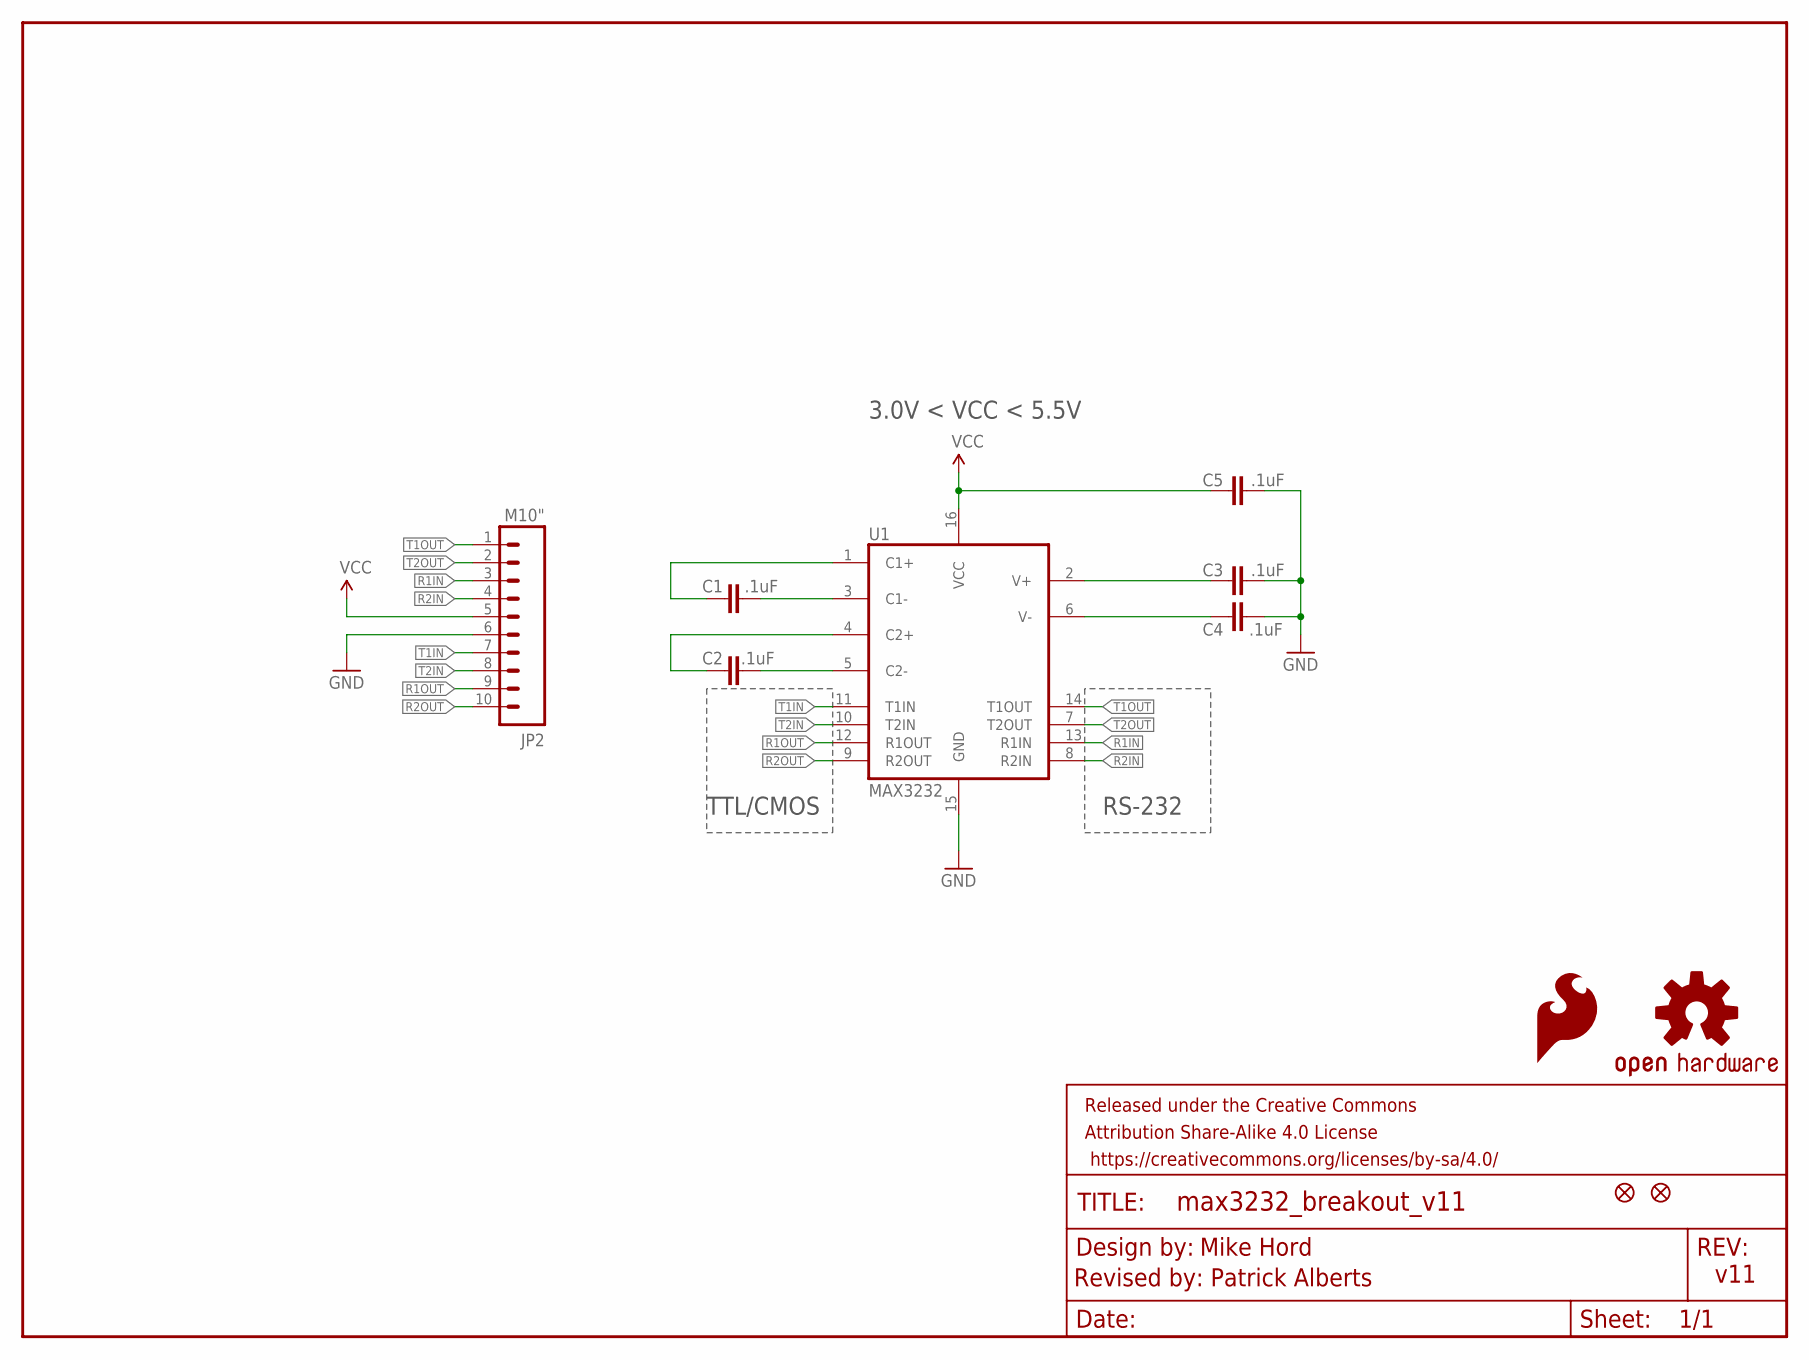
[picture p153: schematic MAX3232_Breakout_v11.sch]

Parts:
C1, C2, C3, C4, C5: .1uF; 0603-CAP
FID1, FID2: FIDUCIAL1X2; FIDUCIAL-1X2
FRAME1: FRAME-LETTER; CREATIVE_COMMONS
JP2: M10"; 1X10
LOGO1: SFE_LOGO_FLAME.1_INCH; SFE_LOGO_FLAME_.1
U1: MAX3232; SO016
U$1: OSHW-LOGOS; OSHW-LOGO-S

Connections:
C1+: C1.1, U1.1 (C1+)
C1-: C1.2, U1.3 (C1-)
C2+: C2.1, U1.4 (C2+)
C2-: C2.2, U1.5 (C2-)
GND: C3.2, C4.2, C5.2, JP2.6, U1.15 (GND)
R1IN: JP2.3, U1.13 (R1IN)
R1OUT: JP2.9, U1.12 (R1OUT)
R2IN: JP2.4, U1.8 (R2IN)
R2OUT: JP2.10, U1.9 (R2OUT)
T1IN: JP2.7, U1.11 (T1IN)
T1OUT: JP2.1, U1.14 (T1OUT)
T2IN: JP2.8, U1.10 (T2IN)
T2OUT: JP2.2, U1.7 (T2OUT)
V+: C3.1, U1.2 (V+)
V-: C4.1, U1.6 (V-)
VCC: C5.1, JP2.5, U1.16 (VCC)

Notes on the sheet:
RS-232
TTL/CMOS
3.0V < VCC < 5.5V
Mike Hord
Revised by: Patrick Alberts
v11

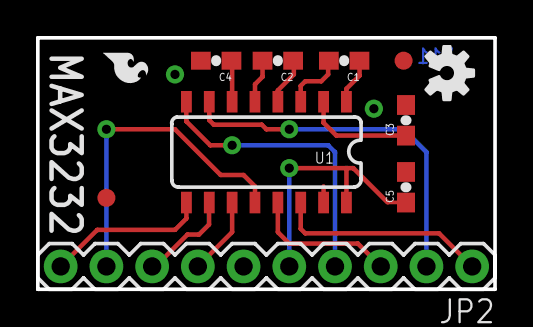
[picture p154: board MAX3232_Breakout_v11.brd from above]

Board: 2 copper layers, 25.4 x 14.0 mm, 12 parts (0 on the bottom side), 16 nets.
