dekuNukem/USB4VC/resources/ch340/Serial-Basic-CH340C-and-USBC.brd

## EAGLE design resources/ch340/Serial-Basic-CH340C-and-USBC.brd (2021-11-04)

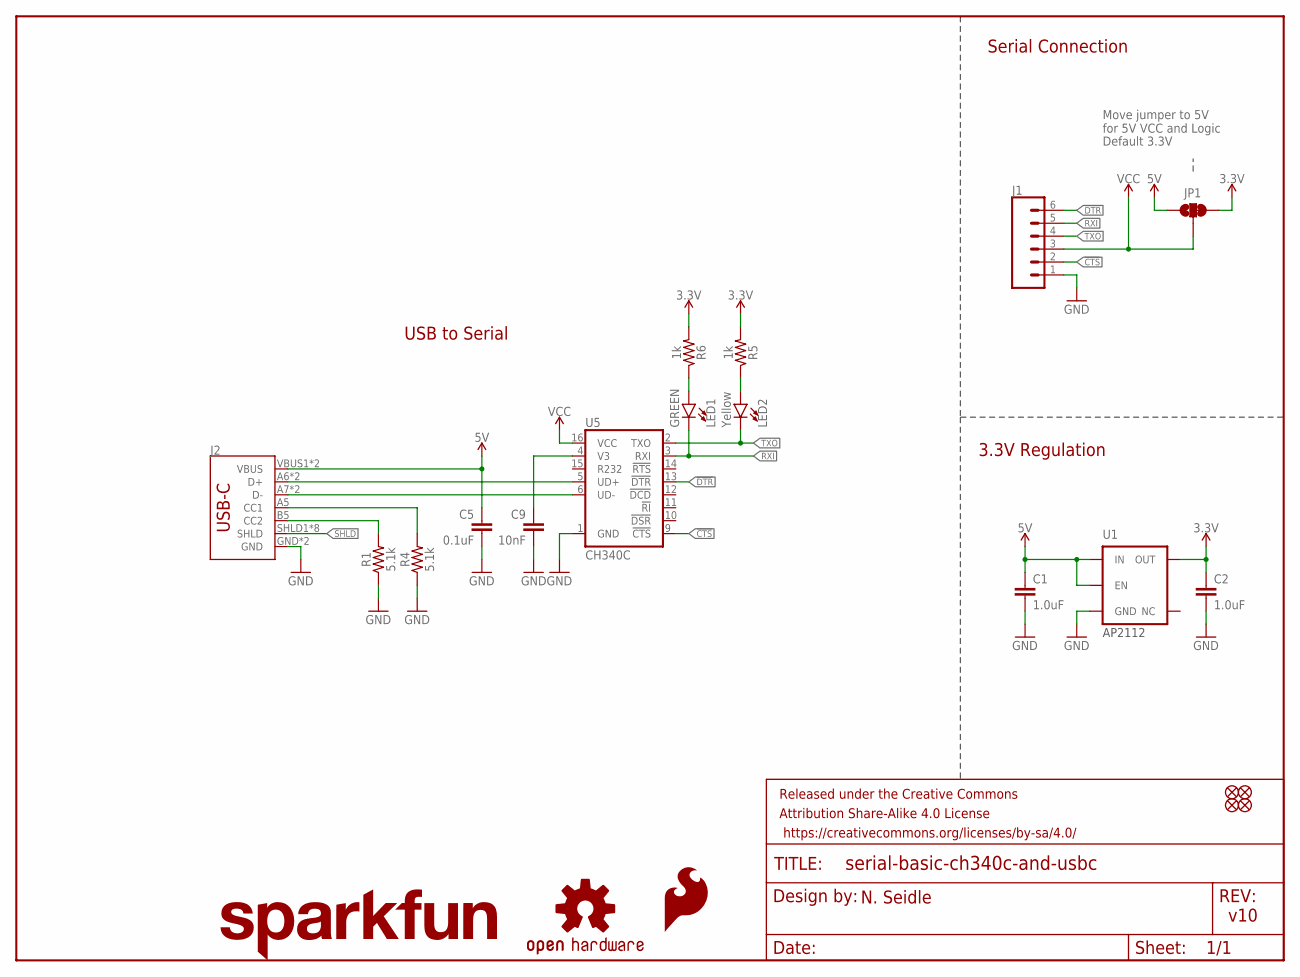
[picture p155: schematic Serial-Basic-CH340C-and-USBC.sch]

Parts:
C1, C2: 1.0uF; 0603
C5: 0.1uF; 0603
C9: 10nF; 0603
FRAME1: FRAME-LETTER; CREATIVE_COMMONS
J1: CONN_06SMD-FEMALE-V2; 1X06-SMD-FEMALE
J2: USB_C16PIN; USB-C-16P
JP1: JUMPER-SMT_3_1-NC_TRACE_SILK; SMT-JUMPER_3_1-NC_TRACE_SILK
JP3, JP4, JP5, JP6: FIDUCIAL1X2; FIDUCIAL-1X2
LED1: GREEN; LED-0603
LED2: Yellow; LED-0603
LOGO1: OSHW-LOGOS; OSHW-LOGO-S
LOGO2: SFE_LOGO_FLAME.1_INCH; SFE_LOGO_FLAME_.1
LOGO3: SFE_LOGO_NAME.1_INCH; SFE_LOGO_NAME_.1
R1, R4: 5.1k; 0603
R5, R6: 1k; 0603
U1: 3.3V; SOT23-5
U5: CH340C; SO016

Connections:
3.3V: C2.1, JP1.3, R5.2, R6.2, U1.5 (OUT)
5V: C1.1, C5.1, J2.VBUS1 (VBUS), J2.VBUS2 (VBUS), JP1.1, U1.1 (IN), U1.3 (EN)
!CTS: J1.2, U5.9 (!CTS)
!DTR: J1.6, U5.13 (!DTR)
CC1: J2.A5 (CC1), R4.2
CC2: J2.B5 (CC2), R1.2
D+: J2.A6 (D+), J2.B6 (D+), U5.5 (UD+)
D-: J2.A7 (D-), J2.B7 (D-), U5.6 (UD-)
GND: C1.2, C2.2, C5.2, C9.2, J1.1, J2.GND, J2.GND2 (GND), R1.1, R4.1, U1.2 (GND), U5.1 (GND)
unnamed: C9.1, U5.4 (V3)
unnamed: LED1.A, R6.1
unnamed: LED2.A, R5.1
RXI: J1.5, LED1.C, U5.3 (RXI)
SHLD: J2.SHLD1 (SHLD), J2.SHLD2 (SHLD), J2.SHLD3 (SHLD), J2.SHLD4 (SHLD), J2.SHLD5 (SHLD), J2.SHLD6 (SHLD), J2.SHLD7 (SHLD), J2.SHLD8 (SHLD)
TXO: J1.4, LED2.C, U5.2 (TXO)
VCC: J1.3, JP1.2, U5.16 (VCC)

Notes on the sheet:
Default 3.3V
v10
USB to Serial
3.3V Regulation
N. Seidle
Move jumper to 5V for 5V VCC and Logic
Serial Connection
AP2112

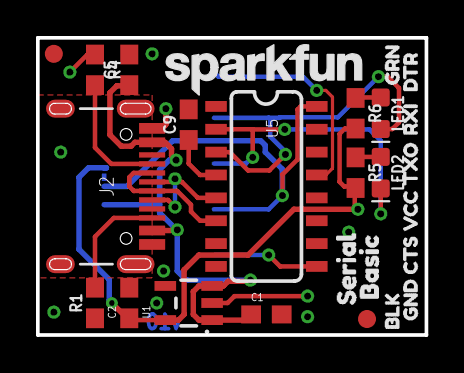
[picture p156: board Serial-Basic-CH340C-and-USBC.brd from above]

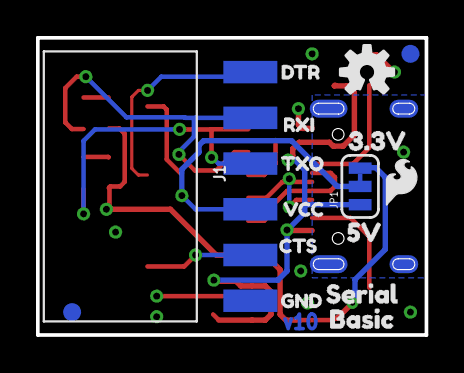
[picture p157: board Serial-Basic-CH340C-and-USBC.brd from below]

Board: 2 copper layers, 21.6 x 16.5 mm, 43 parts (16 on the bottom side), 16 nets.

Other parts of the board:
U$1, U$14: CTS1
U$2: 3#3V8
U$3: 5V9
U$4, U$9: SERIAL0
U$5, U$12: TXO0
U$6, U$13: VCC2
U$7, U$11: BASIC1
U$8, U$18: DTR0
U$10, U$21: RXI1
U$15, U$19: GND5
U$17: BLK6
U$20: GRN7
