dekuNukem/USB4VC/resources/sparkfun oled/OLED Display.brd

## EAGLE design resources/sparkfun oled/OLED Display.brd (2021-11-04)

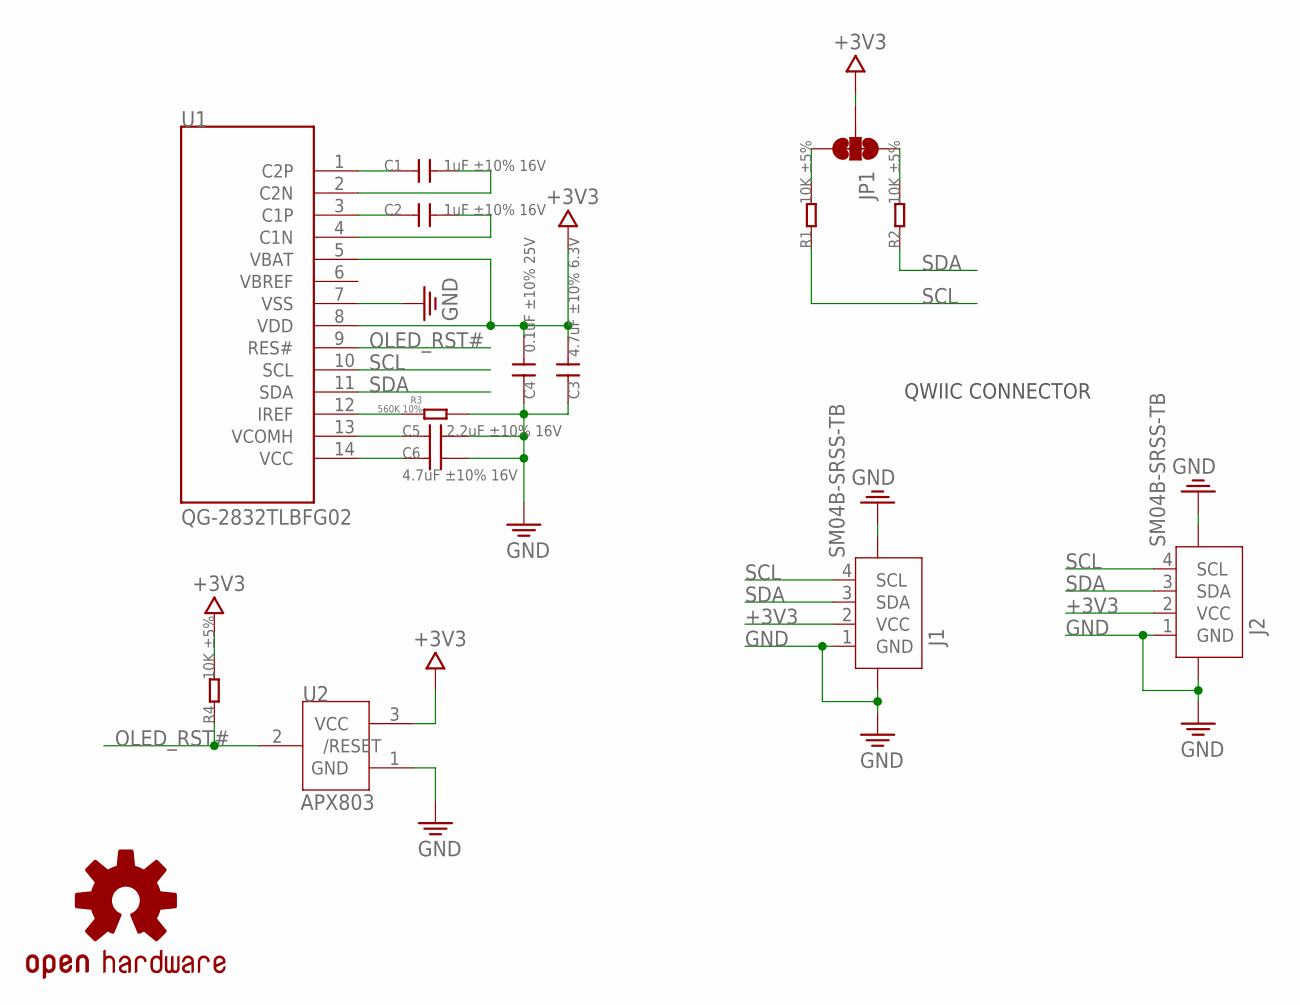
[picture p158: schematic OLED Display.sch]

Parts:
C1, C2: 1uF ±10% 16V; 0603
C3: 4.7uF ±10% 6.3V; 0603
C4: 0.1uF ±10% 25V; 0603
C5: 2.2uF ±10% 16V; 0603
C6: 4.7uF ±10% 16V; 0603
J1, J2: SM04B-SRSS-TB; JST-SH-4P
JP1: SMT-JUMPER_3_2-NC_TRACE
LOGO2: OSHW-LOGOMINI; OSHW-LOGO-MINI
R1, R2, R4: 10K ±5%; 0603
R3: 560K 10%; 0603
U1: QG-2832TLBFG02; OLED-12832
U2: APX803; SOT23

Connections:
+3V3: C3.1, C4.1, J1.2 (VCC), J2.2 (VCC), JP1.2, R4.2, U1.5 (VBAT), U1.8 (VDD), U2.3 (VCC)
GND: C3.2, C4.2, C5.2, C6.2, J1.1 (GND), J1.NC1 (5), J1.NC2 (6), J2.1 (GND), J2.NC1 (5), J2.NC2 (6), R3.1, U1.7 (VSS), U2.1 (GND)
unnamed: C1.2, U1.1 (C2P)
unnamed: C1.1, U1.2 (C2N)
unnamed: C2.2, U1.3 (C1P)
unnamed: C2.1, U1.4 (C1N)
unnamed: JP1.3, R1.2
unnamed: C5.1, U1.13 (VCOMH)
unnamed: C6.1, U1.14 (VCC)
unnamed: JP1.1, R2.2
unnamed: R3.2, U1.12 (IREF)
OLED_RST#: R4.1, U1.9 (RES#), U2.2 (/RESET)
SCL: J1.4 (SCL), J2.4 (SCL), R1.1, U1.10 (SCL)
SDA: J1.3 (SDA), J2.3 (SDA), R2.1, U1.11 (SDA)

Notes on the sheet:
QWIIC CONNECTOR

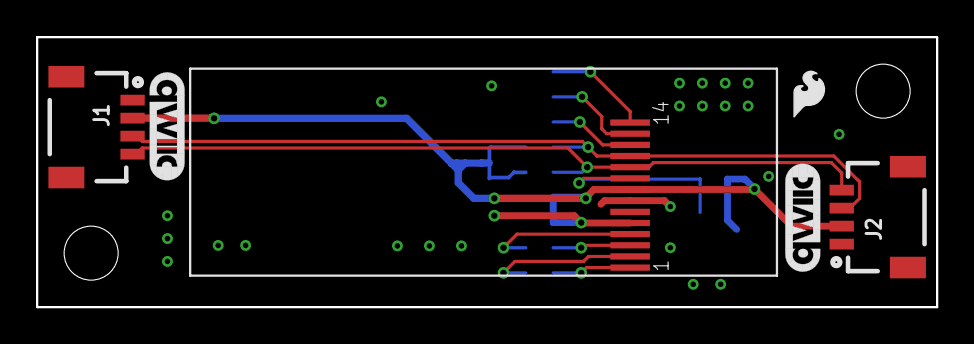
[picture p159: board OLED Display.brd from above]

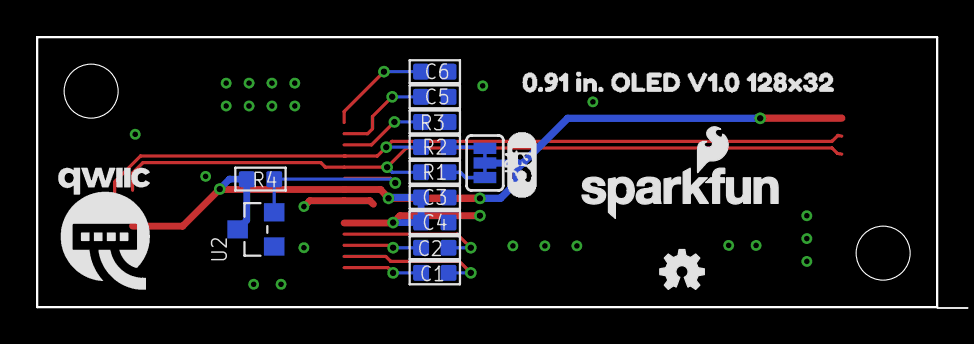
[picture p160: board OLED Display.brd from below]

Board: 2 copper layers, 50.0 x 15.0 mm, 23 parts (17 on the bottom side), 14 nets.

Other parts of the board:
U$6: QWIIC-LOGO-MEDIUM
U$7: 0#91_IN#_OLED_V1#0_128X320
U$8: SFE_LOGO_FLAME_.1
U$9: SFE_LOGO_NAME_FLAME_.1
U$11, U$12: QWIIC_6MM
U$20: I_SUPER2_C-()-04
