dekuNukem/USB4VC/resources/Adafruit-128x32-I2C-OLED-Breakout-PCB-master/Adafruit OLED 128x32 Mono I2C STEMMA QT rev B.brd

## EAGLE design resources/Adafruit-128x32-I2C-OLED-Breakout-PCB-master/Adafruit OLED 128x32 Mono I2C STEMMA QT rev B.brd (2021-11-04)

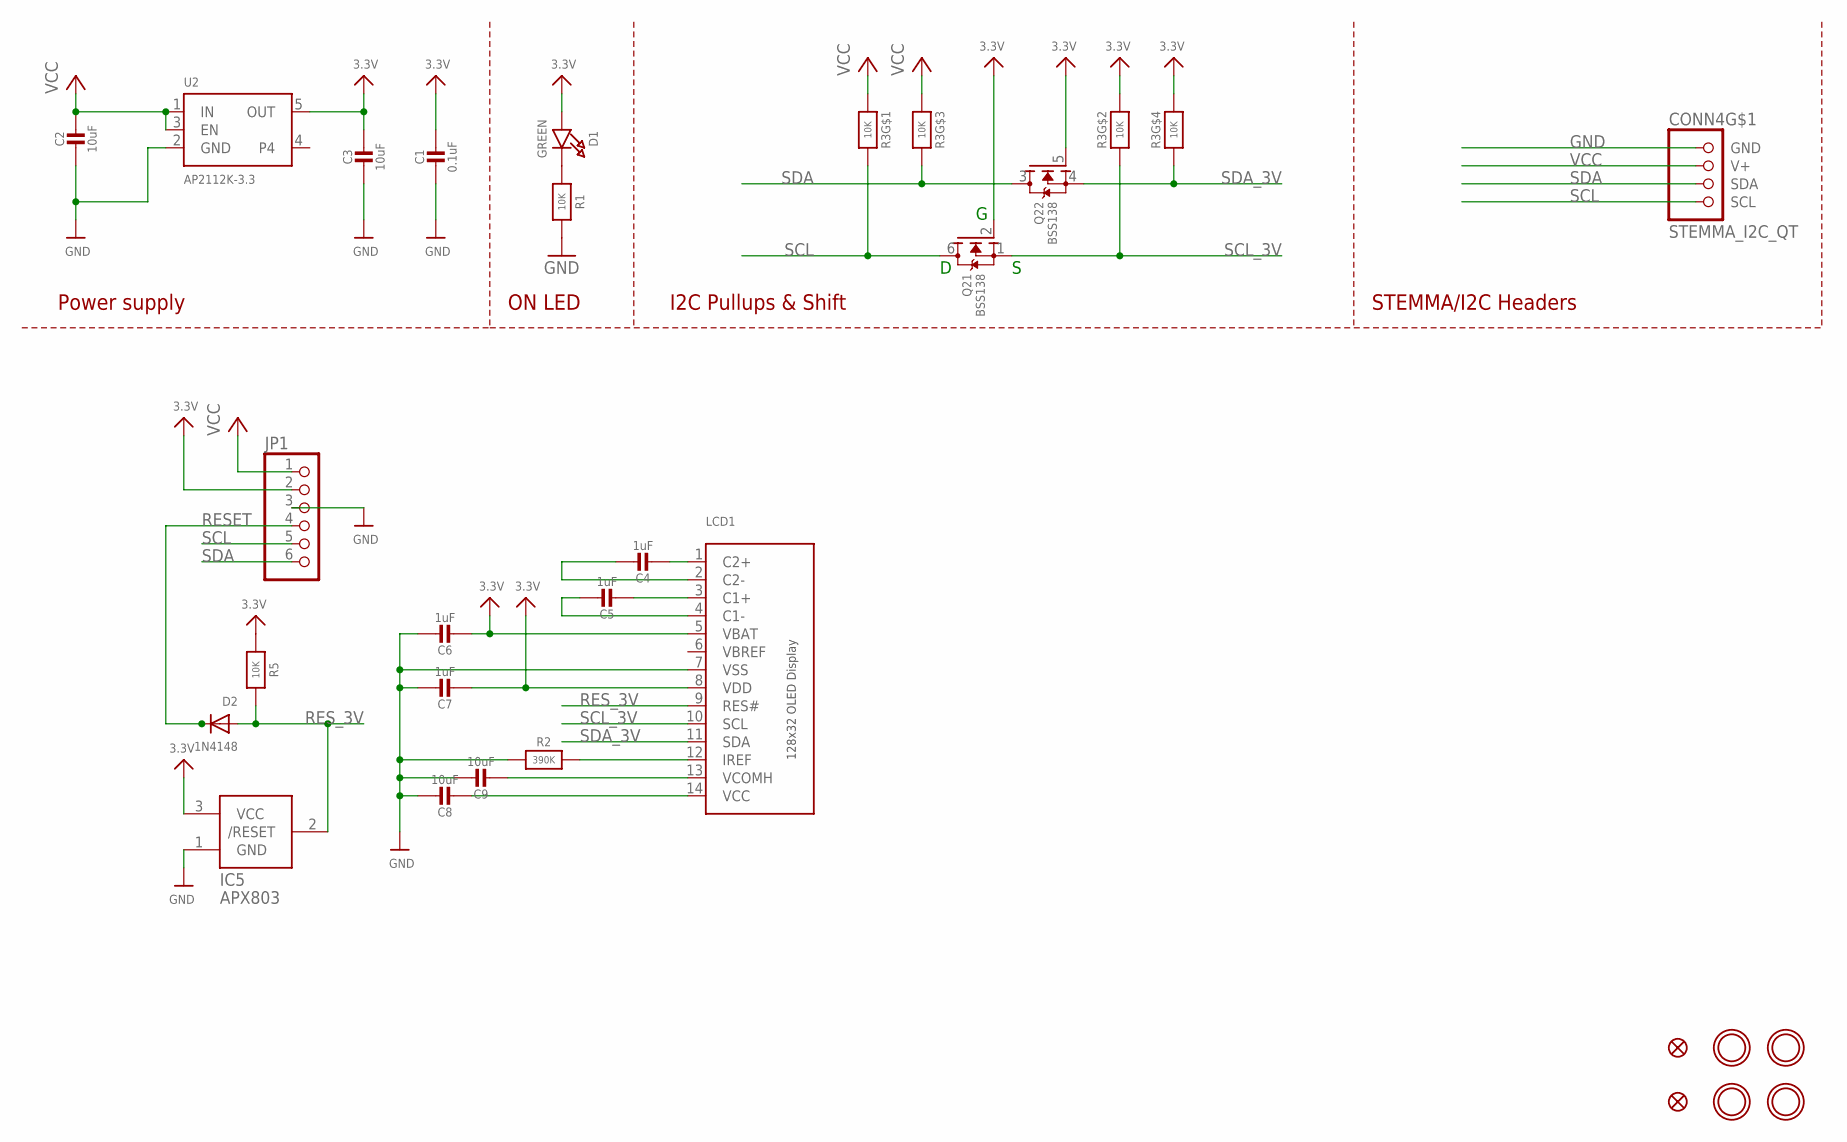
[picture p161: schematic Adafruit OLED 128x32 Mono I2C STEMMA QT rev B.sch]

Parts:
C1: 0.1uF; 0603-NO
C2, C3, C8, C9: 10uF; 0805-NO
C4, C5, C6, C7: 1uF; 0805-NO
CONN4: STEMMA_I2C_QT; JST_SH4
D1: GREEN; CHIPLED_0603_NOOUTLINE
D2: 1N4148; SOD-323F
FID3, FID4: FIDUCIAL_1MM
IC5: APX803; SOT23
JP1: HEADER-1X670MIL; 1X06_ROUND_70
LCD1: DISP_OLED_UG-2832HSWEG02; UG-2832HSWEG02_WRAPUNDER
Q2: BSS138; SOT363
R1, R5: 10K; 0603-NO
R2: 390K; 0603-NO
R3: 10K; RESPACK_4X0603
U2: AP2112K-3.3; SOT23-5
U$1, U$17, U$19, U$21: MOUNTINGHOLE2.5; MOUNTINGHOLE_2.5_PLATED

Connections:
3.3V: C1.1, C3.1, C6.2, C7.2, D1.A, IC5.3 (VCC), JP1.2, LCD1.5 (VBAT), LCD1.8 (VDD), Q2.2 (G), Q2.5 (G), R3.2 (1), R3.4 (1), R5.2, U2.5 (OUT)
GND: C1.2, C2.2, C3.2, C6.1, C7.1, C8.1, C9.1, CONN4.1 (GND), IC5.1 (GND), JP1.3, LCD1.7 (VSS), R1.2, R2.1, U2.2 (GND)
unnamed: C4.2, LCD1.1 (C2+)
unnamed: D1.C, R1.1
unnamed: C4.1, LCD1.2 (C2-)
unnamed: C5.2, LCD1.3 (C1+)
unnamed: C5.1, LCD1.4 (C1-)
unnamed: C9.2, LCD1.13 (VCOMH)
unnamed: LCD1.12 (IREF), R2.2
unnamed: C8.2, LCD1.14 (VCC)
RESET: D2.C, JP1.4
RES_3V: D2.A, IC5.2 (/RESET), LCD1.9 (RES#), R5.1
SCL: CONN4.4 (SCL), JP1.5, Q2.6 (D), R3.8 (2)
SCL_3V: LCD1.10 (SCL), Q2.1 (S), R3.7 (2)
SDA: CONN4.3 (SDA), JP1.6, Q2.3 (D), R3.6 (2)
SDA_3V: LCD1.11 (SDA), Q2.4 (S), R3.5 (2)
VBREF: LCD1.6 (VBREF)
VCC: C2.1, CONN4.2 (V+), JP1.1, R3.1, R3.3 (1), U2.1 (IN), U2.3 (EN)

Notes on the sheet:
I2C Pullups & Shift
STEMMA/I2C Headers
ON LED
Power supply
