dekuNukem/USB4VC/resources/Adafruit-128x32-I2C-OLED-Breakout-PCB-master/Adafruit OLED 128x32 Mono I2C STEMMA QT rev B.brd

## EAGLE design resources/Adafruit-128x32-I2C-OLED-Breakout-PCB-master/Adafruit OLED 128x32 Mono I2C STEMMA QT rev B.brd (continued)

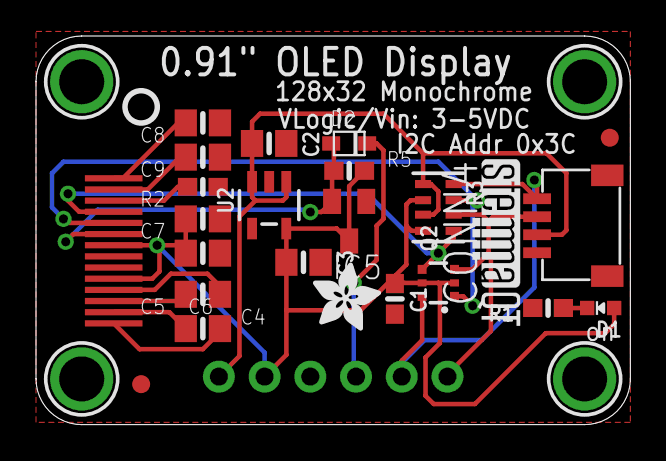
[picture p162: board Adafruit OLED 128x32 Mono I2C STEMMA QT rev B.brd from above]

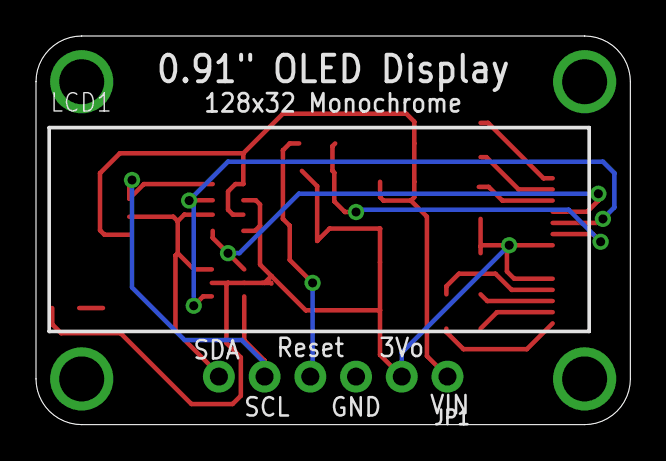
[picture p163: board Adafruit OLED 128x32 Mono I2C STEMMA QT rev B.brd from below]

Board: 2 copper layers, 33.0 x 21.6 mm, 30 parts (2 on the bottom side), 17 nets.

Other parts of the board:
U$22: ADAFRUIT_3.5MM
U$25: PCBFEAT-REV-040
U$31: STEMMAQT
