dekuNukem/USB4VC/resources/Adafruit-128x32-I2C-OLED-Breakout-PCB-master/Adafruit OLED 128x32 Mono I2C.brd

## EAGLE design resources/Adafruit-128x32-I2C-OLED-Breakout-PCB-master/Adafruit OLED 128x32 Mono I2C.brd (2021-11-04)

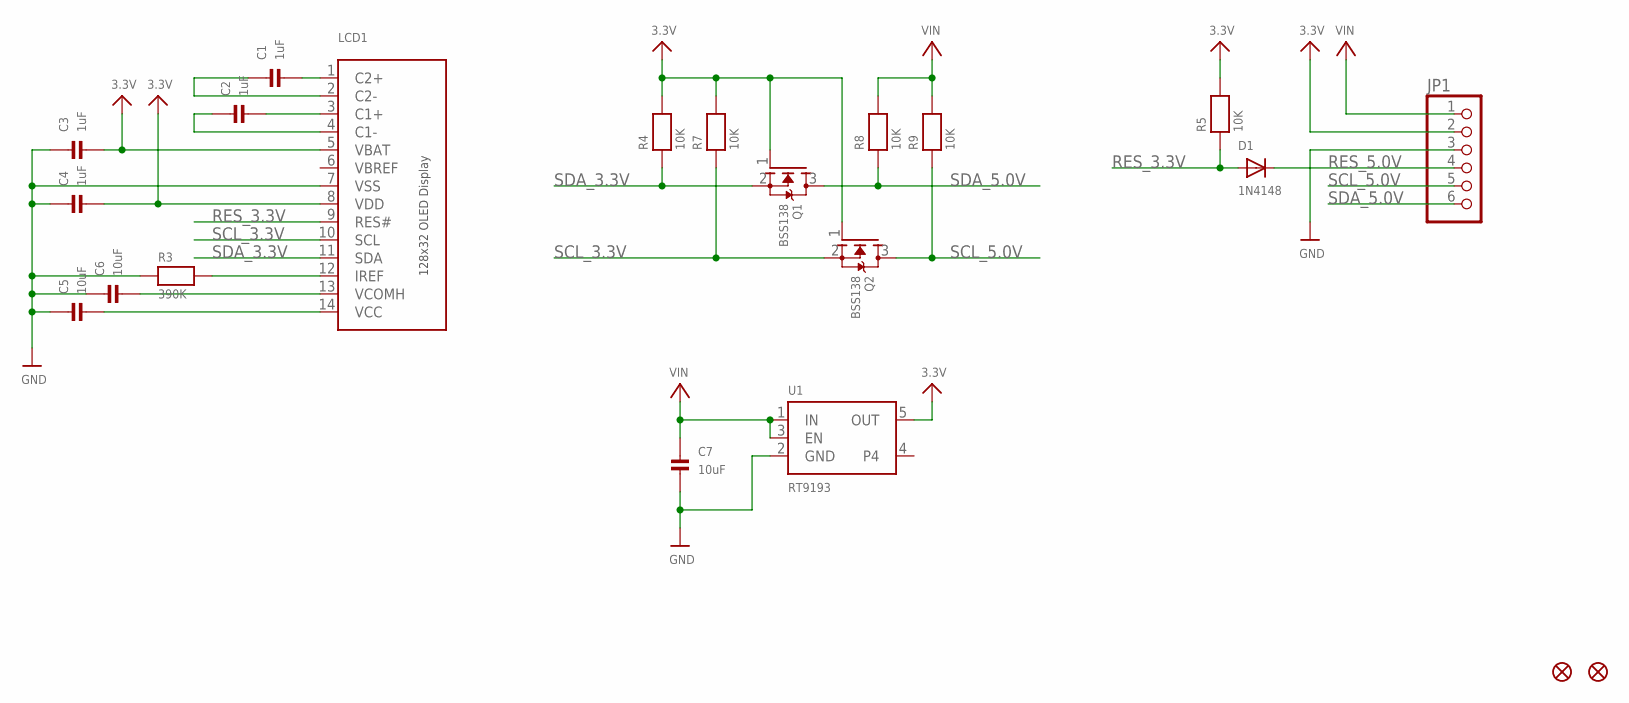
[picture p164: schematic Adafruit OLED 128x32 Mono I2C.sch]

Parts:
C1, C2, C3, C4: 1uF; 0805
C5, C6, C7: 10uF; 0805
D1: 1N4148; SOD-323F
FID1, FID2: FIDUCIAL""; FIDUCIAL_1MM
JP1: HEADER-1X670MIL; 1X06_ROUND_70
LCD1: DISP_OLED_UG-2832HSWEG02; UG-2832HSWEG02_WRAPUNDER
Q1, Q2: BSS138; SOT23-WIDE
R3: 390K; 0805
R4, R5, R7, R8, R9: 10K; 0805
U1: RT9193; SOT23-5

Connections:
3.3V: C3.2, C4.2, JP1.2, LCD1.5 (VBAT), LCD1.8 (VDD), Q1.1 (G), Q2.1 (G), R4.2, R5.2, R7.2, U1.5 (OUT)
GND: C3.1, C4.1, C5.1, C6.1, C7.2, JP1.3, LCD1.7 (VSS), R3.1, U1.2 (GND)
unnamed: C1.2, LCD1.1 (C2+)
unnamed: C1.1, LCD1.2 (C2-)
unnamed: C2.2, LCD1.3 (C1+)
unnamed: C2.1, LCD1.4 (C1-)
unnamed: C6.2, LCD1.13 (VCOMH)
unnamed: C5.2, LCD1.14 (VCC)
unnamed: LCD1.12 (IREF), R3.2
RES_3.3V: D1.A, LCD1.9 (RES#), R5.1
RES_5.0V: D1.C, JP1.4
SCL_3.3V: LCD1.10 (SCL), Q2.2 (S), R7.1
SCL_5.0V: JP1.5, Q2.3 (D), R9.1
SDA_3.3V: LCD1.11 (SDA), Q1.2 (S), R4.1
SDA_5.0V: JP1.6, Q1.3 (D), R8.1
VBREF: LCD1.6 (VBREF)
VIN: C7.1, JP1.1, R8.2, R9.2, U1.1 (IN), U1.3 (EN)

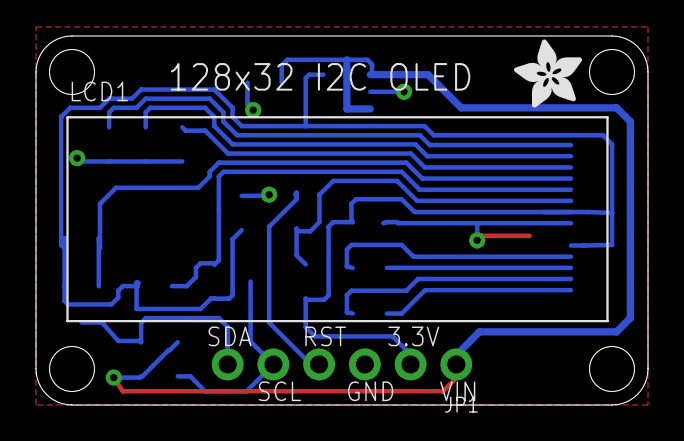
[picture p165: board Adafruit OLED 128x32 Mono I2C.brd from above]

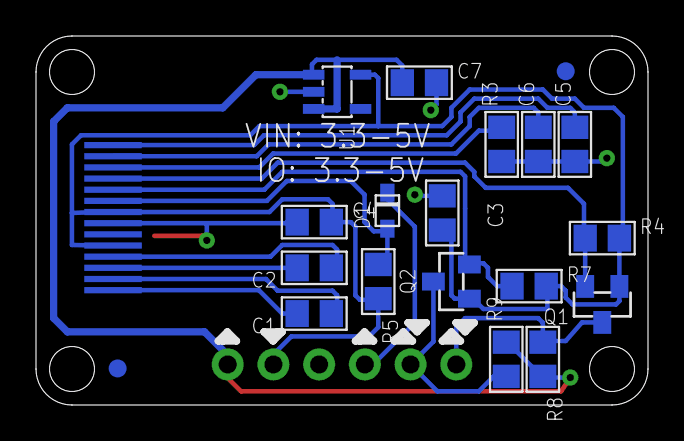
[picture p166: board Adafruit OLED 128x32 Mono I2C.brd from below]

Board: 2 copper layers, 34.0 x 20.5 mm, 22 parts (19 on the bottom side), 16 nets.

Other parts of the board:
U$16: ADAFRUIT_3.5MM
