dekuNukem/USB4VC/resources/Qwiic_USB_Hub-USB2514B-main/Hardware/Qwiic-USB_Hub.brd

## EAGLE design resources/Qwiic_USB_Hub-USB2514B-main/Hardware/Qwiic-USB_Hub.brd (2021-11-04)

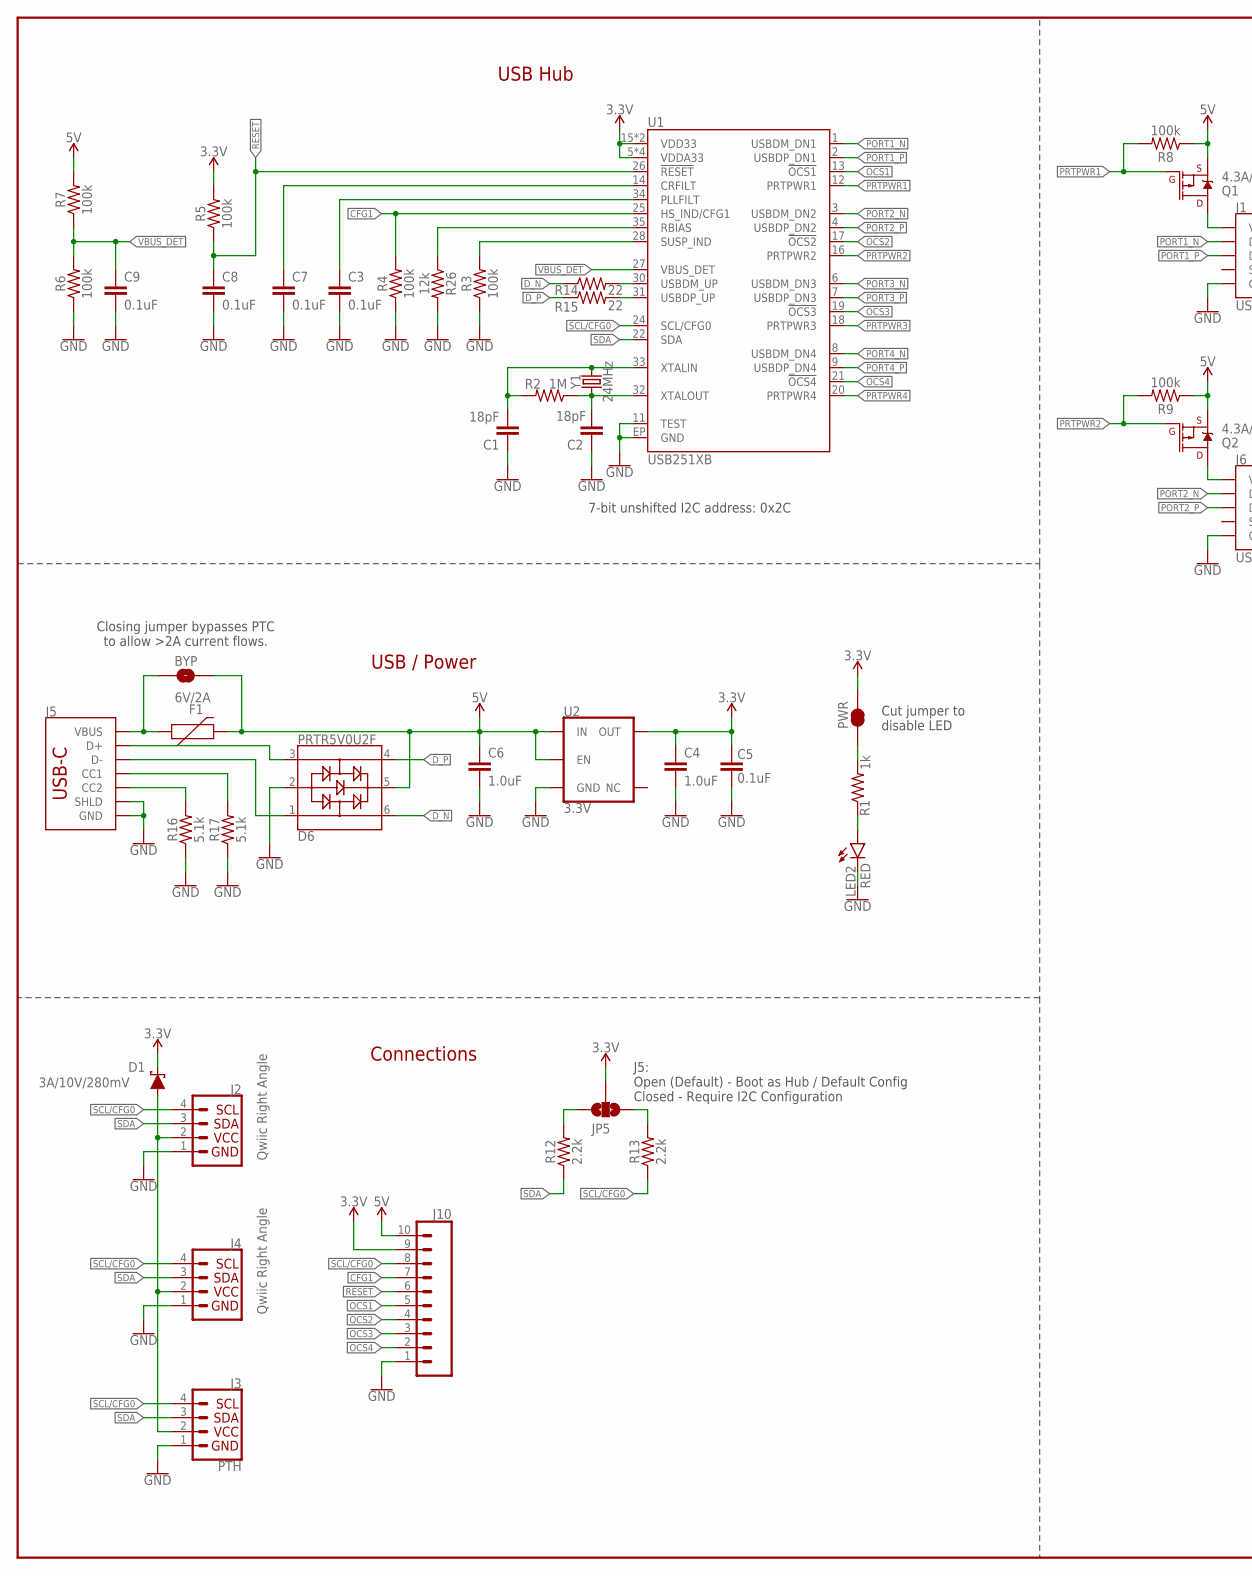
[picture p167: schematic Qwiic-USB_Hub.sch, part in row 1, column 1]

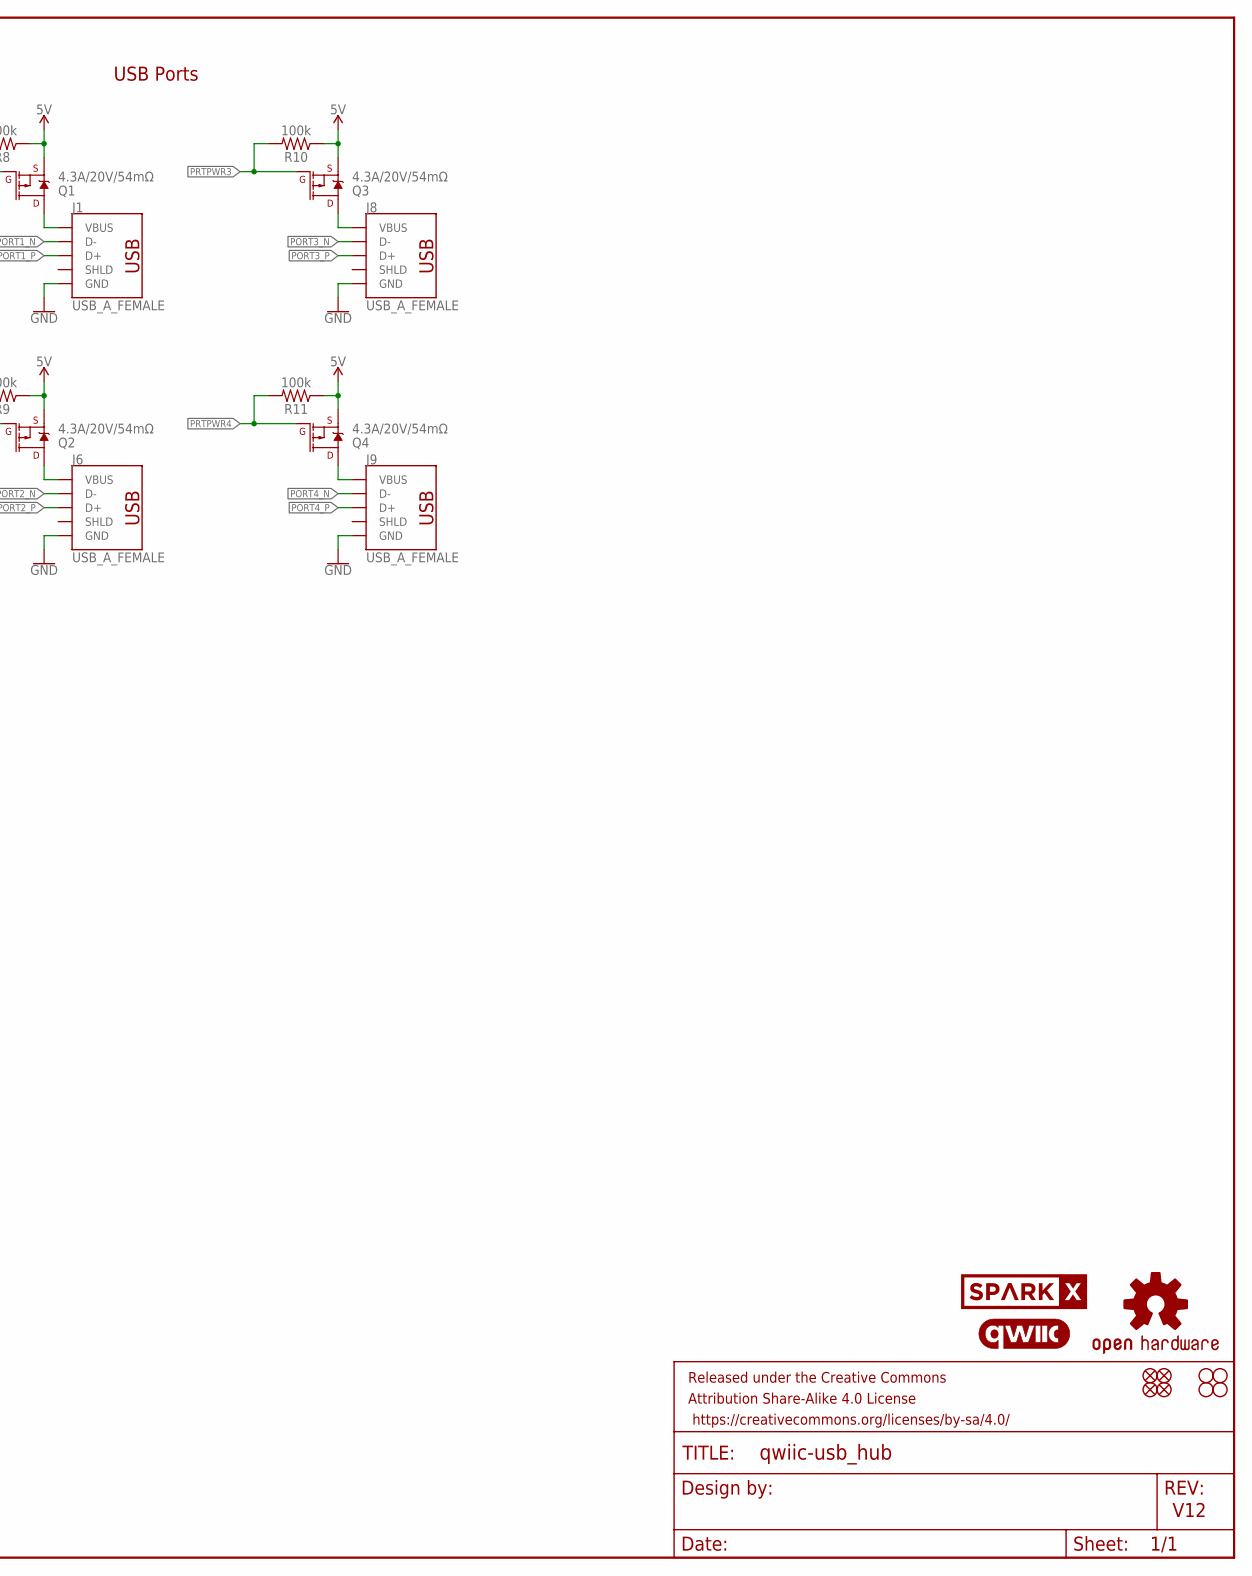
[picture p168: schematic Qwiic-USB_Hub.sch, part in row 1, column 2]

Parts:
BYP: JUMPER-SMT_2_NO_SILK; SMT-JUMPER_2_NO_SILK
C1, C2: 18pF; 0603
C3, C5, C7, C8, C9: 0.1uF; 0603
C4, C6: 1.0uF; 0603
D1: 3A/10V/280mV; SOD-323
D6: PRTR5V0U2F; SOT886
F1: 6V/2A; 1210
FRAME2: FRAME-LEDGER; CREATIVE_COMMONS
J1, J6, J8, J9: USB_A_FEMALE; USB-A-S-NOSILK-FEMALE
J2, J4: Qwiic Right Angle; JST04_1MM_RA
J3: PTH; 1X04_NO_SILK
J5: USB_C_2-LAYER_PADS; USB-C-16P-2LAYER-PADS
J10: CONN_10NO_SILK_PTH_FEMALE; 1X10_NO_SILK
JP5: JUMPER-SMT_3_NO_SILK; SMT-JUMPER_3_NO_SILK
JP21, JP61, JP71, JP81: FIDUCIALUFIDUCIAL; MICRO-FIDUCIAL
JP31, JP41, JP91, JP101: STAND-OFF
LED2: RED; LED-0603
LOGO1: OSHW-LOGOMINI; OSHW-LOGO-MINI
LOGO2: QWIIC_LOGO_CONNECTOR; QWIIC_5.5MM
PWR: JUMPER-SMT_2_NC_TRACE_SILK; SMT-JUMPER_2_NC_TRACE_SILK
Q1, Q2, Q3, Q4: 4.3A/20V/54mΩ; SOT23-3
R1: 1k; 0603
R2: 1M; 0603
R3, R4, R5, R6, R7, R8, R9, R10, R11: 100k; 0603
R12, R13: 2.2k; 0603
R14, R15: 22; 0603
R16, R17: 5.1k; 0603
R26: 12k; 0603
U1: USB251XB; QFN-36
U2: 3.3V; SOT23-5
U$5: SPARKX-LOGO4; SPARKX-MEDIUM
Y1: 24MHz; CRYSTAL-SMD-2.0X1.6MM

Connections:
3.3V: C4.1, C5.2, D1.C, J10.9, JP5.2, PWR.2, R5.2, U1.5 (VDDA33), U1.10 (VDDA33), U1.15 (VDD33), U1.23 (VDD33), U1.29 (VDDA33), U1.36 (VDDA33), U2.5 (OUT)
5V: BYP.2, C6.1, D6.5, F1.2, J10.10, Q1.2 (S), Q2.2 (S), Q3.2 (S), Q4.2 (S), R7.2, R8.1, R9.1, R10.1, R11.1, U2.1 (IN), U2.3 (EN)
!OCS1: J10.5, U1.13 (!OCS1)
!OCS2: J10.4, U1.17 (!OCS2)
!OCS3: J10.3, U1.19 (!OCS3)
!OCS4: J10.2, U1.21 (!OCS4)
!RESET: C8.1, J10.6, R5.1, U1.26 (!RESET)
CC1: J5.A5 (CC1), R17.2
CC2: J5.B5 (CC2), R16.2
CFG1: J10.7, R4.2, U1.25 (HS_IND/CFG1)
D_N: D6.6, R14.1
D_P: D6.4, R15.1
GND: C1.1, C2.1, C3.2, C4.2, C5.1, C6.2, C7.2, C8.2, C9.2, D6.2, J1.GND, J2.1, J3.1 (GND), J4.1, J5.GND, J5.GND2 (GND), J5.SHLD1 (SHLD), J5.SHLD2 (SHLD), J5.SHLD3 (SHLD), J5.SHLD4 (SHLD), J6.GND, J8.GND, J9.GND, J10.1, LED2.C, R3.1, R4.1, R6.1, R16.1, R17.1, R26.2, U1.11 (TEST), U1.EP (GND), U2.2 (GND)
unnamed: J1.VBUS, Q1.3 (D)
unnamed: J6.VBUS, Q2.3 (D)
unnamed: J8.VBUS, Q3.3 (D)
unnamed: J9.VBUS, Q4.3 (D)
unnamed: R26.1, U1.35 (RBIAS)
unnamed: C1.2, R2.2, U1.33 (XTALIN), Y1.3 (2)
unnamed: BYP.1, F1.1, J5.VBUS1 (VBUS), J5.VBUS2 (VBUS)
unnamed: C2.2, R2.1, U1.32 (XTALOUT), Y1.1
unnamed: JP5.1, R13.2
unnamed: LED2.A, R1.1
unnamed: R3.2, U1.28 (SUSP_IND)
unnamed: C3.1, U1.34 (PLLFILT)
unnamed: C7.1, U1.14 (CRFILT)
unnamed: JP5.3, R12.2
unnamed: R14.2, U1.30 (USBDM_UP)
unnamed: PWR.1, R1.2
unnamed: R15.2, U1.31 (USBDP_UP)
unnamed: D1.A, J2.2, J3.2 (VCC), J4.2
PORT1_N: J1.D-, U1.1 (USBDM_DN1)
PORT1_P: J1.D+, U1.2 (USBDP_DN1)
PORT2_N: J6.D-, U1.3 (USBDM_DN2)
PORT2_P: J6.D+, U1.4 (USBDP_DN2)
PORT3_N: J8.D-, U1.6 (USBDM_DN3)
PORT3_P: J8.D+, U1.7 (USBDP_DN3)
PORT4_N: J9.D-, U1.8 (USBDM_DN4)
PORT4_P: J9.D+, U1.9 (USBDP_DN4)
PRTPWR1: Q1.1 (G), R8.2, U1.12 (PRTPWR1)
PRTPWR2: Q2.1 (G), R9.2, U1.16 (PRTPWR2)
PRTPWR3: Q3.1 (G), R10.2, U1.18 (PRTPWR3)
PRTPWR4: Q4.1 (G), R11.2, U1.20 (PRTPWR4)
SCL/CFG0: J2.4, J3.4 (SCL), J4.4, J10.8, R13.1, U1.24 (SCL/CFG0)
SDA: J2.3, J3.3 (SDA), J4.3, R12.1, U1.22 (SDA)
UNP_D+: D6.3, J5.A6 (D+), J5.B6 (D+)
UNP_D-: D6.1, J5.A7 (D-), J5.B7 (D-)
VBUS_DET: C9.1, R6.2, R7.1, U1.27 (VBUS_DET)

Notes on the sheet:
V12
7-bit unshifted I2C address: 0x2C
Cut jumper to disable LED
USB Hub
USB / Power
USB Ports
Connections
Closing jumper bypasses PTC to allow >2A current flows.
J5: Open (Default) - Boot as Hub / Default Config Closed - Require I2C Configuration

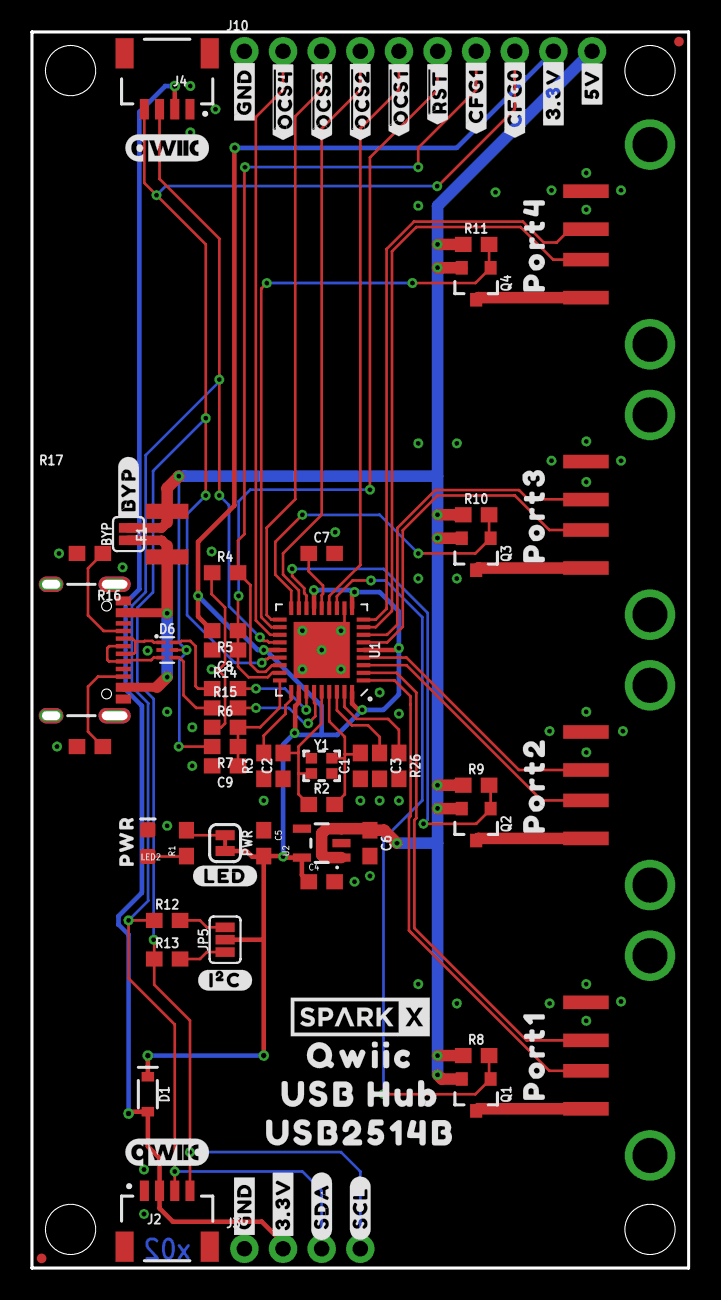
[picture p169: board Qwiic-USB_Hub.brd from above]

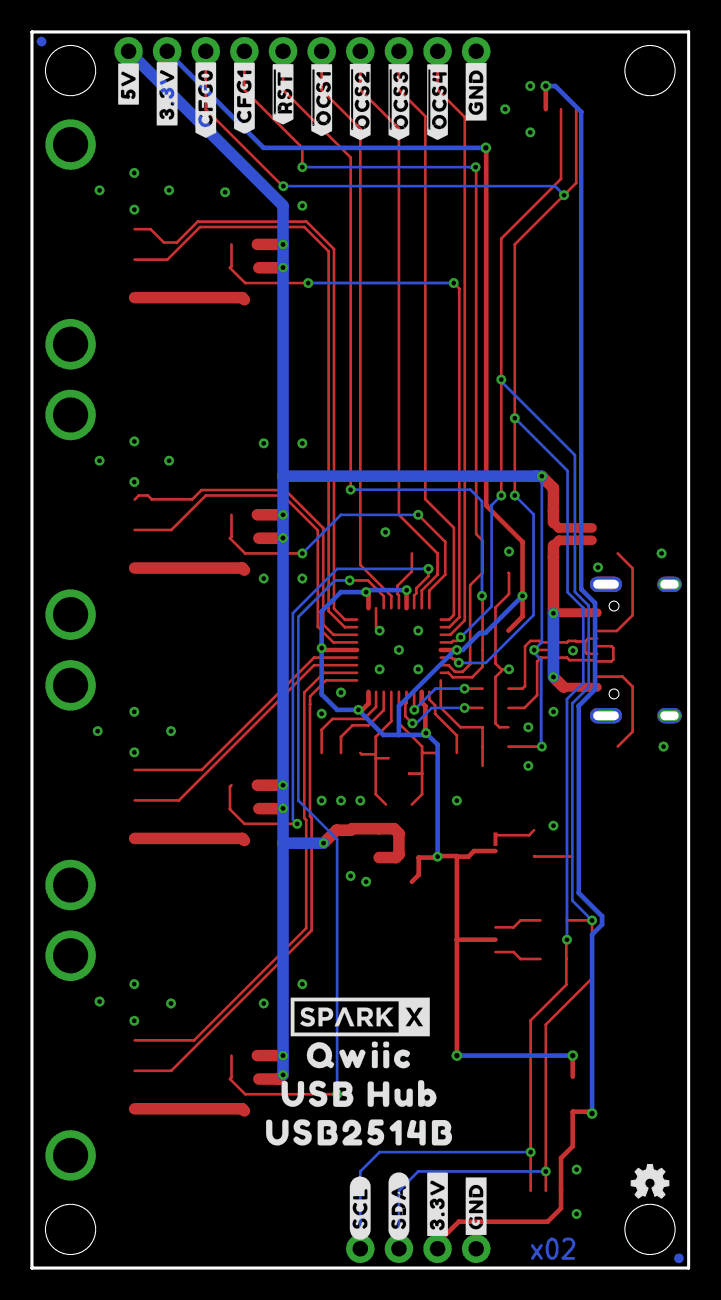
[picture p170: board Qwiic-USB_Hub.brd from below]

Board: 2 copper layers, 43.2 x 81.3 mm, 106 parts (21 on the bottom side), 48 nets.

Other parts of the board:
U$1: PORT40
U$2: PORT31
U$3: PORT22
U$4: PORT13
U$6, U$34: #3#3V#0
U$7, U$35: #SDA#0
U$8, U$36: #SCL#0
U$9, U$33: #GND#0
U$10: #I�C#1
U$11, U$16: #GND#5
U$12: PWR0
U$13, U$31: ##RST##4
U$14, U$32: #3#3V#6
U$15, U$37: #5V#7
U$17, U$30: ##OCS1##3
U$18, U$43: ##OCS2##2
U$19, U$44: ##OCS3##1
U$20, U$45: ##OCS4##0
U$21: #BYP#0
U$22, U$39: QWIIC2
U$23: #LED#0
U$24, U$29: #CFG0#1
U$25, U$28: #CFG1#0
U$26, U$41: USB2514B0
U$27, U$40: USB_HUB1
U$38: SPARKX-LOGO4; SPARKX-MEDIUM
U$42: QWIIC_5.5MM
