dekuNukem/USB4VC/resources/Qwiic_USB_Hub-USB2514B-main/Hardware/Production/Qwiic-USB_Hub-Panel.brd

## EAGLE design resources/Qwiic_USB_Hub-USB2514B-main/Hardware/Production/Qwiic-USB_Hub-Panel.brd (2021-11-04)

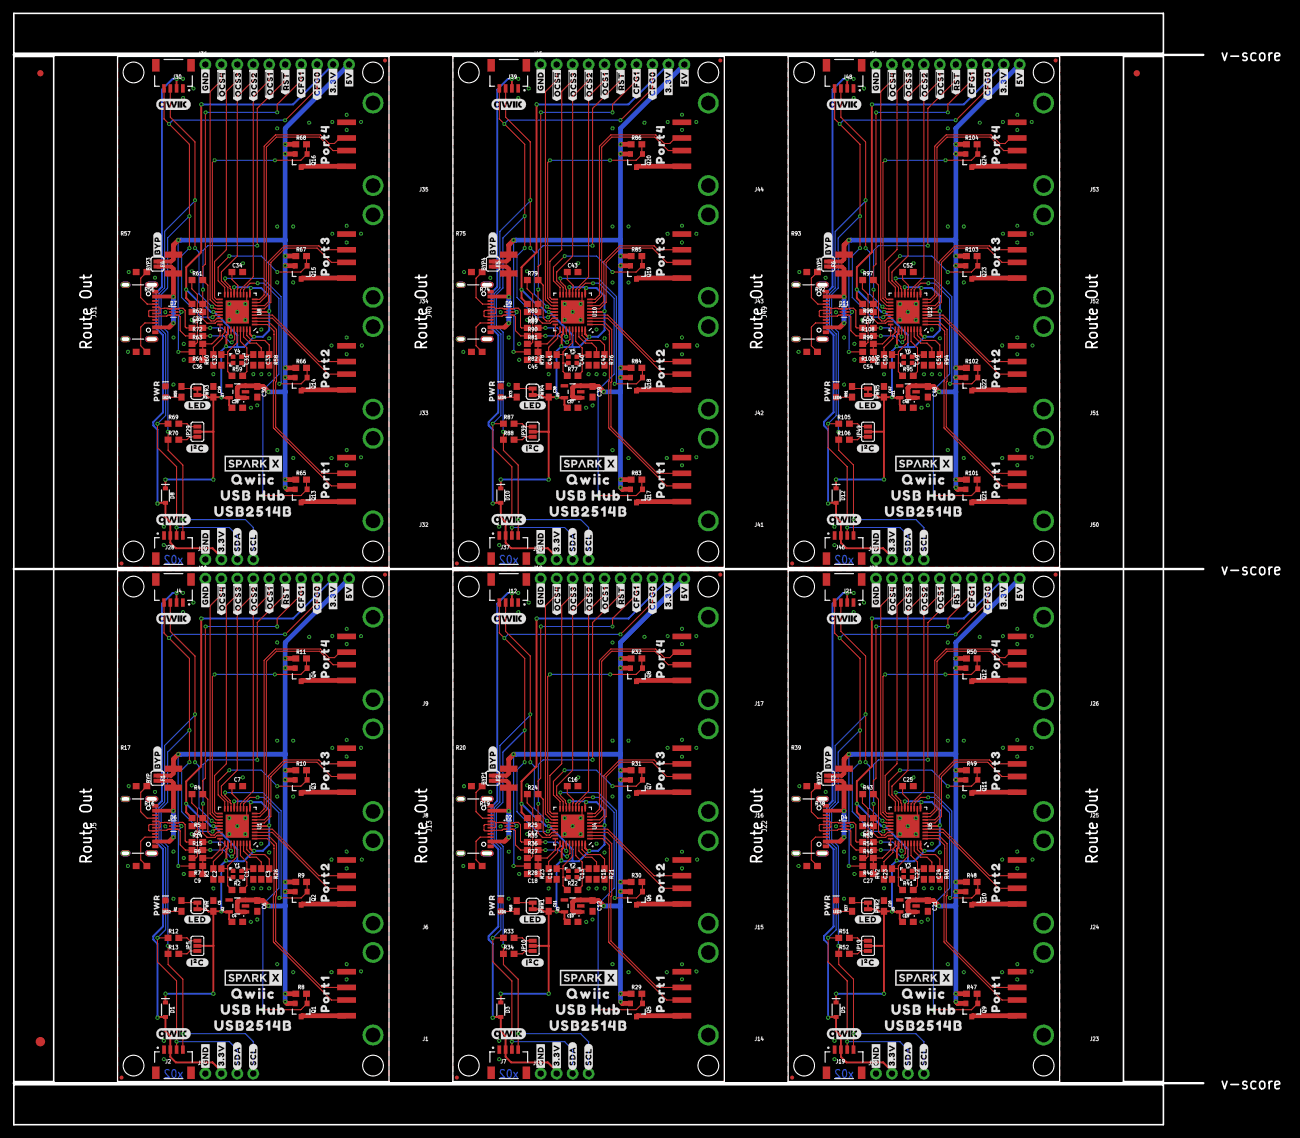
[picture p171: board Qwiic-USB_Hub-Panel.brd from above]

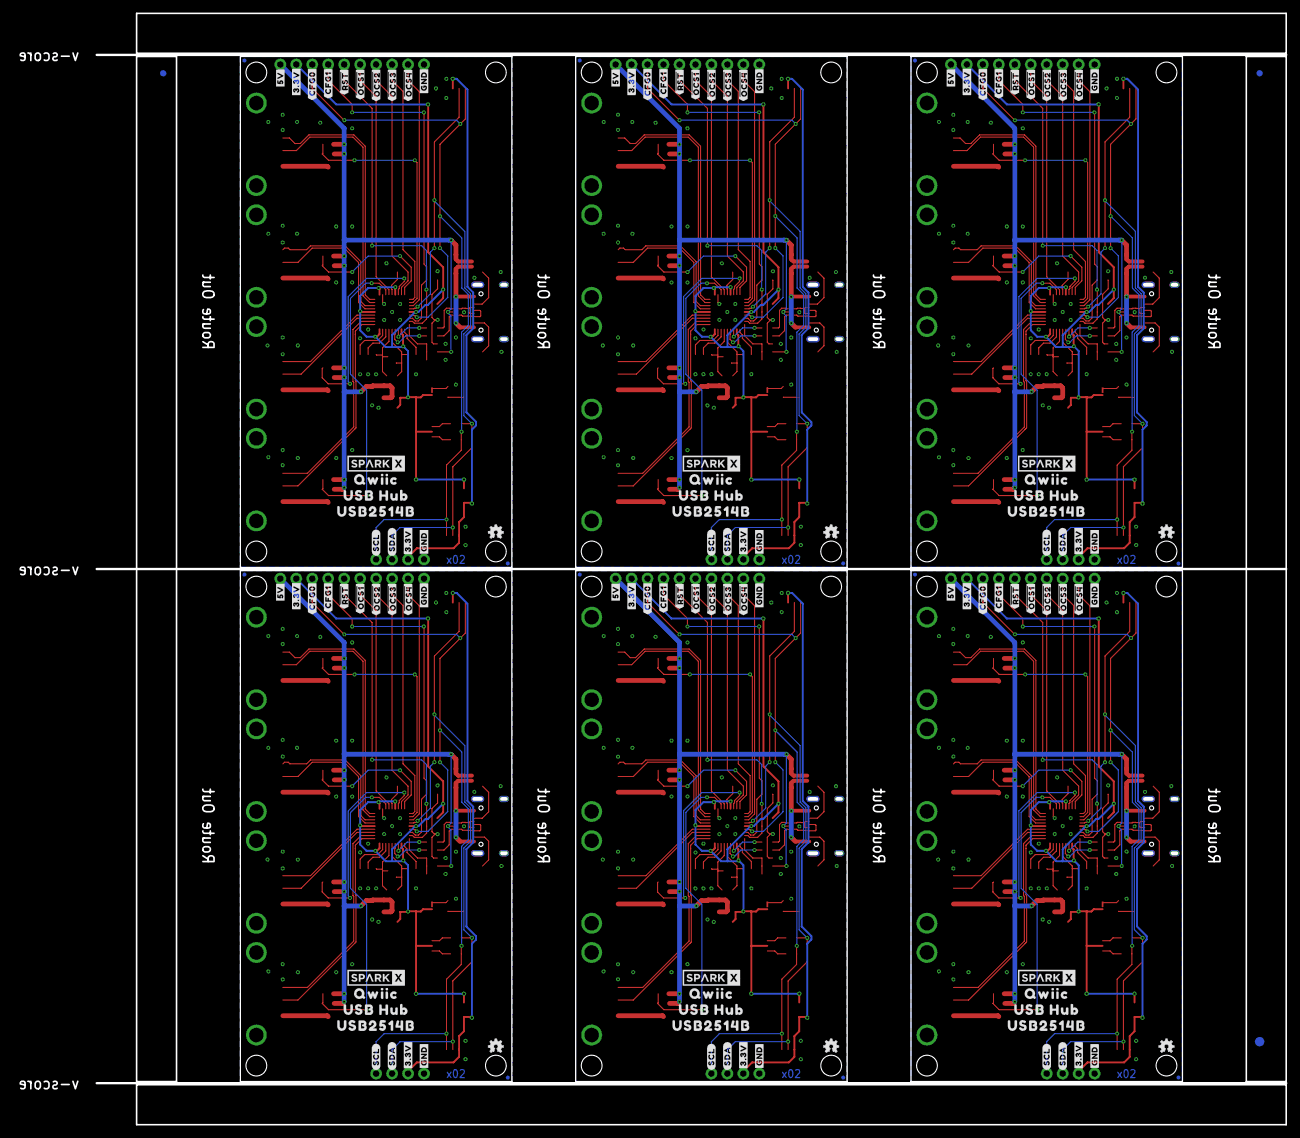
[picture p172: board Qwiic-USB_Hub-Panel.brd from below]

Board: 2 copper layers, 189.2 x 176.8 mm, 636 parts (129 on the bottom side), 288 nets.

Parts:
BYP, BYP1, BYP2, BYP3, BYP4, BYP5: JUMPER-SMT_2_NO_SILK; SMT-JUMPER_2_NO_SILK
C1, C2, C13, C14, C22, C23, C31, C32, C40, C41, C49, C50: 18pF; 0603
C3, C5, C7, C8, C9, C11, C15, C16, C17, C18, C20, C24, C25, C26, C27, C29, C33, C34, C35, C36, C38, C42, C43, C44, C45, C47, C51, C52, C53, C54: 0.1uF; 0603
C4, C6, C10, C12, C19, C21, C28, C30, C37, C39, C46, C48: 1.0uF; 0603
D1, D3, D5, D8, D10, D12: 3A/10V/280mV; SOD-323
D2, D4, D6, D7, D9, D11: PRTR5V0U2F; SOT886
E$1, E$2, E$3, E$4: FIDUCIAL-1X2
E$5, E$6: FIDUCIAL-1.5X3
F1, F2, F3, F4, F5, F6: 6V/2A; 1210
J1, J6, J8, J9, J14, J15, J16, J17, J23, J24, J25, J26, J32, J33, J34, J35, J41, J42, J43, J44, J50, J51, J52, J53: USB_A_FEMALE; USB-A-S-NOSILK-FEMALE
J2, J4, J7, J12, J19, J21, J28, J30, J37, J39, J46, J48: Qwiic Right Angle; JST04_1MM_RA
J3, J11, J20, J29, J38, J47: PTH; 1X04_NO_SILK
J5, J13, J22, J31, J40, J49: USB-C-16P-2LAYER-PADS
J10, J18, J27, J36, J45, J54: 1X10_NO_SILK
JP1, JP2, JP8, JP9, JP11, JP12, JP17, JP18, JP20, JP22, JP27, JP28, JP30, JP31, JP32, JP37, JP38, JP40, JP41, JP42, JP47, JP48, JP91, JP101: STAND-OFF
JP3, JP4, JP6, JP7, JP13, JP14, JP15, JP16, JP21, JP23, JP24, JP25, JP26, JP33, JP34, JP35, JP36, JP43, JP44, JP45, JP46, JP61, JP71, JP81: FIDUCIALUFIDUCIAL; MICRO-FIDUCIAL
JP5, JP10, JP19, JP29, JP39, JP49: SMT-JUMPER_3_NO_SILK
LED1, LED2, LED3, LED4, LED5, LED6: RED; LED-0603
LOGO1, LOGO3, LOGO5, LOGO7, LOGO9, LOGO11: OSHW-LOGOMINI; OSHW-LOGO-MINI
LOGO2, LOGO4, LOGO6, LOGO8, LOGO10, LOGO12: QWIIC_LOGO_CONNECTOR; QWIIC_5.5MM
PWR, PWR1, PWR2, PWR3, PWR4, PWR5: SMT-JUMPER_2_NC_TRACE_SILK
Q1, Q2, Q3, Q4, Q5, Q6, Q7, Q8, Q9, Q10, Q11, Q12, Q13, Q14, Q15, Q16, Q17, Q18, Q19, Q20, Q21, Q22, Q23, Q24: 4.3A/20V/54mΩ; SOT23-3
R1, R18, R37, R55, R73, R91: 1k; 0603
R2, R22, R41, R59, R77, R95: 1M; 0603
R3, R4, R5, R6, R7, R8, R9, R10, R11, R23, R24, R25, R27, R28, R29, R30, R31, R32, R42, R43, R44, R45, R46, R47, R48, R49, R50, R60, R61, R62, R63, R64, R65, R66, R67, R68, R78, R79, R80, R81, R82, R83, R84, R85, R86, R96, R97, R98, R99, R100, R101, R102, R103, R104: 100k; 0603
R12, R13, R33, R34, R51, R52, R69, R70, R87, R88, R105, R106: 2.2k; 0603
R14, R15, R35, R36, R53, R54, R71, R72, R89, R90, R107, R108: 22; 0603
R16, R17, R19, R20, R38, R39, R56, R57, R74, R75, R92, R93: 5.1k; 0603
R21, R26, R40, R58, R76, R94: 12k; 0603
U1, U4, U6, U8, U10, U12: USB251XB; QFN-36
U2, U3, U5, U7, U9, U11: 3.3V; SOT23-5
U$1, U$46, U$91, U$136, U$181, U$226: PORT40
U$2, U$47, U$92, U$137, U$182, U$227: PORT31
U$3, U$48, U$93, U$138, U$183, U$228: PORT22
U$4, U$49, U$94, U$139, U$184, U$229: PORT13
U$5, U$38, U$50, U$74, U$95, U$119, U$140, U$164, U$185, U$209, U$230, U$254: SPARKX-LOGO4; SPARKX-MEDIUM
U$6, U$34, U$51, U$54, U$96, U$99, U$141, U$144, U$186, U$189, U$231, U$234: #3#3V#0
U$7, U$35, U$52, U$55, U$97, U$100, U$142, U$145, U$187, U$190, U$232, U$235: #SDA#0
U$8, U$36, U$53, U$56, U$98, U$101, U$143, U$146, U$188, U$191, U$233, U$236: #SCL#0
U$9, U$33, U$57, U$58, U$102, U$103, U$147, U$148, U$192, U$193, U$237, U$238: #GND#0
U$10, U$59, U$104, U$149, U$194, U$239: #I�C#1
U$11, U$16, U$64, U$70, U$109, U$115, U$154, U$160, U$199, U$205, U$244, U$250: #GND#5
U$12, U$60, U$105, U$150, U$195, U$240: PWR0
U$13, U$31, U$61, U$71, U$106, U$116, U$151, U$161, U$196, U$206, U$241, U$251: ##RST##4
U$14, U$32, U$62, U$72, U$107, U$117, U$152, U$162, U$197, U$207, U$242, U$252: #3#3V#6
U$15, U$37, U$63, U$73, U$108, U$118, U$153, U$163, U$198, U$208, U$243, U$253: #5V#7
U$17, U$30, U$79, U$87, U$124, U$132, U$169, U$177, U$214, U$222, U$259, U$267: ##OCS1##3
U$18, U$43, U$80, U$88, U$125, U$133, U$170, U$178, U$215, U$223, U$260, U$268: ##OCS2##2
U$19, U$44, U$81, U$89, U$126, U$134, U$171, U$179, U$216, U$224, U$261, U$269: ##OCS3##1
U$20, U$45, U$82, U$90, U$127, U$135, U$172, U$180, U$217, U$225, U$262, U$270: ##OCS4##0
U$21, U$65, U$110, U$155, U$200, U$245: #BYP#0
U$22, U$39, U$67, U$75, U$112, U$120, U$157, U$165, U$202, U$210, U$247, U$255: QWIIC2
U$23, U$69, U$114, U$159, U$204, U$249: #LED#0
U$24, U$29, U$83, U$86, U$128, U$131, U$173, U$176, U$218, U$221, U$263, U$266: #CFG0#1
U$25, U$28, U$84, U$85, U$129, U$130, U$174, U$175, U$219, U$220, U$264, U$265: #CFG1#0
U$26, U$41, U$66, U$77, U$111, U$122, U$156, U$167, U$201, U$212, U$246, U$257: USB2514B0
U$27, U$40, U$68, U$76, U$113, U$121, U$158, U$166, U$203, U$211, U$248, U$256: USB_HUB1
U$42, U$78, U$123, U$168, U$213, U$258: QWIIC_5.5MM
Y1, Y2, Y3, Y4, Y5, Y6: 24MHz; CRYSTAL-SMD-2.0X1.6MM

Connections:
3.3V: C4.1, C5.2, D1.C, J10.9, JP5.2, PWR.2, R5.2, U1.5, U1.10, U1.15, U1.23, U1.29, U1.36, U2.5
3.3V1: C10.1, C11.2, D3.C, J18.9, JP10.2, PWR1.2, R25.2, U3.5, U4.5, U4.10, U4.15, U4.23, U4.29, U4.36
3.3V2: C19.1, C20.2, D5.C, J27.9, JP19.2, PWR2.2, R44.2, U5.5, U6.5, U6.10, U6.15, U6.23, U6.29, U6.36
3.3V3: C28.1, C29.2, D8.C, J36.9, JP29.2, PWR3.2, R62.2, U7.5, U8.5, U8.10, U8.15, U8.23, U8.29, U8.36
3.3V4: C37.1, C38.2, D10.C, J45.9, JP39.2, PWR4.2, R80.2, U9.5, U10.5, U10.10, U10.15, U10.23, U10.29, U10.36
3.3V5: C46.1, C47.2, D12.C, J54.9, JP49.2, PWR5.2, R98.2, U11.5, U12.5, U12.10, U12.15, U12.23, U12.29, U12.36
5V: BYP.2, C6.1, D6.5, F1.2, J10.10, Q1.2, Q2.2, Q3.2, Q4.2, R7.2, R8.1, R9.1, R10.1, R11.1, U2.1, U2.3
5V1: BYP1.2, C12.1, D2.5, F2.2, J18.10, Q5.2, Q6.2, Q7.2, Q8.2, R28.2, R29.1, R30.1, R31.1, R32.1, U3.1, U3.3
5V2: BYP2.2, C21.1, D4.5, F3.2, J27.10, Q9.2, Q10.2, Q11.2, Q12.2, R46.2, R47.1, R48.1, R49.1, R50.1, U5.1, U5.3
5V3: BYP3.2, C30.1, D7.5, F4.2, J36.10, Q13.2, Q14.2, Q15.2, Q16.2, R64.2, R65.1, R66.1, R67.1, R68.1, U7.1, U7.3
5V4: BYP4.2, C39.1, D9.5, F5.2, J45.10, Q17.2, Q18.2, Q19.2, Q20.2, R82.2, R83.1, R84.1, R85.1, R86.1, U9.1, U9.3
5V5: BYP5.2, C48.1, D11.5, F6.2, J54.10, Q21.2, Q22.2, Q23.2, Q24.2, R100.2, R101.1, R102.1, R103.1, R104.1, U11.1, U11.3
!OCS1: J10.5, U1.13
!OCS2: J10.4, U1.17
!OCS3: J10.3, U1.19
!OCS4: J10.2, U1.21
!OCS5: J18.5, U4.13
!OCS6: J18.4, U4.17
!OCS7: J18.3, U4.19
!OCS8: J18.2, U4.21
!OCS9: J27.5, U6.13
!OCS10: J27.4, U6.17
!OCS11: J27.3, U6.19
!OCS12: J27.2, U6.21
!OCS13: J36.5, U8.13
!OCS14: J36.4, U8.17
!OCS15: J36.3, U8.19
!OCS16: J36.2, U8.21
!OCS17: J45.5, U10.13
!OCS18: J45.4, U10.17
!OCS19: J45.3, U10.19
!OCS20: J45.2, U10.21
!OCS21: J54.5, U12.13
!OCS22: J54.4, U12.17
!OCS23: J54.3, U12.19
!OCS24: J54.2, U12.21
!RESET: C8.1, J10.6, R5.1, U1.26
!RESET1: C17.1, J18.6, R25.1, U4.26
!RESET2: C26.1, J27.6, R44.1, U6.26
!RESET3: C35.1, J36.6, R62.1, U8.26
!RESET4: C44.1, J45.6, R80.1, U10.26
!RESET5: C53.1, J54.6, R98.1, U12.26
CC1: J5.A5, R17.2
CC2: J5.B5, R16.2
CC3: J13.A5, R20.2
CC4: J13.B5, R19.2
CC5: J22.A5, R39.2
CC6: J22.B5, R38.2
CC7: J31.A5, R57.2
CC8: J31.B5, R56.2
CC9: J40.A5, R75.2
CC10: J40.B5, R74.2
CC11: J49.A5, R93.2
CC12: J49.B5, R92.2
CFG1: J10.7, R4.2, U1.25
CFG2: J18.7, R24.2, U4.25
CFG3: J27.7, R43.2, U6.25
CFG4: J36.7, R61.2, U8.25
CFG5: J45.7, R79.2, U10.25
CFG6: J54.7, R97.2, U12.25
D_N: D6.6, R14.1
D_N1: D2.6, R35.1
D_N2: D4.6, R53.1
D_N3: D7.6, R71.1
D_N4: D9.6, R89.1
D_N5: D11.6, R107.1
D_P: D6.4, R15.1
D_P1: D2.4, R36.1
D_P2: D4.4, R54.1
D_P3: D7.4, R72.1
D_P4: D9.4, R90.1
D_P5: D11.4, R108.1
GND: C1.1, C2.1, C3.2, C4.2, C5.1, C6.2, C7.2, C8.2, C9.2, D6.2, J1.GND, J2.1, J3.1, J4.1, J5.GND, J5.GND2, J5.SHLD1, J5.SHLD2, J5.SHLD3, J5.SHLD4, J6.GND, J8.GND, J9.GND, J10.1, LED2.C, R3.1, R4.1, R6.1, R16.1, R17.1, R26.2, U1.11, U1.EP, U2.2
GND1: C10.2, C11.1, C12.2, C13.1, C14.1, C15.2, C16.2, C17.2, C18.2, D2.2, J7.1, J11.1, J12.1, J13.GND, J13.GND2, J13.SHLD1, J13.SHLD2, J13.SHLD3, J13.SHLD4, J14.GND, J15.GND, J16.GND, J17.GND, J18.1, LED1.C, R19.1, R20.1, R21.2, R23.1, R24.1, R27.1, U3.2, U4.11, U4.EP
GND2: C19.2, C20.1, C21.2, C22.1, C23.1, C24.2, C25.2, C26.2, C27.2, D4.2, J19.1, J20.1, J21.1, J22.GND, J22.GND2, J22.SHLD1, J22.SHLD2, J22.SHLD3, J22.SHLD4, J23.GND, J24.GND, J25.GND, J26.GND, J27.1, LED3.C, R38.1, R39.1, R40.2, R42.1, R43.1, R45.1, U5.2, U6.11, U6.EP
GND3: C28.2, C29.1, C30.2, C31.1, C32.1, C33.2, C34.2, C35.2, C36.2, D7.2, J28.1, J29.1, J30.1, J31.GND, J31.GND2, J31.SHLD1, J31.SHLD2, J31.SHLD3, J31.SHLD4, J32.GND, J33.GND, J34.GND, J35.GND, J36.1, LED4.C, R56.1, R57.1, R58.2, R60.1, R61.1, R63.1, U7.2, U8.11, U8.EP
GND4: C37.2, C38.1, C39.2, C40.1, C41.1, C42.2, C43.2, C44.2, C45.2, D9.2, J37.1, J38.1, J39.1, J40.GND, J40.GND2, J40.SHLD1, J40.SHLD2, J40.SHLD3, J40.SHLD4, J41.GND, J42.GND, J43.GND, J44.GND, J45.1, LED5.C, R74.1, R75.1, R76.2, R78.1, R79.1, R81.1, U9.2, U10.11, U10.EP
GND5: C46.2, C47.1, C48.2, C49.1, C50.1, C51.2, C52.2, C53.2, C54.2, D11.2, J46.1, J47.1, J48.1, J49.GND, J49.GND2, J49.SHLD1, J49.SHLD2, J49.SHLD3, J49.SHLD4, J50.GND, J51.GND, J52.GND, J53.GND, J54.1, LED6.C, R92.1, R93.1, R94.2, R96.1, R97.1, R99.1, U11.2, U12.11, U12.EP
unnamed: J1.VBUS, Q1.3
unnamed: J6.VBUS, Q2.3
unnamed: J8.VBUS, Q3.3
unnamed: J9.VBUS, Q4.3
unnamed: R26.1, U1.35
unnamed: C1.2, R2.2, U1.33, Y1.3
unnamed: BYP.1, F1.1, J5.VBUS1, J5.VBUS2
unnamed: C2.2, R2.1, U1.32, Y1.1
unnamed: JP5.1, R13.2
unnamed: LED2.A, R1.1
unnamed: R3.2, U1.28
unnamed: LED1.A, R18.1
unnamed: C3.1, U1.34
unnamed: C7.1, U1.14
unnamed: JP5.3, R12.2
unnamed: R14.2, U1.30
unnamed: PWR.1, R1.2
unnamed: R15.2, U1.31
unnamed: PWR1.1, R18.2
unnamed: C13.2, R22.2, U4.33, Y2.3
unnamed: D1.A, J2.2, J3.2, J4.2
unnamed: C14.2, R22.1, U4.32, Y2.1
unnamed: R21.1, U4.35
unnamed: R23.2, U4.28
unnamed: C15.1, U4.34
unnamed: C16.1, U4.14
unnamed: J14.VBUS, Q5.3
unnamed: J15.VBUS, Q6.3
unnamed: J16.VBUS, Q7.3
unnamed: J17.VBUS, Q8.3
unnamed: BYP1.1, F2.1, J13.VBUS1, J13.VBUS2
unnamed: JP10.1, R34.2
unnamed: JP10.3, R33.2
unnamed: R35.2, U4.30
unnamed: R36.2, U4.31
unnamed: D3.A, J7.2, J11.2, J12.2
unnamed: LED3.A, R37.1
unnamed: PWR2.1, R37.2
unnamed: C22.2, R41.2, U6.33, Y3.3
unnamed: C23.2, R41.1, U6.32, Y3.1
unnamed: R40.1, U6.35
unnamed: R42.2, U6.28
unnamed: C24.1, U6.34
unnamed: C25.1, U6.14
unnamed: J23.VBUS, Q9.3
unnamed: J24.VBUS, Q10.3
unnamed: J25.VBUS, Q11.3
unnamed: J26.VBUS, Q12.3
unnamed: BYP2.1, F3.1, J22.VBUS1, J22.VBUS2
unnamed: JP19.1, R52.2
unnamed: JP19.3, R51.2
unnamed: R53.2, U6.30
unnamed: R54.2, U6.31
unnamed: D5.A, J19.2, J20.2, J21.2
unnamed: LED4.A, R55.1
unnamed: PWR3.1, R55.2
unnamed: C31.2, R59.2, U8.33, Y4.3
unnamed: C32.2, R59.1, U8.32, Y4.1
unnamed: R58.1, U8.35
unnamed: R60.2, U8.28
unnamed: C33.1, U8.34
unnamed: C34.1, U8.14
unnamed: J32.VBUS, Q13.3
unnamed: J33.VBUS, Q14.3
unnamed: J34.VBUS, Q15.3
unnamed: J35.VBUS, Q16.3
unnamed: BYP3.1, F4.1, J31.VBUS1, J31.VBUS2
unnamed: JP29.1, R70.2
unnamed: JP29.3, R69.2
unnamed: R71.2, U8.30
unnamed: R72.2, U8.31
unnamed: D8.A, J28.2, J29.2, J30.2
unnamed: LED5.A, R73.1
unnamed: PWR4.1, R73.2
unnamed: C40.2, R77.2, U10.33, Y5.3
unnamed: C41.2, R77.1, U10.32, Y5.1
unnamed: R76.1, U10.35
unnamed: R78.2, U10.28
unnamed: C42.1, U10.34
unnamed: C43.1, U10.14
unnamed: J41.VBUS, Q17.3
unnamed: J42.VBUS, Q18.3
unnamed: J43.VBUS, Q19.3
unnamed: J44.VBUS, Q20.3
unnamed: BYP4.1, F5.1, J40.VBUS1, J40.VBUS2
unnamed: JP39.1, R88.2
unnamed: JP39.3, R87.2
unnamed: R89.2, U10.30
unnamed: R90.2, U10.31
unnamed: D10.A, J37.2, J38.2, J39.2
unnamed: LED6.A, R91.1
unnamed: PWR5.1, R91.2
unnamed: C49.2, R95.2, U12.33, Y6.3
unnamed: C50.2, R95.1, U12.32, Y6.1
unnamed: R94.1, U12.35
unnamed: R96.2, U12.28
unnamed: C51.1, U12.34
unnamed: C52.1, U12.14
unnamed: J50.VBUS, Q21.3
unnamed: J51.VBUS, Q22.3
unnamed: J52.VBUS, Q23.3
unnamed: J53.VBUS, Q24.3
unnamed: BYP5.1, F6.1, J49.VBUS1, J49.VBUS2
unnamed: JP49.1, R106.2
unnamed: JP49.3, R105.2
unnamed: R107.2, U12.30
unnamed: R108.2, U12.31
unnamed: D12.A, J46.2, J47.2, J48.2
PORT1_N: J1.D-, U1.1
PORT1_N1: J14.D-, U4.1
PORT1_N2: J23.D-, U6.1
PORT1_N3: J32.D-, U8.1
PORT1_N4: J41.D-, U10.1
PORT1_N5: J50.D-, U12.1
PORT1_P: J1.D+, U1.2
PORT1_P1: J14.D+, U4.2
PORT1_P2: J23.D+, U6.2
PORT1_P3: J32.D+, U8.2
PORT1_P4: J41.D+, U10.2
PORT1_P5: J50.D+, U12.2
PORT2_N: J6.D-, U1.3
PORT2_N1: J15.D-, U4.3
PORT2_N2: J24.D-, U6.3
PORT2_N3: J33.D-, U8.3
PORT2_N4: J42.D-, U10.3
PORT2_N5: J51.D-, U12.3
PORT2_P: J6.D+, U1.4
PORT2_P1: J15.D+, U4.4
PORT2_P2: J24.D+, U6.4
PORT2_P3: J33.D+, U8.4
PORT2_P4: J42.D+, U10.4
PORT2_P5: J51.D+, U12.4
PORT3_N: J8.D-, U1.6
PORT3_N1: J16.D-, U4.6
PORT3_N2: J25.D-, U6.6
PORT3_N3: J34.D-, U8.6
PORT3_N4: J43.D-, U10.6
PORT3_N5: J52.D-, U12.6
PORT3_P: J8.D+, U1.7
PORT3_P1: J16.D+, U4.7
PORT3_P2: J25.D+, U6.7
PORT3_P3: J34.D+, U8.7
PORT3_P4: J43.D+, U10.7
PORT3_P5: J52.D+, U12.7
PORT4_N: J9.D-, U1.8
PORT4_N1: J17.D-, U4.8
PORT4_N2: J26.D-, U6.8
PORT4_N3: J35.D-, U8.8
PORT4_N4: J44.D-, U10.8
PORT4_N5: J53.D-, U12.8
PORT4_P: J9.D+, U1.9
PORT4_P1: J17.D+, U4.9
PORT4_P2: J26.D+, U6.9
PORT4_P3: J35.D+, U8.9
PORT4_P4: J44.D+, U10.9
PORT4_P5: J53.D+, U12.9
PRTPWR1: Q1.1, R8.2, U1.12
PRTPWR2: Q2.1, R9.2, U1.16
PRTPWR3: Q3.1, R10.2, U1.18
PRTPWR4: Q4.1, R11.2, U1.20
PRTPWR5: Q5.1, R29.2, U4.12
PRTPWR6: Q6.1, R30.2, U4.16
PRTPWR7: Q7.1, R31.2, U4.18
PRTPWR8: Q8.1, R32.2, U4.20
PRTPWR9: Q9.1, R47.2, U6.12
PRTPWR10: Q10.1, R48.2, U6.16
PRTPWR11: Q11.1, R49.2, U6.18
PRTPWR12: Q12.1, R50.2, U6.20
PRTPWR13: Q13.1, R65.2, U8.12
PRTPWR14: Q14.1, R66.2, U8.16
PRTPWR15: Q15.1, R67.2, U8.18
PRTPWR16: Q16.1, R68.2, U8.20
PRTPWR17: Q17.1, R83.2, U10.12
PRTPWR18: Q18.1, R84.2, U10.16
PRTPWR19: Q19.1, R85.2, U10.18
PRTPWR20: Q20.1, R86.2, U10.20
PRTPWR21: Q21.1, R101.2, U12.12
PRTPWR22: Q22.1, R102.2, U12.16
PRTPWR23: Q23.1, R103.2, U12.18
PRTPWR24: Q24.1, R104.2, U12.20
SCL/CFG0: J2.4, J3.4, J4.4, J10.8, R13.1, U1.24
SCL/CFG1: J7.4, J11.4, J12.4, J18.8, R34.1, U4.24
SCL/CFG2: J19.4, J20.4, J21.4, J27.8, R52.1, U6.24
SCL/CFG3: J28.4, J29.4, J30.4, J36.8, R70.1, U8.24
SCL/CFG4: J37.4, J38.4, J39.4, J45.8, R88.1, U10.24
SCL/CFG5: J46.4, J47.4, J48.4, J54.8, R106.1, U12.24
SDA: J2.3, J3.3, J4.3, R12.1, U1.22
SDA1: J7.3, J11.3, J12.3, R33.1, U4.22
SDA2: J19.3, J20.3, J21.3, R51.1, U6.22
SDA3: J28.3, J29.3, J30.3, R69.1, U8.22
SDA4: J37.3, J38.3, J39.3, R87.1, U10.22
SDA5: J46.3, J47.3, J48.3, R105.1, U12.22
UNP_D+: D6.3, J5.A6, J5.B6
UNP_D+1: D2.3, J13.A6, J13.B6
UNP_D+2: D4.3, J22.A6, J22.B6
UNP_D+3: D7.3, J31.A6, J31.B6
UNP_D+4: D9.3, J40.A6, J40.B6
UNP_D+5: D11.3, J49.A6, J49.B6
UNP_D-: D6.1, J5.A7, J5.B7
UNP_D-1: D2.1, J13.A7, J13.B7
UNP_D-2: D4.1, J22.A7, J22.B7
UNP_D-3: D7.1, J31.A7, J31.B7
UNP_D-4: D9.1, J40.A7, J40.B7
UNP_D-5: D11.1, J49.A7, J49.B7
VBUS_DET: C9.1, R6.2, R7.1, U1.27
VBUS_DET1: C18.1, R27.2, R28.1, U4.27
VBUS_DET2: C27.1, R45.2, R46.1, U6.27
VBUS_DET3: C36.1, R63.2, R64.1, U8.27
VBUS_DET4: C45.1, R81.2, R82.1, U10.27
VBUS_DET5: C54.1, R99.2, R100.1, U12.27
