dekuNukem/USB4VC/firmware/apple_lisa_mac_adb/Inc/quad_encoder.h

#ifndef __QUAD_ENCODER_H
#define __QUAD_ENCODER_H

#ifdef __cplusplus
 extern "C" {
#endif 

#include "stm32f0xx_hal.h"
#include "helpers.h"

#define AVG_BUF_SIZE 2
typedef struct
{
  GPIO_TypeDef* A_port;
  uint16_t A_pin;
  GPIO_TypeDef* B_port;
  uint16_t B_pin;
  uint8_t gray_code_index;
  int16_t avg_buf[AVG_BUF_SIZE];
  uint8_t avg_buf_index;
  int32_t avg_speed;
} quad_output;

void quad_init(mouse_buf* mbuf, TIM_HandleTypeDef* avg_tim, TIM_HandleTypeDef* arr_tim_x, TIM_HandleTypeDef* arr_tim_y, GPIO_TypeDef* x1_port, uint16_t x1_pin, GPIO_TypeDef* x2_port, uint16_t x2_pin, GPIO_TypeDef* y1_port, uint16_t y1_pin, GPIO_TypeDef* y2_port, uint16_t y2_pin);
void quad_increment(quad_output *qo);
void quad_decrement(quad_output *qo);
void quad_enable(void);
void quad_disable(void);

#ifdef __cplusplus
}
#endif

#endif
