dekuNukem/USB4VC/firmware/ibmpc/ibmpc.ioc

Mcu.UserName=STM32F072C8Tx
PA0.GPIO_Label=PCARD_BUSY
PA0.Signal=GPIO_Output
PA10.Signal=USART1_RX
PA13.Signal=SYS_SWDIO
PA14.Signal=SYS_SWCLK
PA15.GPIO_Label=ACT_LED
PA15.Signal=GPIO_Output
PA4.Signal=SPI1_NSS
PA5.Signal=SPI1_SCK
PA6.Signal=SPI1_MISO
PA7.Signal=SPI1_MOSI
PA8.GPIO_Label=KB_DETECT
PA8.Signal=GPIO_Input
PA9.Signal=USART1_TX
PB1.GPIO_Label=UART3_RTS
PB1.Signal=GPXTI1
PB10.Signal=USART3_TX
PB11.Signal=USART3_RX
PB13.Signal=I2C2_SCL
PB14.Signal=I2C2_SDA
PB15.GPIO_Label=MOUSE_DETECT
PB15.Signal=GPIO_Input
PB2.GPIO_Label=POT_RESET
PB2.Signal=GPIO_Output
PB3.GPIO_Label=ERR_LED
PB3.Signal=GPIO_Output
PB4.GPIO_Label=PS2MOUSE_DATA
PB4.Signal=GPIO_Output
PB5.GPIO_Label=PS2MOUSE_CLK
PB5.Signal=GPIO_Output
PB8.GPIO_Label=PS2KB_DATA
PB8.Signal=GPIO_Output
PB9.GPIO_Label=PS2KB_CLK
PB9.Signal=GPIO_Output
PC13.GPIO_Label=SLAVE_REQ
PC13.Signal=GPIO_Output
PC14-OSC32_IN.GPIO_Label=GAMEPAD_B4
PC14-OSC32_IN.Signal=GPIO_Output
PC15-OSC32_OUT.GPIO_Label=GAMEPAD_B2
PC15-OSC32_OUT.Signal=GPIO_Output
PF0-OSC_IN.GPIO_Label=GAMEPAD_B3
PF0-OSC_IN.Signal=GPIO_Output
PF1-OSC_OUT.GPIO_Label=GAMEPAD_B1
PF1-OSC_OUT.Signal=GPIO_Output
