dekuNukem/USB4VC/firmware/ibmpc/scrap.c

  if(ps2mouse_send_update(&my_ps2_outbuf) != PS2_OK)
  {
    // HAL_GPIO_WritePin(ERR_LED_GPIO_Port, ERR_LED_Pin, GPIO_PIN_SET);
    uint32_t enter_time = HAL_GetTick();
    while(ps2mouse_get_bus_status() != PS2_BUS_IDLE)
    {
      if(HAL_GetTick() - enter_time > 20)
        break;
    }
    // HAL_GPIO_WritePin(ERR_LED_GPIO_Port, ERR_LED_Pin, GPIO_PIN_RESET);
  }
  last_mouse_send = micros();
  // int i;
  // for (i = 0; i < 100; ++i)
  // {
  //   if(mouse_buf_peek(&my_mouse_buf) == NULL)
  //     break;
  //   mouse_buf_pop(&my_mouse_buf);
  // }
  // printf("%d", i);

  // mouse_event_reset(&consolidated_mouse_event);
  // mouse_buf_reset(&my_mouse_buf);
  consolidate_mouse_buf();


------

    uint8_t payload = 0x4D;
    mouse_uart_switch_to_8bit();
    HAL_UART_Transmit(&huart3, (unsigned char *)&payload, 1, 100);
    HAL_Delay(100);
    mouse_uart_switch_to_7bit();
    HAL_UART_Transmit(&huart3, (unsigned char *)&payload, 1, 100);
    HAL_Delay(100);
    HAL_GPIO_TogglePin(ERR_LED_GPIO_Port, ERR_LED_Pin);
    

void mouse_uart_switch_to_8bit(void)
{
  huart3.Init.WordLength = UART_WORDLENGTH_8B;
  printf("8 %d", HAL_UART_Init(&huart3));
}

void mouse_uart_switch_to_7bit(void)
{
  huart3.Init.WordLength = UART_WORDLENGTH_7B;
  // HAL_UART_Init(&huart3);
  printf("7 %d", HAL_UART_Init(&huart3));
}
while (1)
  {
    uint8_t payload = 0xaa;
    // mouse_uart_switch_to_8bit();
    HAL_UART_Transmit(&huart3, (unsigned char *)&payload, 1, 100);
    HAL_Delay(100);
    // mouse_uart_switch_to_7bit();
    // payload = 0xaa;
    // HAL_UART_Transmit(&huart3, (unsigned char *)&payload, 1, 100);
    // HAL_Delay(100);
    HAL_GPIO_TogglePin(ERR_LED_GPIO_Port, ERR_LED_Pin);

uint8_t is_ps2_mouse_connected_prev;

void ps2mouse_update(void)
{
  uint8_t is_ps2_mouse_connected = IS_PS2MOUSE_PRESENT();
  uint8_t send_bat = 0;
  if(is_ps2_mouse_connected == 1 && is_ps2_mouse_connected_prev == 0)
  {
    send_bat = 1;
    HAL_Delay(50);
    ps2mouse_restore_defaults();
  }
  is_ps2_mouse_connected_prev = is_ps2_mouse_connected;

  ps2mouse_bus_status = ps2mouse_get_bus_status();
  if(ps2mouse_bus_status == PS2_BUS_INHIBIT)
  {
    ps2mouse_release_lines();
    return;
  }
  else if(ps2mouse_bus_status == PS2_BUS_REQ_TO_SEND)
  {
    ps2mouse_read(&ps2mouse_host_cmd, 10);
    ps2mouse_host_req_reply(ps2mouse_host_cmd, &latest_mouse_event);
    return;
  }
  else if(send_bat)
  {
    ps2mouse_write(0xaa, 100);
    ps2mouse_write(0, 100);
  }


case 0xF7: // set all keys to typematic only, set 3 only
      if(ps2kb_current_scancode_set == 3)
        PS2KB_SENDACK();
      else
        ps2kb_write(0xFE, 1, PS2KB_WRITE_DEFAULT_TIMEOUT_MS);
      break;
uint8_t is_ps2_mouse_connected_prev;
 uint8_t is_ps2_mouse_connected = IS_PS2MOUSE_PRESENT();
  uint8_t send_bat = 0;
  if(is_ps2_mouse_connected == 1 && is_ps2_mouse_connected_prev == 0)
  {
    send_bat = 1;
    HAL_Delay(50);
    ps2mouse_restore_defaults();
  }
  is_ps2_mouse_connected_prev = is_ps2_mouse_connected;


if(ps2mouse_send_update(&my_ps2_outbuf) == PS2_ERROR_HOST_INHIBIT)
  {
    HAL_GPIO_WritePin(ERR_LED_GPIO_Port, ERR_LED_Pin, GPIO_PIN_SET);
    while(ps2mouse_get_bus_status() != PS2_BUS_IDLE)
      ;
    HAL_GPIO_WritePin(ERR_LED_GPIO_Port, ERR_LED_Pin, GPIO_PIN_RESET);
    while(1)
      ;
  }


if(ps2mouse_send_update(&my_ps2_outbuf) == PS2_ERROR_HOST_INHIBIT)
  {
    HAL_GPIO_WritePin(ERR_LED_GPIO_Port, ERR_LED_Pin, GPIO_PIN_SET);
    while(ps2mouse_get_bus_status() != PS2_BUS_IDLE)
      ;
    // HAL_GPIO_WritePin(ERR_LED_GPIO_Port, ERR_LED_Pin, GPIO_PIN_RESET);
    while(1)
      ;
  }

  while(1)
  {
    uint8_t send_result = ps2mouse_send_update(&my_ps2_outbuf);
    if(send_result == PS2_ERROR_HOST_INHIBIT)
    {
      HAL_GPIO_WritePin(ERR_LED_GPIO_Port, ERR_LED_Pin, GPIO_PIN_SET);
      while(ps2mouse_get_bus_status() != PS2_BUS_IDLE)
        ;
      HAL_GPIO_WritePin(ERR_LED_GPIO_Port, ERR_LED_Pin, GPIO_PIN_RESET);
      continue;
    }
    else
    {
      mouse_buf_pop(&my_mouse_buf);
      return;
    }
  }
  // uint8_t send_result = ps2mouse_send_update(&my_ps2_outbuf);
  // while(send_result == PS2_ERROR_HOST_INHIBIT)
  // {
  //   HAL_GPIO_WritePin(ERR_LED_GPIO_Port, ERR_LED_Pin, GPIO_PIN_SET);
  //   HAL_Delay(10);
  // }
  // mouse_buf_pop(&my_mouse_buf);

  while(1)
  {
    uint8_t send_result = ps2mouse_send_update(&my_ps2_outbuf);
    if(send_result == PS2_ERROR_HOST_INHIBIT)
    {
      HAL_GPIO_WritePin(ERR_LED_GPIO_Port, ERR_LED_Pin, GPIO_PIN_SET);
      HAL_Delay(1);
      HAL_GPIO_WritePin(ERR_LED_GPIO_Port, ERR_LED_Pin, GPIO_PIN_RESET);
      continue;
    }
    else
    {
      mouse_buf_pop(&my_mouse_buf);
      return;
    }
  }
  // only pop the item if sending is complete
  if(ps2mouse_send_update(&my_ps2_outbuf))
    HAL_Delay(1);
  else
    mouse_buf_pop(&my_mouse_buf);

void xtkb_update(void)
{
  xtkb_check_for_softreset();

  if(kb_buf_peek(&my_kb_buf, &buffered_code, &buffered_value) == 0)
  {
    if(xtkb_press_key(buffered_code, buffered_value) != 0)
    {
      xtkb_reset_bus();
      return;
    }
    kb_buf_pop(&my_kb_buf);
  }
}


uint8_t ps2_write_result = ps2kb_press_key(buffered_code, buffered_value);
    if(ps2_write_result)
      HAL_GPIO_WritePin(ERR_LED_GPIO_Port, ERR_LED_Pin, GPIO_PIN_SET);
    else
      kb_buf_pop(&my_kb_buf);
  printf("!%d", cmd);

  uint16_t idcode = (*(uint16_t*)(DBGMCU_IDCODE)) & 0x1fff;
  uint16_t flash_size = *(uint16_t*)(FLASH_SIZE_REG_ADDRESS);
  uint16_t* usb_reg = (uint16_t*)USB_CNTR;
  usb_reg = (uint16_t*)USB_CNTR;
  printf("idcode: 0x%x\n", idcode);
  printf("flash_size: %d\n", flash_size);
  printf("usb_before: 0x%x\n", *usb_reg);
  // *usb_reg = 0x2;
  // printf("usb_after: 0x%x\n", *usb_reg);

  //115200 195134

  1200 2032

  huart3.Init.BaudRate = 1200;
if(flash_size != 64)
  huart3.Init.BaudRate = 2032;

huart1.Init.BaudRate = 115200;
if(flash_size != 64)
  huart1.Init.BaudRate = 195134;

huart3.Init.WordLength = UART_WORDLENGTH_7B;


  for (int i = 0; i < 3; ++i)
    printf("0x%x ", serial_mouse_output_buf[i]);
  printf("\n");
  // printf("%d 0x%x 0x%x\n", serial_y, serial_mouse_output_buf[0], serial_mouse_output_buf[2]);
  // if(serial_y >= -1)
  //   serial_y = 0;
  // printf("%d\n", serial_y);
  // printf("%d 0x%x\n", serial_y, serial_y);
  uint8_t y_result = 0;
  if(serial_mouse_output_buf[0] & 0x8)
    y_result |= 0x80;
  if(serial_mouse_output_buf[0] & 0x4)
    y_result |= 0x40;
  y_result |= serial_mouse_output_buf[2] & 0x3f;
  printf("0x%x 0x%x\n", serial_y, y_result);

  for (int i = 0; i < SERIAL_MOUSE_BUF_SIZE; ++i)
    printf("0x%x ", serial_mouse_output_buf[i]);
  printf("\n");
    int8_t yyy = serial_mouse_output_buf[2] & 0x3f;
  yyy = yyy | ((serial_mouse_output_buf[0] & 0xc) << 4);
  printf("y %d\n", yyy);


    printf("%d %d\n", IS_KB_PRESENT(), IS_PS2MOUSE_PRESENT());
    HAL_Delay(500);

  printf("%d %d %d\n", index, protocol_status_lookup[index], onoff);
  GPIO_InitTypeDef GPIO_InitStruct;
  GPIO_InitStruct.Pin = data_pin;
  GPIO_InitStruct.Mode = GPIO_MODE_OUTPUT_PP;
  GPIO_InitStruct.Pull = GPIO_NOPULL;
  GPIO_InitStruct.Speed = GPIO_SPEED_FREQ_LOW;
  HAL_GPIO_Init(data_port, &GPIO_InitStruct);


printf("%d %d\n--\n", before & 0x80, after & 0x80);
  if(before == after)
    return;
  if((before & 0x7f) != (after & 0x7f))
    return;
  if((before & 0x80) > (after & 0x80)) // switching off
  {
    switch(after & 0x7f) 
    {
      case PROTOCOL_AT_PS2_KB:
        printf("PS2KB off\n");
        ps2kb_release_lines();
        ps2kb_reset();
        break;

      // case PROTOCOL_XT_KB:
      //  printf("XTKB off\n");
      //  break;

      case PROTOCOL_PS2_MOUSE:
        printf("PS2MOUSE off\n");
        ps2mouse_reset();
        ps2mouse_release_lines();
        break;

      // case PROTOCOL_MICROSOFT_SERIAL_MOUSE:
      //  printf("SERMOUSE off\n");
      //  break;

      // case PROTOCOL_GENERIC_GAMEPORT_GAMEPAD:
      //  printf("GGP off\n");
      //  release all buttons, reset digital pot to middle
      //  break;
    }
  }

uint8_t* find_in_array_7bit(uint8_t value, uint8_t* start, uint8_t* end)
{
  uint8_t* curr = start;
  while(curr <= end)
  {
    if(((*curr) & 0x7f) == (value & 0x7f))
      return curr;
    curr++;
  }
  return NULL;
}

#define SUPPORTED_PROTOCOL_SIZE 5
uint8_t protocol_status[SUPPORTED_PROTOCOL_SIZE] = 
{
  PROTOCOL_AT_PS2_KB | 0x80,
  PROTOCOL_XT_KB | 0x80,
  PROTOCOL_PS2_MOUSE | 0x80,
  PROTOCOL_MICROSOFT_SERIAL_MOUSE | 0x80,
  PROTOCOL_GENERIC_GAMEPORT_GAMEPAD | 0x80,
};
  // else // switching on
  // {
  //   switch(after & 0x7f) 
  //   {
  //     case PROTOCOL_AT_PS2_KB:
  //       printf("PS2KB on\n");
  //       break;

  //     case PROTOCOL_XT_KB:
  //       printf("XTKB on\n");
  //       break;

  //     case PROTOCOL_PS2_MOUSE:
  //       printf("PS2MOUSE on\n");
  //       break;

  //     case PROTOCOL_MICROSOFT_SERIAL_MOUSE:
  //       printf("SERMOUSE on\n");
  //       break;

  //     case PROTOCOL_GENERIC_GAMEPORT_GAMEPAD:
  //       printf("GGP on\n");
  //       break;
  //   }
  // }      
      // printf("mouse req: %d", ps2mouse_host_cmd);
uint8_t value = 32;
    uint8_t addr = ((value >> 8 & 0x01) | 0);
    value = (value & 0xFF);
    printf("w %d\n", HAL_I2C_Mem_Write(&hi2c2,MCP4451_I2C_ADDRESS,addr,1,&value,1,100));
    printf("%d\n--\n", after & 0x7f);

    printf("  f %d %d\n", ((*curr) & 0x7f), (value & 0x7f));
      printf("%d %d\n", i, backup_spi1_recv_buf[i]);
  printf("%d %d\n", before, after);
  printf("%d %d\n", before & 0x80, after & 0x80);

    // printf("0x%x\n", this_mouse_event->button_left);
    // printf("0x%x\n", this_mouse_event->button_right);
    // printf("0x%x\n", this_mouse_event->movement_x);
    // printf("0x%x\n", this_mouse_event->movement_y);
    // printf("out 0x%x\n", serial_mouse_output_buf[0]);
    // printf("out 0x%x\n", serial_mouse_output_buf[1]);
    // printf("out 0x%x\n", serial_mouse_output_buf[2]);
    // printf("-----\n");

  // printf("add before: %d %d\n", lb->tail, lb->head);
  // printf("add after: %d %d\n", lb->tail, lb->head);
      if(this_mouse_event->button == BTN_LEFT)
        mouse_status[MOUSE_LEFT] = this_mouse_event->button_state;
      else if(this_mouse_event->button == BTN_RIGHT)
        mouse_status[MOUSE_RIGHT] = this_mouse_event->button_state;
      else if(this_mouse_event->button == BTN_MIDDLE)
        mouse_status[MOUSE_MIDDLE] = this_mouse_event->button_state;
      for (int i = 0; i < MOUSE_BUTTONS_SIZE; ++i)
        printf("%d ", mouse_status[i]);
      printf("\n");
// printf("%d %d %d %d %d\n", this_event->movement_x, this_event->movement_y, this_event->scroll_vertical);
  // printf("%d %d %d %d %d\n-------\n\n", this_event->button_left, this_event->button_middle, this_event->button_right, this_event->button_side, this_event->button_extra);
  // printf("%d %d\n",this_event->movement_y, ps2mouse_out_buf[2]);
  // return 0;
      // for (int i = 0; i < SAMPLE_RATE_HISTORY_BUF_SIZE; ++i)
      //   printf("%d ", sample_rate_history[i]);
      // printf("\n");
        sample_rate_history_index = (sample_rate_history_index + 1) % SAMPLE_RATE_HISTORY_BUF_SIZE;
uint8_t get_prev(uint8_t index, uint8_t size)
{
  return (index + size - 1) % size;
}

      last = get_prev(sample_rate_history_index, SAMPLE_RATE_HISTORY_BUF_SIZE);
      second_last = get_prev(last, SAMPLE_RATE_HISTORY_BUF_SIZE);
      third_last = get_prev(second_last, SAMPLE_RATE_HISTORY_BUF_SIZE);
void HAL_SPI_TxRxCpltCallback(SPI_HandleTypeDef *hspi)
{
 //  HAL_GPIO_WritePin(DEBUG_GPIO_Port, DEBUG_Pin, GPIO_PIN_SET);
  HAL_SPI_TransmitReceive_IT(&hspi1, spi_transmit_buf, spi_recv_buf, SPI_BUF_SIZE);
  // HAL_GPIO_WritePin(DEBUG_GPIO_Port, DEBUG_Pin, GPIO_PIN_RESET);

  if(spi_recv_buf[0] != 0xde)
    HAL_GPIO_WritePin(ERROR_GPIO_Port, ERROR_Pin, GPIO_PIN_SET);
  else
    HAL_GPIO_WritePin(ERROR_GPIO_Port, ERROR_Pin, GPIO_PIN_RESET);
}


    if(spi_recv_buf[SPI_BUF_INDEX_MAGIC] != SPI_MAGIC_NUM)
    {
      printf("unknown command!\n");
      goto parse_end;
    }
// event_type = backup_spi1_recv_buf[4];
    // event_code = backup_spi1_recv_buf[6];
    // event_value = backup_spi1_recv_buf[8];
    // for (int i = 0; i < SPI_BUF_SIZE; ++i)
    //     printf("0x%02x ", backup_spi1_recv_buf[i]);
    // printf("\n\n");

  // if(HAL_GPIO_ReadPin(GPIOA, GPIO_PIN_4) == GPIO_PIN_SET)
  //   HAL_SPI_Receive_DMA(&hspi1, spi_recv_buf, SPI_BUF_SIZE);
      // printf("ps2kb_leds: %d\n", ps2kb_leds);
    // printf("0x%02x\n", ps2kb_host_cmd);

memset(spi_transmit_buf, 0, SPI_BUF_SIZE);
      HAL_GPIO_WritePin(SLAVE_REQ_GPIO_Port, SLAVE_REQ_Pin, GPIO_PIN_RESET);
printf("\n---ps2kb_buf_get---\n%d %d\n", my_ps2kb_buf.tail, my_ps2kb_buf.head);
    printf("%d %d---\n", buffered_code, buffered_value);

void HAL_SPI_RxCpltCallback(SPI_HandleTypeDef *hspi)
{
  for (int i = 0; i < SPI_BUF_SIZE; ++i)
      printf("0x%02x ", spi_recv_buf[i]);
  printf("\n");

  if(spi_recv_buf[SPI_BUF_INDEX_MAGIC] != SPI_MAGIC_NUM)
    goto parse_end;

  if(spi_recv_buf[SPI_BUF_INDEX_MSG_TYPE] == SPI_MSG_KB_EVENT)
  {
    // event_type = spi_recv_buf[4];
    // event_code = spi_recv_buf[6];
    // event_value = spi_recv_buf[8];
    ps2kb_buf_add(&my_ps2kb_buf, spi_recv_buf[6], spi_recv_buf[8]);
  }

  spi_data_available = 1;

  parse_end:
  HAL_SPI_Receive_DMA(&hspi1, spi_recv_buf, SPI_BUF_SIZE);
}
if(spi_recv_buf[SPI_BUF_INDEX_MSG_TYPE] == SPI_MSG_KB_EVENT)
  {
    event_type = spi_recv_buf[4];
    event_code = spi_recv_buf[6];
    event_value = spi_recv_buf[8];
    // printf("%02d %d\n", event_code, event_value);
    ps2kb_press_key(event_code, event_value);
  }


printf("waiting for host request...\n");
  // wait for data line to go low and clock line to go high (request to send)
  while(!(PS2KB_READ_DATA_PIN() == GPIO_PIN_RESET && PS2KB_READ_CLK_PIN() == GPIO_PIN_SET))
    ;
  printf("host request!\n");
  // return 0;  


  // if(HAL_GPIO_ReadPin(GPIOA, GPIO_PIN_4) == GPIO_PIN_SET)
  //   HAL_SPI_Receive_DMA(&hspi1, spi_recv_buf, SPI_BUF_SIZE);
    if(HAL_GPIO_ReadPin(GPIOA, GPIO_PIN_4) == GPIO_PIN_RESET)
      printf("hh\n");
    // printf("%d\n", HAL_GPIO_ReadPin(GPIOA, GPIO_PIN_4));
    // HAL_Delay(200);

  // printf("got!\n");
  HAL_GPIO_TogglePin(GPIOA, GPIO_PIN_1);

#define PS2_BUS_IDLE 0
#define PS2_BUS_INHIBIT 1
#define PS2_BUS_REQ_TO_SEND 2
#define PS2_BUS_UNKNOWN 3

uint8_t get_bus_status()
{

}


// HAS PARAITY CHECK


uint8_t ps2kb_read(uint8_t* result)
{
  uint16_t data = 0x00;
  uint16_t bit = 0x01;

  uint8_t calculated_parity = 1;
  uint8_t received_parity = 0;

  printf("waiting for host request...\n");
  // wait for data line to go low and clock line to go high (request to send)
  while(!(PS2KB_READ_DATA_PIN() == GPIO_PIN_RESET && PS2KB_READ_CLK_PIN() == GPIO_PIN_SET))
    ;
  printf("host request!\n");
  // return 0;

  delay_us(CLKHALF);
  PS2KB_CLK_LOW();
  delay_us(CLKFULL);
  PS2KB_CLK_HI();
  delay_us(CLKHALF);

  while (bit < 0x0100)
  {
    if (PS2KB_READ_DATA_PIN() == GPIO_PIN_SET)
    {
      data = data | bit;
      calculated_parity = calculated_parity ^ 1;
    } 
    else
    {
      calculated_parity = calculated_parity ^ 0;
    }
    bit = bit << 1;
    delay_us(CLKHALF);
    PS2KB_CLK_LOW();
    delay_us(CLKFULL);
    PS2KB_CLK_HI();
    delay_us(CLKHALF);
  }
  // we do the delay at the end of the loop, so at this point we have
  // already done the delay for the parity bit

  // parity bit
  if (PS2KB_READ_DATA_PIN() == GPIO_PIN_SET)
    received_parity = 1;

  // stop bit
  delay_us(CLKHALF);
  PS2KB_CLK_LOW();
  delay_us(CLKFULL);
  PS2KB_CLK_HI();
  delay_us(CLKHALF);

  delay_us(CLKHALF);
  PS2KB_DATA_LOW();
  PS2KB_CLK_LOW();
  delay_us(CLKFULL);
  PS2KB_CLK_HI();
  delay_us(CLKHALF);
  PS2KB_DATA_HI();

  *result = data & 0x00FF;
  printf("0x%02x\n", *result);
  return 0;

}
