dekuNukem/USB4VC/firmware/ibmpc/Inc/helpers.h

#ifndef __HELPERS_H
#define __HELPERS_H

#ifdef __cplusplus
 extern "C" {
#endif 

#include "stm32f0xx_hal.h"

#define SPI_BUF_SIZE 32

#define SPI_MOSI_MAGIC 0xde
#define SPI_MISO_MAGIC 0xcd

#define SPI_BUF_INDEX_MAGIC 0
#define SPI_BUF_INDEX_SEQNUM 1
#define SPI_BUF_INDEX_MSG_TYPE 2

#define SPI_MOSI_MSG_TYPE_NOP 0
#define SPI_MOSI_MSG_TYPE_INFO_REQUEST 1
#define SPI_MOSI_MSG_TYPE_SET_PROTOCOL 2
#define SPI_MOSI_MSG_TYPE_REQ_ACK 3

#define SPI_MOSI_MSG_TYPE_KEYBOARD_EVENT 8
#define SPI_MOSI_MSG_TYPE_MOUSE_EVENT 9
#define SPI_MOSI_MSG_TYPE_GAMEPAD_EVENT_RAW 10
#define SPI_MOSI_MSG_TYPE_GAMEPAD_EVENT_MAPPED_IBMPC 11

#define SPI_MISO_MSG_TYPE_NOP 0
#define SPI_MISO_MSG_TYPE_INFO_REQUEST 128
#define SPI_MISO_MSG_TYPE_KB_LED_REQUEST 129

#define BTN_LEFT    0x110
#define BTN_RIGHT   0x111
#define BTN_MIDDLE    0x112
#define BTN_SIDE    0x113
#define BTN_EXTRA   0x114

#define PROTOCOL_AT_PS2_KB 1
#define PROTOCOL_XT_KB 2
#define PROTOCOL_ADB_KB 3
#define PROTOCOL_PS2_MOUSE 4
#define PROTOCOL_MICROSOFT_SERIAL_MOUSE 5
#define PROTOCOL_ADB_MOUSE 6
#define PROTOCOL_GENERIC_GAMEPORT_GAMEPAD 7
#define PROTOCOL_MOUSESYSTEMS_SERIAL_MOUSE 8

#define MOUSE_EVENT_BUFFER_SIZE 16
#define KEYBOARD_EVENT_BUFFER_SIZE 8
#define GAMEPAD_EVENT_BUFFER_SIZE 8

typedef struct
{
  uint8_t head;
  uint8_t tail;
  uint8_t* keycode_buf;
  uint8_t* keyvalue_buf;
} kb_buf;

typedef struct
{
  int32_t movement_x;
  int32_t movement_y;
  int8_t scroll_vertical;
  int8_t scroll_horizontal;
  uint8_t button_left;
  uint8_t button_middle;
  uint8_t button_right;
  uint8_t button_side;
  uint8_t button_extra;
} mouse_event;

typedef struct
{
  uint8_t head;
  uint8_t tail;
  mouse_event* mouse_events;
} mouse_buf;

typedef struct
{
  uint8_t button_1;
  uint8_t button_2;
  uint8_t button_3;
  uint8_t button_4;
  uint8_t button_lt;
  uint8_t button_rt;
  uint8_t button_lt2;
  uint8_t button_rt2;
  uint8_t axis_x;
  uint8_t axis_y;
  uint8_t axis_rx;
  uint8_t axis_ry;
} gamepad_event;

typedef struct
{
  uint8_t head;
  uint8_t tail;
  gamepad_event* gamepad_events;
} gamepad_buf;


#define PS2_OUT_BUF_MAXSIZE 8

typedef struct
{
  uint8_t size;
  uint8_t data[PS2_OUT_BUF_MAXSIZE];
} ps2_outgoing_buf;

void kb_buf_init(kb_buf *lb);
uint8_t kb_buf_add(kb_buf *lb, uint8_t code, uint8_t value);
uint8_t kb_buf_peek(kb_buf *lb, uint8_t* code, uint8_t* value);
void kb_buf_pop(kb_buf *lb);

void mouse_buf_init(mouse_buf *lb);
uint8_t mouse_buf_add(mouse_buf *lb, mouse_event* event);
mouse_event* mouse_buf_peek(mouse_buf *lb);
void mouse_buf_pop(mouse_buf *lb);
void mouse_buf_reset(mouse_buf *lb);
void mouse_event_reset(mouse_event* event);

void gamepad_buf_init(gamepad_buf *lb);
uint8_t gamepad_buf_add(gamepad_buf *lb, gamepad_event* event);
gamepad_event* gamepad_buf_peek(gamepad_buf *lb);
void gamepad_buf_pop(gamepad_buf *lb);

#define PCARD_BUSY_HI() HAL_GPIO_WritePin(PCARD_BUSY_GPIO_Port, PCARD_BUSY_Pin, GPIO_PIN_SET)
#define PCARD_BUSY_LOW() HAL_GPIO_WritePin(PCARD_BUSY_GPIO_Port, PCARD_BUSY_Pin, GPIO_PIN_RESET)

#ifdef __cplusplus
}
#endif

#endif
