dekuNukem/USB4VC/resources/oldcode/make_scancode_lookup.py

linux_ev_name_to_code_lookup = {
	'KEY_RESERVED':0,
	'KEY_ESC':1,
	'KEY_1':2,
	'KEY_2':3,
	'KEY_3':4,
	'KEY_4':5,
	'KEY_5':6,
	'KEY_6':7,
	'KEY_7':8,
	'KEY_8':9,
	'KEY_9':10,
	'KEY_0':11,
	'KEY_MINUS':12,
	'KEY_EQUAL':13,
	'KEY_BACKSPACE':14,
	'KEY_TAB':15,
	'KEY_Q':16,
	'KEY_W':17,
	'KEY_E':18,
	'KEY_R':19,
	'KEY_T':20,
	'KEY_Y':21,
	'KEY_U':22,
	'KEY_I':23,
	'KEY_O':24,
	'KEY_P':25,
	'KEY_LEFTBRACE':26,
	'KEY_RIGHTBRACE':27,
	'KEY_ENTER':28,
	'KEY_LEFTCTRL':29,
	'KEY_A':30,
	'KEY_S':31,
	'KEY_D':32,
	'KEY_F':33,
	'KEY_G':34,
	'KEY_H':35,
	'KEY_J':36,
	'KEY_K':37,
	'KEY_L':38,
	'KEY_SEMICOLON':39,
	'KEY_APOSTROPHE':40,
	'KEY_GRAVE':41,
	'KEY_LEFTSHIFT':42,
	'KEY_BACKSLASH':43,
	'KEY_Z':44,
	'KEY_X':45,
	'KEY_C':46,
	'KEY_V':47,
	'KEY_B':48,
	'KEY_N':49,
	'KEY_M':50,
	'KEY_COMMA':51,
	'KEY_DOT':52,
	'KEY_SLASH':53,
	'KEY_RIGHTSHIFT':54,
	'KEY_KPASTERISK':55,
	'KEY_LEFTALT':56,
	'KEY_SPACE':57,
	'KEY_CAPSLOCK':58,
	'KEY_F1':59,
	'KEY_F2':60,
	'KEY_F3':61,
	'KEY_F4':62,
	'KEY_F5':63,
	'KEY_F6':64,
	'KEY_F7':65,
	'KEY_F8':66,
	'KEY_F9':67,
	'KEY_F10':68,
	'KEY_NUMLOCK':69,
	'KEY_SCROLLLOCK':70,
	'KEY_KP7':71,
	'KEY_KP8':72,
	'KEY_KP9':73,
	'KEY_KPMINUS':74,
	'KEY_KP4':75,
	'KEY_KP5':76,
	'KEY_KP6':77,
	'KEY_KPPLUS':78,
	'KEY_KP1':79,
	'KEY_KP2':80,
	'KEY_KP3':81,
	'KEY_KP0':82,
	'KEY_KPDOT':83,
	'KEY_ZENKAKUHANKAKU':85,
	'KEY_102ND':86,
	'KEY_F11':87,
	'KEY_F12':88,
	'KEY_RO':89,
	'KEY_KATAKANA':90,
	'KEY_HIRAGANA':91,
	'KEY_HENKAN':92,
	'KEY_KATAKANAHIRAGANA':93,
	'KEY_MUHENKAN':94,
	'KEY_KPJPCOMMA':95,
	'KEY_KPENTER':96,
	'KEY_RIGHTCTRL':97,
	'KEY_KPSLASH':98,
	'KEY_SYSRQ':99,
	'KEY_RIGHTALT':100,
	'KEY_LINEFEED':101,
	'KEY_HOME':102,
	'KEY_UP':103,
	'KEY_PAGEUP':104,
	'KEY_LEFT':105,
	'KEY_RIGHT':106,
	'KEY_END':107,
	'KEY_DOWN':108,
	'KEY_PAGEDOWN':109,
	'KEY_INSERT':110,
	'KEY_DELETE':111,
	'KEY_MACRO':112,
	'KEY_MUTE':113,
	'KEY_VOLUMEDOWN':114,
	'KEY_VOLUMEUP':115,
	'KEY_POWER':116,
	'KEY_KPEQUAL':117,
	'KEY_KPPLUSMINUS':118,
	'KEY_PAUSE':119,
	'KEY_SCALE':120,
	'KEY_KPCOMMA':121,
	'KEY_HANGEUL':122,
	'KEY_HANJA':123,
	'KEY_YEN':124,
	'KEY_LEFTMETA':125,
	'KEY_RIGHTMETA':126,
	'KEY_COMPOSE':127,
	'KEY_STOP':128,
	'KEY_AGAIN':129,
	'KEY_PROPS':130,
	'KEY_UNDO':131,
	'KEY_FRONT':132,
	'KEY_COPY':133,
	'KEY_OPEN':134,
	'KEY_PASTE':135,
	'KEY_FIND':136,
	'KEY_CUT':137,
	'KEY_HELP':138,
	'KEY_MENU':139,
	'KEY_CALC':140,
	'KEY_SETUP':141,
	'KEY_SLEEP':142,
	'KEY_WAKEUP':143,
	'KEY_FILE':144,
	'KEY_SENDFILE':145,
	'KEY_DELETEFILE':146,
	'KEY_XFER':147,
	'KEY_PROG1':148,
	'KEY_PROG2':149,
	'KEY_WWW':150,
	'KEY_MSDOS':151,
	'KEY_COFFEE':152,
	'KEY_ROTATE_DISPLAY':153,
	'KEY_CYCLEWINDOWS':154,
	'KEY_MAIL':155,
	'KEY_BOOKMARKS':156,
	'KEY_COMPUTER':157,
	'KEY_BACK':158,
	'KEY_FORWARD':159,
	'KEY_CLOSECD':160,
	'KEY_EJECTCD':161,
	'KEY_EJECTCLOSECD':162,
	'KEY_NEXTSONG':163,
	'KEY_PLAYPAUSE':164,
	'KEY_PREVIOUSSONG':165,
	'KEY_STOPCD':166,
	'KEY_RECORD':167,
	'KEY_REWIND':168,
	'KEY_PHONE':169,
	'KEY_ISO':170,
	'KEY_CONFIG':171,
	'KEY_HOMEPAGE':172,
	'KEY_REFRESH':173,
	'KEY_EXIT':174,
	'KEY_MOVE':175,
	'KEY_EDIT':176,
	'KEY_SCROLLUP':177,
	'KEY_SCROLLDOWN':178,
	'KEY_KPLEFTPAREN':179,
	'KEY_KPRIGHTPAREN':180,
	'KEY_NEW':181,
	'KEY_REDO':182,
	'KEY_F13':183,
	'KEY_F14':184,
	'KEY_F15':185,
	'KEY_F16':186,
	'KEY_F17':187,
	'KEY_F18':188,
	'KEY_F19':189,
	'KEY_F20':190,
	'KEY_F21':191,
	'KEY_F22':192,
	'KEY_F23':193,
	'KEY_F24':194,
	'KEY_PLAYCD':200,
	'KEY_PAUSECD':201,
	'KEY_PROG3':202,
	'KEY_PROG4':203,
	'KEY_ALL_APPLICATIONS':204,
	'KEY_SUSPEND':205,
	'KEY_CLOSE':206,
	'KEY_PLAY':207,
	'KEY_FASTFORWARD':208,
	'KEY_BASSBOOST':209,
	'KEY_PRINT':210,
	'KEY_HP':211,
	'KEY_CAMERA':212,
	'KEY_SOUND':213,
	'KEY_QUESTION':214,
	'KEY_EMAIL':215,
	'KEY_CHAT':216,
	'KEY_SEARCH':217,
	'KEY_CONNECT':218,
	'KEY_FINANCE':219,
	'KEY_SPORT':220,
	'KEY_SHOP':221,
	'KEY_ALTERASE':222,
	'KEY_CANCEL':223,
	'KEY_BRIGHTNESSDOWN':224,
	'KEY_BRIGHTNESSUP':225,
	'KEY_MEDIA':226,
	'KEY_SWITCHVIDEOMODE':227,
	'KEY_KBDILLUMTOGGLE':228,
	'KEY_KBDILLUMDOWN':229,
	'KEY_KBDILLUMUP':230,
	'KEY_SEND':231,
	'KEY_REPLY':232,
	'KEY_FORWARDMAIL':233,
	'KEY_SAVE':234,
	'KEY_DOCUMENTS':235,
	'KEY_BATTERY':236,
	'KEY_BLUETOOTH':237,
	'KEY_WLAN':238,
	'KEY_UWB':239,
	'KEY_UNKNOWN':240,
	'KEY_VIDEO_NEXT':241,
	'KEY_VIDEO_PREV':242,
	'KEY_BRIGHTNESS_CYCLE':243,
	'KEY_BRIGHTNESS_AUTO':244,
	'KEY_DISPLAY_OFF':245,
	'KEY_WWAN':246,
	'KEY_RFKILL':247,
	'KEY_MICMUTE':248,
	'KEY_OK':0x160,
	'KEY_SELECT':0x161,
	'KEY_GOTO':0x162,
	'KEY_CLEAR':0x163,
	'KEY_POWER2':0x164,
	'KEY_OPTION':0x165,
	'KEY_INFO':0x166,
	'KEY_TIME':0x167,
	'KEY_VENDOR':0x168,
	'KEY_ARCHIVE':0x169,
	'KEY_PROGRAM':0x16a,
	'KEY_CHANNEL':0x16b,
	'KEY_FAVORITES':0x16c,
	'KEY_EPG':0x16d,
	'KEY_PVR':0x16e,
	'KEY_MHP':0x16f,
	'KEY_LANGUAGE':0x170,
	'KEY_TITLE':0x171,
	'KEY_SUBTITLE':0x172,
	'KEY_ANGLE':0x173,
	'KEY_FULL_SCREEN':0x174,
	'KEY_MODE':0x175,
	'KEY_KEYBOARD':0x176,
	'KEY_ASPECT_RATIO':0x177,
	'KEY_PC':0x178,
	'KEY_TV':0x179,
	'KEY_TV2':0x17a,
	'KEY_VCR':0x17b,
	'KEY_VCR2':0x17c,
	'KEY_SAT':0x17d,
	'KEY_SAT2':0x17e,
	'KEY_CD':0x17f,
	'KEY_TAPE':0x180,
	'KEY_RADIO':0x181,
	'KEY_TUNER':0x182,
	'KEY_PLAYER':0x183,
	'KEY_TEXT':0x184,
	'KEY_DVD':0x185,
	'KEY_AUX':0x186,
	'KEY_MP3':0x187,
	'KEY_AUDIO':0x188,
	'KEY_VIDEO':0x189,
	'KEY_DIRECTORY':0x18a,
	'KEY_LIST':0x18b,
	'KEY_MEMO':0x18c,
	'KEY_CALENDAR':0x18d,
	'KEY_RED':0x18e,
	'KEY_GREEN':0x18f,
	'KEY_YELLOW':0x190,
	'KEY_BLUE':0x191,
	'KEY_CHANNELUP':0x192,
	'KEY_CHANNELDOWN':0x193,
	'KEY_FIRST':0x194,
	'KEY_LAST':0x195,
	'KEY_AB':0x196,
	'KEY_NEXT':0x197,
	'KEY_RESTART':0x198,
	'KEY_SLOW':0x199,
	'KEY_SHUFFLE':0x19a,
	'KEY_BREAK':0x19b,
	'KEY_PREVIOUS':0x19c,
	'KEY_DIGITS':0x19d,
	'KEY_TEEN':0x19e,
	'KEY_TWEN':0x19f,
	'KEY_VIDEOPHONE':0x1a0,
	'KEY_GAMES':0x1a1,
	'KEY_ZOOMIN':0x1a2,
	'KEY_ZOOMOUT':0x1a3,
	'KEY_ZOOMRESET':0x1a4,
	'KEY_WORDPROCESSOR':0x1a5,
	'KEY_EDITOR':0x1a6,
	'KEY_SPREADSHEET':0x1a7,
	'KEY_GRAPHICSEDITOR':0x1a8,
	'KEY_PRESENTATION':0x1a9,
	'KEY_DATABASE':0x1aa,
	'KEY_NEWS':0x1ab,
	'KEY_VOICEMAIL':0x1ac,
	'KEY_ADDRESSBOOK':0x1ad,
	'KEY_MESSENGER':0x1ae,
	'KEY_DISPLAYTOGGLE':0x1af,
	'KEY_SPELLCHECK':0x1b0,
	'KEY_LOGOFF':0x1b1,
	'KEY_DOLLAR':0x1b2,
	'KEY_EURO':0x1b3,
	'KEY_FRAMEBACK':0x1b4,
	'KEY_FRAMEFORWARD':0x1b5,
	'KEY_CONTEXT_MENU':0x1b6,
	'KEY_MEDIA_REPEAT':0x1b7,
	'KEY_10CHANNELSUP':0x1b8,
	'KEY_10CHANNELSDOWN':0x1b9,
	'KEY_IMAGES':0x1ba,
	'KEY_NOTIFICATION_CENTER':0x1bc,
	'KEY_PICKUP_PHONE':0x1bd,
	'KEY_HANGUP_PHONE':0x1be,
	'KEY_DEL_EOL':0x1c0,
	'KEY_DEL_EOS':0x1c1,
	'KEY_INS_LINE':0x1c2,
	'KEY_DEL_LINE':0x1c3,
	'KEY_FN':0x1d0,
	'KEY_FN_ESC':0x1d1,
	'KEY_FN_F1':0x1d2,
	'KEY_FN_F2':0x1d3,
	'KEY_FN_F3':0x1d4,
	'KEY_FN_F4':0x1d5,
	'KEY_FN_F5':0x1d6,
	'KEY_FN_F6':0x1d7,
	'KEY_FN_F7':0x1d8,
	'KEY_FN_F8':0x1d9,
	'KEY_FN_F9':0x1da,
	'KEY_FN_F10':0x1db,
	'KEY_FN_F11':0x1dc,
	'KEY_FN_F12':0x1dd,
	'KEY_FN_1':0x1de,
	'KEY_FN_2':0x1df,
	'KEY_FN_D':0x1e0,
	'KEY_FN_E':0x1e1,
	'KEY_FN_F':0x1e2,
	'KEY_FN_S':0x1e3,
	'KEY_FN_B':0x1e4,
	'KEY_FN_RIGHT_SHIFT':0x1e5,
	'KEY_BRL_DOT1':0x1f1,
	'KEY_BRL_DOT2':0x1f2,
	'KEY_BRL_DOT3':0x1f3,
	'KEY_BRL_DOT4':0x1f4,
	'KEY_BRL_DOT5':0x1f5,
	'KEY_BRL_DOT6':0x1f6,
	'KEY_BRL_DOT7':0x1f7,
	'KEY_BRL_DOT8':0x1f8,
	'KEY_BRL_DOT9':0x1f9,
	'KEY_BRL_DOT10':0x1fa,
	'KEY_NUMERIC_0':0x200,
	'KEY_NUMERIC_1':0x201,
	'KEY_NUMERIC_2':0x202,
	'KEY_NUMERIC_3':0x203,
	'KEY_NUMERIC_4':0x204,
	'KEY_NUMERIC_5':0x205,
	'KEY_NUMERIC_6':0x206,
	'KEY_NUMERIC_7':0x207,
	'KEY_NUMERIC_8':0x208,
	'KEY_NUMERIC_9':0x209,
	'KEY_NUMERIC_STAR':0x20a,
	'KEY_NUMERIC_POUND':0x20b,
	'KEY_NUMERIC_A':0x20c,
	'KEY_NUMERIC_B':0x20d,
	'KEY_NUMERIC_C':0x20e,
	'KEY_NUMERIC_D':0x20f,
	'KEY_CAMERA_FOCUS':0x210,
	'KEY_WPS_BUTTON':0x211,
	'KEY_TOUCHPAD_TOGGLE':0x212,
	'KEY_TOUCHPAD_ON':0x213,
	'KEY_TOUCHPAD_OFF':0x214,
	'KEY_CAMERA_ZOOMIN':0x215,
	'KEY_CAMERA_ZOOMOUT':0x216,
	'KEY_CAMERA_UP':0x217,
	'KEY_CAMERA_DOWN':0x218,
	'KEY_CAMERA_LEFT':0x219,
	'KEY_CAMERA_RIGHT':0x21a,
	'KEY_ATTENDANT_ON':0x21b,
	'KEY_ATTENDANT_OFF':0x21c,
	'KEY_ATTENDANT_TOGGLE':0x21d,
	'KEY_LIGHTS_TOGGLE':0x21e,
	'KEY_ALS_TOGGLE':0x230,
	'KEY_ROTATE_LOCK_TOGGLE':0x231,
	'KEY_BUTTONCONFIG':0x240,
	'KEY_TASKMANAGER':0x241,
	'KEY_JOURNAL':0x242,
	'KEY_CONTROLPANEL':0x243,
	'KEY_APPSELECT':0x244,
	'KEY_SCREENSAVER':0x245,
	'KEY_VOICECOMMAND':0x246,
	'KEY_ASSISTANT':0x247,
	'KEY_KBD_LAYOUT_NEXT':0x248,
	'KEY_EMOJI_PICKER':0x249,
	'KEY_DICTATE':0x24a,
	'KEY_BRIGHTNESS_MIN':0x250,
	'KEY_BRIGHTNESS_MAX':0x251,
	'KEY_KBDINPUTASSIST_PREV':0x260,
	'KEY_KBDINPUTASSIST_NEXT':0x261,
	'KEY_KBDINPUTASSIST_PREVGROUP':0x262,
	'KEY_KBDINPUTASSIST_NEXTGROUP':0x263,
	'KEY_KBDINPUTASSIST_ACCEPT':0x264,
	'KEY_KBDINPUTASSIST_CANCEL':0x265,
	'KEY_RIGHT_UP':0x266,
	'KEY_RIGHT_DOWN':0x267,
	'KEY_LEFT_UP':0x268,
	'KEY_LEFT_DOWN':0x269,
	'KEY_ROOT_MENU':0x26a,
	'KEY_MEDIA_TOP_MENU':0x26b,
	'KEY_NUMERIC_11':0x26c,
	'KEY_NUMERIC_12':0x26d,
	'KEY_AUDIO_DESC':0x26e,
	'KEY_3D_MODE':0x26f,
	'KEY_NEXT_FAVORITE':0x270,
	'KEY_STOP_RECORD':0x271,
	'KEY_PAUSE_RECORD':0x272,
	'KEY_VOD':0x273,
	'KEY_UNMUTE':0x274,
	'KEY_FASTREVERSE':0x275,
	'KEY_SLOWREVERSE':0x276,
	'KEY_DATA':0x277,
	'KEY_ONSCREEN_KEYBOARD':0x278,
	'KEY_PRIVACY_SCREEN_TOGGLE':0x279,
	'KEY_SELECTIVE_SCREENSHOT':0x27a,
	'KEY_NEXT_ELEMENT':0x27b,
	'KEY_PREVIOUS_ELEMENT':0x27c,
	'KEY_AUTOPILOT_ENGAGE_TOGGLE':0x27d,
	'KEY_MARK_WAYPOINT':0x27e,
	'KEY_SOS':0x27f,
	'KEY_NAV_CHART':0x280,
	'KEY_FISHING_CHART':0x281,
	'KEY_SINGLE_RANGE_RADAR':0x282,
	'KEY_DUAL_RANGE_RADAR':0x283,
	'KEY_RADAR_OVERLAY':0x284,
	'KEY_TRADITIONAL_SONAR':0x285,
	'KEY_CLEARVU_SONAR':0x286,
	'KEY_SIDEVU_SONAR':0x287,
	'KEY_NAV_INFO':0x288,
	'KEY_BRIGHTNESS_MENU':0x289,
	'KEY_MACRO1':0x290,
	'KEY_MACRO2':0x291,
	'KEY_MACRO3':0x292,
	'KEY_MACRO4':0x293,
	'KEY_MACRO5':0x294,
	'KEY_MACRO6':0x295,
	'KEY_MACRO7':0x296,
	'KEY_MACRO8':0x297,
	'KEY_MACRO9':0x298,
	'KEY_MACRO10':0x299,
	'KEY_MACRO11':0x29a,
	'KEY_MACRO12':0x29b,
	'KEY_MACRO13':0x29c,
	'KEY_MACRO14':0x29d,
	'KEY_MACRO15':0x29e,
	'KEY_MACRO16':0x29f,
	'KEY_MACRO17':0x2a0,
	'KEY_MACRO18':0x2a1,
	'KEY_MACRO19':0x2a2,
	'KEY_MACRO20':0x2a3,
	'KEY_MACRO21':0x2a4,
	'KEY_MACRO22':0x2a5,
	'KEY_MACRO23':0x2a6,
	'KEY_MACRO24':0x2a7,
	'KEY_MACRO25':0x2a8,
	'KEY_MACRO26':0x2a9,
	'KEY_MACRO27':0x2aa,
	'KEY_MACRO28':0x2ab,
	'KEY_MACRO29':0x2ac,
	'KEY_MACRO30':0x2ad,
	'KEY_MACRO_RECORD_START':0x2b0,
	'KEY_MACRO_RECORD_STOP':0x2b1,
	'KEY_MACRO_PRESET_CYCLE':0x2b2,
	'KEY_MACRO_PRESET1':0x2b3,
	'KEY_MACRO_PRESET2':0x2b4,
	'KEY_MACRO_PRESET3':0x2b5,
	'KEY_KBD_LCD_MENU1':0x2b8,
	'KEY_KBD_LCD_MENU2':0x2b9,
	'KEY_KBD_LCD_MENU3':0x2ba,
	'KEY_KBD_LCD_MENU4':0x2bb,
	'KEY_KBD_LCD_MENU5':0x2bc,
	'KEY_MAX':0x2ff,
}

linux_ev_code_to_name_lookup = {
	0:'KEY_RESERVED',
	1:'KEY_ESC',
	2:'KEY_1',
	3:'KEY_2',
	4:'KEY_3',
	5:'KEY_4',
	6:'KEY_5',
	7:'KEY_6',
	8:'KEY_7',
	9:'KEY_8',
	10:'KEY_9',
	11:'KEY_0',
	12:'KEY_MINUS',
	13:'KEY_EQUAL',
	14:'KEY_BACKSPACE',
	15:'KEY_TAB',
	16:'KEY_Q',
	17:'KEY_W',
	18:'KEY_E',
	19:'KEY_R',
	20:'KEY_T',
	21:'KEY_Y',
	22:'KEY_U',
	23:'KEY_I',
	24:'KEY_O',
	25:'KEY_P',
	26:'KEY_LEFTBRACE',
	27:'KEY_RIGHTBRACE',
	28:'KEY_ENTER',
	29:'KEY_LEFTCTRL',
	30:'KEY_A',
	31:'KEY_S',
	32:'KEY_D',
	33:'KEY_F',
	34:'KEY_G',
	35:'KEY_H',
	36:'KEY_J',
	37:'KEY_K',
	38:'KEY_L',
	39:'KEY_SEMICOLON',
	40:'KEY_APOSTROPHE',
	41:'KEY_GRAVE',
	42:'KEY_LEFTSHIFT',
	43:'KEY_BACKSLASH',
	44:'KEY_Z',
	45:'KEY_X',
	46:'KEY_C',
	47:'KEY_V',
	48:'KEY_B',
	49:'KEY_N',
	50:'KEY_M',
	51:'KEY_COMMA',
	52:'KEY_DOT',
	53:'KEY_SLASH',
	54:'KEY_RIGHTSHIFT',
	55:'KEY_KPASTERISK',
	56:'KEY_LEFTALT',
	57:'KEY_SPACE',
	58:'KEY_CAPSLOCK',
	59:'KEY_F1',
	60:'KEY_F2',
	61:'KEY_F3',
	62:'KEY_F4',
	63:'KEY_F5',
	64:'KEY_F6',
	65:'KEY_F7',
	66:'KEY_F8',
	67:'KEY_F9',
	68:'KEY_F10',
	69:'KEY_NUMLOCK',
	70:'KEY_SCROLLLOCK',
	71:'KEY_KP7',
	72:'KEY_KP8',
	73:'KEY_KP9',
	74:'KEY_KPMINUS',
	75:'KEY_KP4',
	76:'KEY_KP5',
	77:'KEY_KP6',
	78:'KEY_KPPLUS',
	79:'KEY_KP1',
	80:'KEY_KP2',
	81:'KEY_KP3',
	82:'KEY_KP0',
	83:'KEY_KPDOT',
	85:'KEY_ZENKAKUHANKAKU',
	86:'KEY_102ND',
	87:'KEY_F11',
	88:'KEY_F12',
	89:'KEY_RO',
	90:'KEY_KATAKANA',
	91:'KEY_HIRAGANA',
	92:'KEY_HENKAN',
	93:'KEY_KATAKANAHIRAGANA',
	94:'KEY_MUHENKAN',
	95:'KEY_KPJPCOMMA',
	96:'KEY_KPENTER',
	97:'KEY_RIGHTCTRL',
	98:'KEY_KPSLASH',
	99:'KEY_SYSRQ',
	100:'KEY_RIGHTALT',
	101:'KEY_LINEFEED',
	102:'KEY_HOME',
	103:'KEY_UP',
	104:'KEY_PAGEUP',
	105:'KEY_LEFT',
	106:'KEY_RIGHT',
	107:'KEY_END',
	108:'KEY_DOWN',
	109:'KEY_PAGEDOWN',
	110:'KEY_INSERT',
	111:'KEY_DELETE',
	112:'KEY_MACRO',
	113:'KEY_MUTE',
	114:'KEY_VOLUMEDOWN',
	115:'KEY_VOLUMEUP',
	116:'KEY_POWER',
	117:'KEY_KPEQUAL',
	118:'KEY_KPPLUSMINUS',
	119:'KEY_PAUSE',
	120:'KEY_SCALE',
	121:'KEY_KPCOMMA',
	122:'KEY_HANGEUL',
	123:'KEY_HANJA',
	124:'KEY_YEN',
	125:'KEY_LEFTMETA',
	126:'KEY_RIGHTMETA',
	127:'KEY_COMPOSE',
	128:'KEY_STOP',
	129:'KEY_AGAIN',
	130:'KEY_PROPS',
	131:'KEY_UNDO',
	132:'KEY_FRONT',
	133:'KEY_COPY',
	134:'KEY_OPEN',
	135:'KEY_PASTE',
	136:'KEY_FIND',
	137:'KEY_CUT',
	138:'KEY_HELP',
	139:'KEY_MENU',
	140:'KEY_CALC',
	141:'KEY_SETUP',
	142:'KEY_SLEEP',
	143:'KEY_WAKEUP',
	144:'KEY_FILE',
	145:'KEY_SENDFILE',
	146:'KEY_DELETEFILE',
	147:'KEY_XFER',
	148:'KEY_PROG1',
	149:'KEY_PROG2',
	150:'KEY_WWW',
	151:'KEY_MSDOS',
	152:'KEY_COFFEE',
	153:'KEY_ROTATE_DISPLAY',
	154:'KEY_CYCLEWINDOWS',
	155:'KEY_MAIL',
	156:'KEY_BOOKMARKS',
	157:'KEY_COMPUTER',
	158:'KEY_BACK',
	159:'KEY_FORWARD',
	160:'KEY_CLOSECD',
	161:'KEY_EJECTCD',
	162:'KEY_EJECTCLOSECD',
	163:'KEY_NEXTSONG',
	164:'KEY_PLAYPAUSE',
	165:'KEY_PREVIOUSSONG',
	166:'KEY_STOPCD',
	167:'KEY_RECORD',
	168:'KEY_REWIND',
	169:'KEY_PHONE',
	170:'KEY_ISO',
	171:'KEY_CONFIG',
	172:'KEY_HOMEPAGE',
	173:'KEY_REFRESH',
	174:'KEY_EXIT',
	175:'KEY_MOVE',
	176:'KEY_EDIT',
	177:'KEY_SCROLLUP',
	178:'KEY_SCROLLDOWN',
	179:'KEY_KPLEFTPAREN',
	180:'KEY_KPRIGHTPAREN',
	181:'KEY_NEW',
	182:'KEY_REDO',
	183:'KEY_F13',
	184:'KEY_F14',
	185:'KEY_F15',
	186:'KEY_F16',
	187:'KEY_F17',
	188:'KEY_F18',
	189:'KEY_F19',
	190:'KEY_F20',
	191:'KEY_F21',
	192:'KEY_F22',
	193:'KEY_F23',
	194:'KEY_F24',
	200:'KEY_PLAYCD',
	201:'KEY_PAUSECD',
	202:'KEY_PROG3',
	203:'KEY_PROG4',
	204:'KEY_ALL_APPLICATIONS',
	205:'KEY_SUSPEND',
	206:'KEY_CLOSE',
	207:'KEY_PLAY',
	208:'KEY_FASTFORWARD',
	209:'KEY_BASSBOOST',
	210:'KEY_PRINT',
	211:'KEY_HP',
	212:'KEY_CAMERA',
	213:'KEY_SOUND',
	214:'KEY_QUESTION',
	215:'KEY_EMAIL',
	216:'KEY_CHAT',
	217:'KEY_SEARCH',
	218:'KEY_CONNECT',
	219:'KEY_FINANCE',
	220:'KEY_SPORT',
	221:'KEY_SHOP',
	222:'KEY_ALTERASE',
	223:'KEY_CANCEL',
	224:'KEY_BRIGHTNESSDOWN',
	225:'KEY_BRIGHTNESSUP',
	226:'KEY_MEDIA',
	227:'KEY_SWITCHVIDEOMODE',
	228:'KEY_KBDILLUMTOGGLE',
	229:'KEY_KBDILLUMDOWN',
	230:'KEY_KBDILLUMUP',
	231:'KEY_SEND',
	232:'KEY_REPLY',
	233:'KEY_FORWARDMAIL',
	234:'KEY_SAVE',
	235:'KEY_DOCUMENTS',
	236:'KEY_BATTERY',
	237:'KEY_BLUETOOTH',
	238:'KEY_WLAN',
	239:'KEY_UWB',
	240:'KEY_UNKNOWN',
	241:'KEY_VIDEO_NEXT',
	242:'KEY_VIDEO_PREV',
	243:'KEY_BRIGHTNESS_CYCLE',
	244:'KEY_BRIGHTNESS_AUTO',
	245:'KEY_DISPLAY_OFF',
	246:'KEY_WWAN',
	247:'KEY_RFKILL',
	248:'KEY_MICMUTE',
	0x160:'KEY_OK',
	0x161:'KEY_SELECT',
	0x162:'KEY_GOTO',
	0x163:'KEY_CLEAR',
	0x164:'KEY_POWER2',
	0x165:'KEY_OPTION',
	0x166:'KEY_INFO',
	0x167:'KEY_TIME',
	0x168:'KEY_VENDOR',
	0x169:'KEY_ARCHIVE',
	0x16a:'KEY_PROGRAM',
	0x16b:'KEY_CHANNEL',
	0x16c:'KEY_FAVORITES',
	0x16d:'KEY_EPG',
	0x16e:'KEY_PVR',
	0x16f:'KEY_MHP',
	0x170:'KEY_LANGUAGE',
	0x171:'KEY_TITLE',
	0x172:'KEY_SUBTITLE',
	0x173:'KEY_ANGLE',
	0x174:'KEY_FULL_SCREEN',
	0x175:'KEY_MODE',
	0x176:'KEY_KEYBOARD',
	0x177:'KEY_ASPECT_RATIO',
	0x178:'KEY_PC',
	0x179:'KEY_TV',
	0x17a:'KEY_TV2',
	0x17b:'KEY_VCR',
	0x17c:'KEY_VCR2',
	0x17d:'KEY_SAT',
	0x17e:'KEY_SAT2',
	0x17f:'KEY_CD',
	0x180:'KEY_TAPE',
	0x181:'KEY_RADIO',
	0x182:'KEY_TUNER',
	0x183:'KEY_PLAYER',
	0x184:'KEY_TEXT',
	0x185:'KEY_DVD',
	0x186:'KEY_AUX',
	0x187:'KEY_MP3',
	0x188:'KEY_AUDIO',
	0x189:'KEY_VIDEO',
	0x18a:'KEY_DIRECTORY',
	0x18b:'KEY_LIST',
	0x18c:'KEY_MEMO',
	0x18d:'KEY_CALENDAR',
	0x18e:'KEY_RED',
	0x18f:'KEY_GREEN',
	0x190:'KEY_YELLOW',
	0x191:'KEY_BLUE',
	0x192:'KEY_CHANNELUP',
	0x193:'KEY_CHANNELDOWN',
	0x194:'KEY_FIRST',
	0x195:'KEY_LAST',
	0x196:'KEY_AB',
	0x197:'KEY_NEXT',
	0x198:'KEY_RESTART',
	0x199:'KEY_SLOW',
	0x19a:'KEY_SHUFFLE',
	0x19b:'KEY_BREAK',
	0x19c:'KEY_PREVIOUS',
	0x19d:'KEY_DIGITS',
	0x19e:'KEY_TEEN',
	0x19f:'KEY_TWEN',
	0x1a0:'KEY_VIDEOPHONE',
	0x1a1:'KEY_GAMES',
	0x1a2:'KEY_ZOOMIN',
	0x1a3:'KEY_ZOOMOUT',
	0x1a4:'KEY_ZOOMRESET',
	0x1a5:'KEY_WORDPROCESSOR',
	0x1a6:'KEY_EDITOR',
	0x1a7:'KEY_SPREADSHEET',
	0x1a8:'KEY_GRAPHICSEDITOR',
	0x1a9:'KEY_PRESENTATION',
	0x1aa:'KEY_DATABASE',
	0x1ab:'KEY_NEWS',
	0x1ac:'KEY_VOICEMAIL',
	0x1ad:'KEY_ADDRESSBOOK',
	0x1ae:'KEY_MESSENGER',
	0x1af:'KEY_DISPLAYTOGGLE',
	0x1b0:'KEY_SPELLCHECK',
	0x1b1:'KEY_LOGOFF',
	0x1b2:'KEY_DOLLAR',
	0x1b3:'KEY_EURO',
	0x1b4:'KEY_FRAMEBACK',
	0x1b5:'KEY_FRAMEFORWARD',
	0x1b6:'KEY_CONTEXT_MENU',
	0x1b7:'KEY_MEDIA_REPEAT',
	0x1b8:'KEY_10CHANNELSUP',
	0x1b9:'KEY_10CHANNELSDOWN',
	0x1ba:'KEY_IMAGES',
	0x1bc:'KEY_NOTIFICATION_CENTER',
	0x1bd:'KEY_PICKUP_PHONE',
	0x1be:'KEY_HANGUP_PHONE',
	0x1c0:'KEY_DEL_EOL',
	0x1c1:'KEY_DEL_EOS',
	0x1c2:'KEY_INS_LINE',
	0x1c3:'KEY_DEL_LINE',
	0x1d0:'KEY_FN',
	0x1d1:'KEY_FN_ESC',
	0x1d2:'KEY_FN_F1',
	0x1d3:'KEY_FN_F2',
	0x1d4:'KEY_FN_F3',
	0x1d5:'KEY_FN_F4',
	0x1d6:'KEY_FN_F5',
	0x1d7:'KEY_FN_F6',
	0x1d8:'KEY_FN_F7',
	0x1d9:'KEY_FN_F8',
	0x1da:'KEY_FN_F9',
	0x1db:'KEY_FN_F10',
	0x1dc:'KEY_FN_F11',
	0x1dd:'KEY_FN_F12',
	0x1de:'KEY_FN_1',
	0x1df:'KEY_FN_2',
	0x1e0:'KEY_FN_D',
	0x1e1:'KEY_FN_E',
	0x1e2:'KEY_FN_F',
	0x1e3:'KEY_FN_S',
	0x1e4:'KEY_FN_B',
	0x1e5:'KEY_FN_RIGHT_SHIFT',
	0x1f1:'KEY_BRL_DOT1',
	0x1f2:'KEY_BRL_DOT2',
	0x1f3:'KEY_BRL_DOT3',
	0x1f4:'KEY_BRL_DOT4',
	0x1f5:'KEY_BRL_DOT5',
	0x1f6:'KEY_BRL_DOT6',
	0x1f7:'KEY_BRL_DOT7',
	0x1f8:'KEY_BRL_DOT8',
	0x1f9:'KEY_BRL_DOT9',
	0x1fa:'KEY_BRL_DOT10',
	0x200:'KEY_NUMERIC_0',
	0x201:'KEY_NUMERIC_1',
	0x202:'KEY_NUMERIC_2',
	0x203:'KEY_NUMERIC_3',
	0x204:'KEY_NUMERIC_4',
	0x205:'KEY_NUMERIC_5',
	0x206:'KEY_NUMERIC_6',
	0x207:'KEY_NUMERIC_7',
	0x208:'KEY_NUMERIC_8',
	0x209:'KEY_NUMERIC_9',
	0x20a:'KEY_NUMERIC_STAR',
	0x20b:'KEY_NUMERIC_POUND',
	0x20c:'KEY_NUMERIC_A',
	0x20d:'KEY_NUMERIC_B',
	0x20e:'KEY_NUMERIC_C',
	0x20f:'KEY_NUMERIC_D',
	0x210:'KEY_CAMERA_FOCUS',
	0x211:'KEY_WPS_BUTTON',
	0x212:'KEY_TOUCHPAD_TOGGLE',
	0x213:'KEY_TOUCHPAD_ON',
	0x214:'KEY_TOUCHPAD_OFF',
	0x215:'KEY_CAMERA_ZOOMIN',
	0x216:'KEY_CAMERA_ZOOMOUT',
	0x217:'KEY_CAMERA_UP',
	0x218:'KEY_CAMERA_DOWN',
	0x219:'KEY_CAMERA_LEFT',
	0x21a:'KEY_CAMERA_RIGHT',
	0x21b:'KEY_ATTENDANT_ON',
	0x21c:'KEY_ATTENDANT_OFF',
	0x21d:'KEY_ATTENDANT_TOGGLE',
	0x21e:'KEY_LIGHTS_TOGGLE',
	0x230:'KEY_ALS_TOGGLE',
	0x231:'KEY_ROTATE_LOCK_TOGGLE',
	0x240:'KEY_BUTTONCONFIG',
	0x241:'KEY_TASKMANAGER',
	0x242:'KEY_JOURNAL',
	0x243:'KEY_CONTROLPANEL',
	0x244:'KEY_APPSELECT',
	0x245:'KEY_SCREENSAVER',
	0x246:'KEY_VOICECOMMAND',
	0x247:'KEY_ASSISTANT',
	0x248:'KEY_KBD_LAYOUT_NEXT',
	0x249:'KEY_EMOJI_PICKER',
	0x24a:'KEY_DICTATE',
	0x250:'KEY_BRIGHTNESS_MIN',
	0x251:'KEY_BRIGHTNESS_MAX',
	0x260:'KEY_KBDINPUTASSIST_PREV',
	0x261:'KEY_KBDINPUTASSIST_NEXT',
	0x262:'KEY_KBDINPUTASSIST_PREVGROUP',
	0x263:'KEY_KBDINPUTASSIST_NEXTGROUP',
	0x264:'KEY_KBDINPUTASSIST_ACCEPT',
	0x265:'KEY_KBDINPUTASSIST_CANCEL',
	0x266:'KEY_RIGHT_UP',
	0x267:'KEY_RIGHT_DOWN',
	0x268:'KEY_LEFT_UP',
	0x269:'KEY_LEFT_DOWN',
	0x26a:'KEY_ROOT_MENU',
	0x26b:'KEY_MEDIA_TOP_MENU',
	0x26c:'KEY_NUMERIC_11',
	0x26d:'KEY_NUMERIC_12',
	0x26e:'KEY_AUDIO_DESC',
	0x26f:'KEY_3D_MODE',
	0x270:'KEY_NEXT_FAVORITE',
	0x271:'KEY_STOP_RECORD',
	0x272:'KEY_PAUSE_RECORD',
	0x273:'KEY_VOD',
	0x274:'KEY_UNMUTE',
	0x275:'KEY_FASTREVERSE',
	0x276:'KEY_SLOWREVERSE',
	0x277:'KEY_DATA',
	0x278:'KEY_ONSCREEN_KEYBOARD',
	0x279:'KEY_PRIVACY_SCREEN_TOGGLE',
	0x27a:'KEY_SELECTIVE_SCREENSHOT',
	0x27b:'KEY_NEXT_ELEMENT',
	0x27c:'KEY_PREVIOUS_ELEMENT',
	0x27d:'KEY_AUTOPILOT_ENGAGE_TOGGLE',
	0x27e:'KEY_MARK_WAYPOINT',
	0x27f:'KEY_SOS',
	0x280:'KEY_NAV_CHART',
	0x281:'KEY_FISHING_CHART',
	0x282:'KEY_SINGLE_RANGE_RADAR',
	0x283:'KEY_DUAL_RANGE_RADAR',
	0x284:'KEY_RADAR_OVERLAY',
	0x285:'KEY_TRADITIONAL_SONAR',
	0x286:'KEY_CLEARVU_SONAR',
	0x287:'KEY_SIDEVU_SONAR',
	0x288:'KEY_NAV_INFO',
	0x289:'KEY_BRIGHTNESS_MENU',
	0x290:'KEY_MACRO1',
	0x291:'KEY_MACRO2',
	0x292:'KEY_MACRO3',
	0x293:'KEY_MACRO4',
	0x294:'KEY_MACRO5',
	0x295:'KEY_MACRO6',
	0x296:'KEY_MACRO7',
	0x297:'KEY_MACRO8',
	0x298:'KEY_MACRO9',
	0x299:'KEY_MACRO10',
	0x29a:'KEY_MACRO11',
	0x29b:'KEY_MACRO12',
	0x29c:'KEY_MACRO13',
	0x29d:'KEY_MACRO14',
	0x29e:'KEY_MACRO15',
	0x29f:'KEY_MACRO16',
	0x2a0:'KEY_MACRO17',
	0x2a1:'KEY_MACRO18',
	0x2a2:'KEY_MACRO19',
	0x2a3:'KEY_MACRO20',
	0x2a4:'KEY_MACRO21',
	0x2a5:'KEY_MACRO22',
	0x2a6:'KEY_MACRO23',
	0x2a7:'KEY_MACRO24',
	0x2a8:'KEY_MACRO25',
	0x2a9:'KEY_MACRO26',
	0x2aa:'KEY_MACRO27',
	0x2ab:'KEY_MACRO28',
	0x2ac:'KEY_MACRO29',
	0x2ad:'KEY_MACRO30',
	0x2b0:'KEY_MACRO_RECORD_START',
	0x2b1:'KEY_MACRO_RECORD_STOP',
	0x2b2:'KEY_MACRO_PRESET_CYCLE',
	0x2b3:'KEY_MACRO_PRESET1',
	0x2b4:'KEY_MACRO_PRESET2',
	0x2b5:'KEY_MACRO_PRESET3',
	0x2b8:'KEY_KBD_LCD_MENU1',
	0x2b9:'KEY_KBD_LCD_MENU2',
	0x2ba:'KEY_KBD_LCD_MENU3',
	0x2bb:'KEY_KBD_LCD_MENU4',
	0x2bc:'KEY_KBD_LCD_MENU5',
	0x2ff:'KEY_MAX',
}

scancode_set3_to_map = {
	'KEY_A':0x1C,
	'KEY_B':0x32,
	'KEY_C':0x21,
	'KEY_D':0x23,
	'KEY_E':0x24,
	'KEY_F':0x2B,
	'KEY_G':0x34,
	'KEY_H':0x33,
	'KEY_I':0x43,
	'KEY_J':0x3B,
	'KEY_K':0x42,
	'KEY_L':0x4B,
	'KEY_M':0x3A,
	'KEY_N':0x31,
	'KEY_O':0x44,
	'KEY_P':0x4D,
	'KEY_Q':0x15,
	'KEY_R':0x2D,
	'KEY_S':0x1B,
	'KEY_T':0x2C,
	'KEY_U':0x3C,
	'KEY_V':0x2A,
	'KEY_W':0x1D,
	'KEY_X':0x22,
	'KEY_Y':0x35,
	'KEY_Z':0x1A,
	'KEY_0':0x45,
	'KEY_1':0x16,
	'KEY_2':0x1E,
	'KEY_3':0x26,
	'KEY_4':0x25,
	'KEY_5':0x2E,
	'KEY_6':0x36,
	'KEY_7':0x3D,
	'KEY_8':0x3E,
	'KEY_9':0x46,
	'KEY_F1':0x7,
	'KEY_F2':0x0F,
	'KEY_F3':0x17,
	'KEY_F4':0x1F,
	'KEY_F5':0x27,
	'KEY_F6':0x2F,
	'KEY_F7':0x37,
	'KEY_F8':0x3F,
	'KEY_F9':0x47,
	'KEY_F10':0x4F,
	'KEY_F11':0x56,
	'KEY_F12':0x5E,
	'KEY_KP0':0x70,
	'KEY_KP1':0x69,
	'KEY_KP2':0x72,
	'KEY_KP3':0x7A,
	'KEY_KP4':0x6B,
	'KEY_KP5':0x73,
	'KEY_KP6':0x74,
	'KEY_KP7':0x6C,
	'KEY_KP8':0x75,
	'KEY_KP9':0x7D,
	'KEY_MINUS':0x4E,
	'KEY_EQUAL':0x55,
	'KEY_BACKSPACE':0x66,
	'KEY_SPACE':0x29,
	'KEY_TAB':0x0D,
	'KEY_CAPSLOCK':0x14,
	'KEY_LEFTSHIFT':0x12,
	'KEY_LEFTCTRL':0x11,
	'KEY_LEFTMETA':0x8B,
	'KEY_LEFTALT':0x19,
	'KEY_RIGHTSHIFT':0x59,
	'KEY_RIGHTCTRL':0x58,
	'KEY_RIGHTMETA':0x8C,
	'KEY_RIGHTALT':0x39,
	'KEY_COMPOSE':0x8D,
	'KEY_ENTER':0x5A,
	'KEY_ESC':0x8,
	'KEY_SYSRQ':0x57,
	'KEY_SCROLLLOCK':0x5F,
	'KEY_PAUSE':0x62,
	'KEY_INSERT':0x67,
	'KEY_HOME':0x6E,
	'KEY_PAGEUP':0x6F,
	'KEY_DELETE':0x64,
	'KEY_END':0x65,
	'KEY_PAGEDOWN':0x6D,
	'KEY_UP':0x63,
	'KEY_LEFT':0x61,
	'KEY_DOWN':0x60,
	'KEY_RIGHT':0x6A,
	'KEY_NUMLOCK':0x76,
	'KEY_GRAVE':0x0E,
	'KEY_BACKSLASH':0x5C,
	'KEY_LEFTBRACE':0x54,
	'KEY_RIGHTBRACE':0x5B,
	'KEY_SEMICOLON':0x4C,
	'KEY_COMMA':0x41,
	'KEY_APOSTROPHE':0x52,
	'KEY_DOT':0x49,
	'KEY_SLASH':0x4A,
	'KEY_KPSLASH':0x4A,
	'KEY_KPASTERISK':0x7E,
	'KEY_KPMINUS':0x4E,
	'KEY_KPPLUS':0x7C,
	'KEY_KPENTER':0x79,
	'KEY_KPDOT':0x71,
}

CODE_UNUSED = 0;

for x in range(256):
	ev_name = linux_ev_code_to_name_lookup.get(x, 'KEY_UNUSED')
	set3_code = scancode_set3_to_map.get(ev_name, 'CODE_UNUSED')
	# print(x, ev_name, set3_code)
	if set3_code != 'CODE_UNUSED':
		set3_code = hex(set3_code)
	print(f"{set3_code}, // {ev_name}    {x}")
