dekuNukem/USB4VC/user_program/usb4vc_oled.py

from demo_opts import get_device
from luma.core.render import canvas
from PIL import ImageFont

OLED_WIDTH = 128
OLED_HEIGHT = 32

my_arg = ['--display', 'ssd1306', '--interface', 'spi', '--spi-port', '0', '--spi-device', '1', '--gpio-reset', '6', '--gpio-data-command', '5', '--width', str(OLED_WIDTH), '--height', str(OLED_HEIGHT), '--spi-bus-speed', '2000000']
oled_device = get_device(my_arg)

"""
OLED for USB4VC
128*32

3 font sizes available, regular/large: ProggyTiny.ttf, medium: ChiKareGo2.ttf.

regular ProggyTiny:
16 point, 3 lines, y=0, 10, 20

large type ProggyTiny:
32 point, 2 lines (1 large + 1 regular), y=0, 20

medium type ChiKareGo2:
16 point, 2 lines, y=0, 15 

characters per line:
regular font: 21 
medium font: 16
large font: 11

int(sys.argv[1])
sh sync.sh; ssh -t pi@192.168.1.56 "pkill python3;cd ~/usb4vc;python3 usb4vc_main.py"
"""

font_regular = ImageFont.truetype("ProggyTiny.ttf", 16)
font_medium = ImageFont.truetype("ChiKareGo2.ttf", 16)
font_large = ImageFont.truetype("ProggyTiny.ttf", 32)

max_char_per_line = {font_regular:21, font_medium:17, font_large:11}
width_per_char = {font_regular:6, font_medium:7, font_large:12}

def oled_print_centered(text, font, y, this_canvas):
    text = text.strip()[:max_char_per_line[font]]
    start_x = int((OLED_WIDTH - (len(text) * width_per_char[font]))/2)
    if start_x < 0:
        start_x = 0
    this_canvas.text((start_x, y), text, font=font, fill="white")
