dekuNukem/USB4VC/firmware/apple_lisa_mac_adb/Inc/delay_us.h

#ifndef __DELAYUS_H
#define __DELAYUS_H

#ifdef __cplusplus
 extern "C" {
#endif 

#include "stm32f0xx_hal.h"

void delay_us_init(TIM_HandleTypeDef* htim_base);
void delay_us(uint32_t delay);
uint32_t micros(void);

#ifdef __cplusplus
}
#endif

#endif
